DC801/BM-Badge/SD_Card/MAGE/docs_sources/docs/actions/LOOP_CAMERA_ALONG_GEOMETRY.md

# LOOP_CAMERA_ALONG_GEOMETRY

(might not work yet — instead, make a [null entity](../entity_types#null-entity) and lock the camera to it)

## Example JSON

```json
{
  "action": "LOOP_CAMERA_ALONG_GEOMETRY",
  "duration": 1000,
  "geometry": "vector object name"
}
```

## MGS Natlang

### Example

```mgs
script {
  loop camera along geometry "vector object name" over 1000ms;
}
```

### Dictionary entry

```
loop camera along geometry $geometry:string over $duration:duration (;)
```
