DC801/BM-Badge/SD_Card/MAGE/docs_sources/docs/actions/TELEPORT_CAMERA_TO_GEOMETRY.md

# TELEPORT_CAMERA_TO_GEOMETRY

Moves the camera to the first vertex of the specified [geometry object](../vector_objects).

## Example JSON

```json
{
  "action": "TELEPORT_CAMERA_TO_GEOMETRY",
  "geometry": "vector object name"
}
```

## MGS Natlang

### Example

```mgs
script {
  teleport camera to geometry "vector object name";
}
```

### Dictionary entry

```
teleport camera to geometry $geometry:string (;)
```
