DC801/BM-Badge/SD_Card/MAGE/scenario_source_files/mgs/ch2/ch2-PLANNING.md

# Chapter 2 planning

## Docs todos

- [ ] Turns out what makes a tile rotate weird when turning NSEW is whether the tile (whether it's a "character entity" or not) has an animation on it; not whether the tile has a Class/Type field value or whether it's listed in entity_types

## Generic work needing done

- [x] Make `go s` for `go south` an engine default alias (ditto for `sw` = `southwest`)
- [~] Tone down the alias logging in debug mode!
- [ ] Make the menu mage more chiseled (like last ch)
- [ ] Decide what to do with the null entity `door`, and be consistent about it
- [ ] Rename scripts so they're consistent
	- e.g. `ch2-interact-asdfasdf` should all be `interact-ch2-asdfasdf` -- or vice versa (pick one!)
- [x] Move Tiled files to the folders they should actually be (some entity JSON files are in the maps folder, etc.)
	- [x] And update all file paths in files that link to them, please!
- [ ] Turn off serial control during cutscenes
	- [ ] Determine which
	- [ ] Determine whether this should include all conversations
- [ ] For "failed" multiple choice responses, make the chunk of the dialog that gets repeated more logical and consistent
- [x] Check that every entity has an on_look script
- [x] Investigate and fix color pallet issues between tilesets (specifically grass in the castle/town tilesets, and the artifact cubby and the wall)
- [ ] Make aliases, e.g.:
	- [ ] `n` for `go north` (?)
	- [x] `i` for `inventory`
	- [x] `x`, `examine`, `l` for `look` etc.
- [~] ~~Make fuse system more interesting~~
	- [~] ~~Work out ≈ Cartesian product / Punnet squares for each grouping of combined items~~
	- [~] ~~Write something funny for each failed combo~~
	- (Re: above -- it's MVP now, and no time to change it much now)
	- [x] You need to fuse in person, at (one of the) the solder station(s)?
- [x] Make Lambda less hand-holdy at the beginning
	- [x] Explain `help` and `man` (both to reach Lambda and `man _`) and nothing else!
	- [ ] Did we go too far?? Make him hold more hands?
- [x] Put the "password" letters in the floor
	- [x] Take out the "look up" stuff
	- [x] Letters should spell AUTHENTICATE when spacially placed along the rooms they were found
	- [ ] Make sure the hint/context is ironclad!
- [x] Pair down the number of free computers in the place — gotta justify the need to build a weird one from scratch
- [ ] Change each individual "hide" script to set the object's on_tick to the "yeet" script instead so that all properties (not manually chosen ones) can be blanked in a uniform way
- [ ] Math book on_lock got skipped in RTFM room?

```
-------------------------------
|  /----\      -      CASTLE  |
|  |....|     /.\        MAP  |
|  ------   /..A..\           |
|           ---+---           |
|            |...|   -------  |
|   -----    |.U.|   |.T|H.|  |
|  /..E..\   |...|   --+-+--  |
|  \...../   |...|    |.N.|   |
|   --+--    --+--------+--   |
|   |.T.|    |.I.+...C....|   |
|   --+--------+-----------   |
|   |...A....+.T.|            |
|   -----------+----          |
|          |...E...|          |
|          ----+----          |
-------------------------------
```

## Specific work needing done

- [x] Teleport the player loading from save into the correct spot (overworld -> castle room #1)

## Story themes

- Chapter 2: Connections
	- Connecting past to future: sending ideas into the future, building long term communities, remembering lessons learned in the past
	- Connecting rooms to each other: building larger projects with cooperation, building/fixing infrastructure
	- Connecting people: allowing people to hear each other, build relationships; humans as social animals; networking leads to finding mentors and opportunities
	- The cost of isolation vs the cost of exposing oneself to bad actors
	- Connecting hardware: hardware is made up of smaller pieces, and many fixes are only a matter of connecting something to something else
	- AT THE END: Lambda is reconnected
- Chapter 3: Knowledge
	- Benefits of education
	- Learning to navigate the gray area rather than take a black and white answer at face value
	- Learning about one's environment
	- Leaning toolsets, how to best use everyday tools
	- Secrets to protect the vulnerable vs secrets to manipulate the vulnerable
	- IDEA: character named Chicago that speaks with that font

## Serial dialogs styles

- Before printing a fresh message to the serial console, show the serial dialog "spacer" -- this is currently a line break, a bunch of hyphens, and another line break. This makes it obvious where a new serial message begins.
- Empty serial messages must contain a single space or they will be ignored.

### Character conversations

- Identify speakers with `<color>SPEAKERNAME:</>` before their actual dialog message.
	- For `<color>`, use the speaker's color symbol (see below)
- Separate multiple speakers with an empty line.
- Additional paragraphs spoken by the same speaker should be indented with `\t`.
- Put an empty line between the last paragraph of dialog and a user input prompt.

### `on_look` scripts

- `look` must tell you things you can't ascertain from an entity's pixel art, scripting behavior, or dialog.
- Pay special attention to describing senses other than sight -- like smells, sounds -- but also broader information like the emotional atmosphere of a room and how people are acting around each other

See below for color choices.

#### Rooms

```mgs
look-ch2-roomname {
	show serial dialog spacer;
	show serial dialog {
		"You looked around the <c>NAME OF ROOM</>."
		"\t(description goes here)"
		"\t(extra paragraphs should also be tabbed, but try to avoid a lot of short paragraphs)"
		" "
	}
}
```

The extra line break at the end is only needed for places, since the exit list will follow the room's `on_look` script.

#### Entities

```mgs
look-ch2-roomname {
	show serial dialog spacer;
	show serial dialog {
		"You looked at <m>%EntityName%</>."
		// "You looked at the <m>%EntityName%</>." // for objects
		"\t(description goes here)"
		"\t(extra paragraphs should also be tabbed, but try to avoid a lot of short paragraphs)"
	}
}
```

Note the relative entity name for the label (i.e. wrapped in `%`s).

### Ansi Colors

- We can't know whether the user has a dark theme or a light theme, nor can we guarantee that all colors will be equally visible in their particular theme. Therefore, when needing arbitrary colors, prioritize them in this order:
	- Cyan/magenta (best)
	- Green/red
	- Blue/yellow (avoid)
	- Black/white (strong avoid)
- Do not use colors alone to convey information; if color coding something, also use other cues (capitalization, offsetting a word with with punctuation, etc.)
- Avoid using green/red as a point of contrast.
- Avoid using background colors or the "dim" style, since these are not as widely supported.
- Color symbols in ch2:
	- Magenta:
		- The village elders (the color of their robes)
		- Lambda
		- Any other person, really
	- Red:
		- The Big Bad
		- Anything unambiguously evil
	- Cyan:
		- The player (the color of mage's robe)
		- Inline serial commands (these should also be all caps)
		- Any calls to action for the player, akin to the above
		- The castle rooms (ch2 dungeon) (?)
			- Only the warp names are colored?
- In the web serial console, a styled section of text loses its styles after a newline character. As a workaround, reapply the style at the beginning of the first word that lost its styles.
- Currently, in the web build, the bell character is printed! (Like, as a boxy character, inline with other text.) Keep that in mind...
