DC801/BM-Badge/SD_Card/MAGE/editor/dependencies/tree-sitter-magegamescript/comparisons/mgs/ch2/ch2-map-PLANNING.md

# USB dungeon serial "map" (ideas)

```
Nethack-like
-------------------------------
|  /----\      -      CASTLE  |
|  |....|     /.\        MAP  |
|  ------   /.....\           |
|           -------           |
|            |...|   -------  |
|   -----    |...|   |.....|  |
|  /.....\   |...|   -------  |
|  \...../   |...|    |...|   |
|   -----    -------------|   |
|   |...|    |...|........|   |
|   -----------------------   |
|   |........|...|            |
|   |---------------          |
|          |...@...|          |
|          ---------          |
-------------------------------

 /----\      -
 | 99 |     / \
 ------   / 14  \
          -------  -------
  -----    |   |   |33|34|
 /     \   |13 |   -------
 \ 23  /   |   |    |32 |
  -----    --------------
  |22 |    |12 |    31  |
  |----------------------
  |   21   |11 |
  |---------------
         |   1   |
         ---------
```

## ROOMS

The room name (re: warping or other serial labelling) is what is contained within backtics.

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

### Entrance

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

### Admin Branch

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

### Industrial Area

21. `Workshop`
    - [~] Cutscene: Enter the room for the first time
    - [x] Inventory item: abacus (CPU part 2)
    - [x] Entity: Goose (with ribbon)
        - [ ] Should be involved with one of the puzzle items
    - [x] Entity: Jean-Paul - human-sized cockatiel; buds with Frankie
    - [x] Entity: Frankie - androgynous, Homestar Runner shirt-wearing tinkerer; buds with Jean-Paul
    - [x] SET: work room for fixing and making hardware (both old timey castle type hardware _and_ computer type hardware); disheveled, but not hopelessly so (everything is sort of in the right place, it's just all out at the moment)
22. `Server room`
    - [ ] Cutscene: Enter the room for the first time
    - [x] Inventory item: powersupply
    - [x] Entity: Scuzzy - generic conversation about the similarities between rooms in a building and components inside a computer
    - [x] Entity: C.K. Watt - gives you the power supply because it's extra
    - [x] SET: More cleanroom looking than the workshop
        - [x] Racks of machines
        - [x] Some computer buildery stuff (more computer, less electronics?)
23. `Power plant`
    - [x] Cutscene: Enter the room for the first time (not necessary)
    - [x] Inventory item: heatsink
    - [x] Entity: Tracy - generic engineer
    - [x] Entity: Rocco - to trade you the heat sink for a can of Cactus Cooler
    - [x] Entity: Helvetica - succubus, but you wouldn't know it from how she was acting; consummate professional engineer
    - [x] SET: Aiming for geothermal; whatever would sell that re: appearance

### Food

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

### The End

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

### Town

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

## ZONES

```
 0-------------------------------
 1|  /----\      -      CASTLE  |    99        14
 2|  |.@?.|     /.\        MAP  |    99        14
 3|  ------   /..@?.\           |    99        14
 4|           -------           |          13  14
 5|            |...|   -------  |          13              33  34
 6|   -----    |.@.|   |?@|@?|  |      23  13              33  34
 7|  /..@..\   |.?.|   -------  |      23  13          32  33  34
 8|  \..?../   |...|    |.@.|   |      23  13          32
 9|   -----    --------------   |  22  23  13  12  31  32
10|   |.@?|    |.@?|...@.?..|   |  22          12  31
11|   -----------------------   |  22  21  11  12  31
12|   |...@.?..|.@?|            |      21  11
13|   ----------------          |      21  11
14|          |...@...|          |          1
15|          ---------          |
16-------------------------------

with doors as pluses:
 0-------------------------------
 1|  /----\      -      CASTLE  |    99        14
 2|  |.@?.|     /.\        MAP  |    99        14
 3|  ------   /..@?.\           |    99        14
 4|           ---+---           |          13  14
 5|            |...|   -------  |          13              33  34
 6|   -----    |.@.|   |?@|@?|  |      23  13              33  34
 7|  /..@..\   |.?.|   --+-+--  |      23  13          32  33  34
 8|  \..?../   |...|    |.@.|   |      23  13          32
 9|   --+--    --+--------+--   |  22  23  13  12  31  32
10|   |.@?|    |.@?+...@.?..|   |  22          12  31
11|   --+--------+-----------   |  22  21  11  12  31
12|   |...@.?..+.@?|            |      21  11
13|   -----------+----          |      21  11
14|          |...@...|          |          1
15|          ----+----          |
16-------------------------------
```

## STORY PROGRESSION

(Only numbered items count as story flags)

Choose which "round" with the `ch2_storyflag_round` variable. Checkboxes refer to script scaffolding (the exact convos may be still unwritten); see `ch2-PLANNING.md` for the sprites checklist.

In debug mode, you can use the command `storyflag` to set this arbitrarily for testing purposes.

### Plot

Plot points implemented:

- INTRO (`ch2_storyflag_round` = 0)

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

- FIRST ROUND: normal (`ch2_storyflag_round` = 1)

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

- SECOND ROUND: abstract (`ch2_storyflag_round` = 2)

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

- THIRD ROUND: desperate (`ch2_storyflag_round` = 3)

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

- FINAL ROUND: software (`ch2_storyflag_round` = 4)

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

- AFTERWARD (`ch2_storyflag_round` = 5)
    - [x] Post-credits sequence: Alfonso mentions one of the Big Bad's powers that most people don't know about
    - [~] Go about the overworld now

### Village elder locations

ALL DONE!

- INTRO (`ch2_storyflag_round` = 0)
    - [x] All outside castle entrance
    - [x] All encouraging you
- FIRST ROUND: normal (`ch2_storyflag_round` = 1)
    - [x] Alfonso: in the library, getting distracted by random books on accident
    - [x] Jackob: in the library, in a staring contest with the goose
    - [x] Bert: in the inner sanctum, looking for the book they lost
    - Bert visits you
- SECOND ROUND: abstract (`ch2_storyflag_round` = 2)
    - [x] Alfonso: talking to Verthandi
    - [x] Jackob: in the bakery, shopping for fresh bread
- THIRD ROUND: desperate (`ch2_storyflag_round` = 3)
    - [x] Jackob in inner sanctum, worried about the time you are taking
    - [x] Alfonso in inner sanctum, worried about Bert
- FINAL ROUND: software (`ch2_storyflag_round` = 4)
    - [x] Jackob/Alfonso waiting outside
    - [x] Jackob/Alfonso urging you to finish
- AFTERWARD (`ch2_storyflag_round` = 5)
    - [x] In the main square
    - [x] Mention how you can have a break now
        - [x] If you haven't beaten part 1, Jackob invites you to do so now

### Villager dialog

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

- INTRO (`ch2_storyflag_round` = 0)
    - [ ] Villagers direct you to western dungeon (castle)
- FIRST ROUND: normal (`ch2_storyflag_round` <= 2)
    - [ ] Villagers ask how things are going
- THIRD ROUND: desperate (`ch2_storyflag_round` <= 4)
    - [ ] Player asks villages about Bert; they haven't seen him
- AFTERWARD (`ch2_storyflag_round` <= 5)
    - [ ] Speculate on next location: software!

Use this template:

```
if (variable ch2_storyflag_round is 0) {
	show dialog {
	// hint at western dungeon
	}
} else if (variable ch2_storyflag_round is <= 2) {
	show dialog {
	// asks how things are going
	}
} else if (variable ch2_storyflag_round is <= 4) {
	show dialog {
	// player asks after Bert; entity hasn't seen him
	}
} else {
	show dialog {
	// congratulate player for winning; speculate on next dungeon
	}
}
```

Villagers:

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

Entities not being used right now: (maybe use them?)

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

### Lambda conversations

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

### Scripts needed for story items

ALL DONE! (Probably)

For each item: (Copy existing pattern wherever these are found)

1. Put entity on a map (`ENTITY`) and set `on_interact` = `ch2_touch_ITEM`
2. In file `ch2/ch2-admin.mgs`:
    1. Script `command_inventory` — Add serial dialog `\tITEM` display check (using flag `ch2_carrying_ITEM`)
    2. Script `ch2_count_flags` — Add tally logic check (using flag `ch2-installed-ITEM`)
    3. Script `interact_ch2_mainframe` — Add installation dialog (using flags `ch2_installed_ITEM` and `ch2_carrying_ITEM`)
3. In script file for the map room:
    1. Room's `on_load` — Add entity hide behavior (using flags `ch2_installed_ITEM` and `ch2_carrying_ITEM`)
    2. Make script `ch2_hide_ITEM`
        - `teleport entity ENTITY to geometry hiding-spot`
        - `set entity ENTITY name to " "`
    3. Make script `ch2_touch_ITEM`
        - (Copy existing pattern)
    4. Make script `ch2_install_ITEM`
        - `set flag ch2_carrying_ITEM to false`
        - `set flag ch2_installed_ITEM to true`
    5. Make script `look-ITEM`
4. In file `ch2/ch2-serial-toot.mgs`
    1. Make serial dialog `ch2_describe_ITEM`
    2. Add a new substep to script `ch2_toot_step_5X`
5. In file `commands/command-parts.mgs`
    1. Make script `ch2_describe_ITEM`: `show serial dialog ch2_describe_ITEM`
    2. Make script `command_parts_ITEM` (copy an existing)
    3. Add to `command-parts` (using flag `ch2_installed_ITEM` and `ch2_carrying_ITEM`)
    4. Add to script `command_parts_q` (if multiple words, add a no-spaces option, too)

Other notes:

- `ch2_hide_X` concerns moving the entity itself around the physical game map; `ch2_pickup_X` and `ch2_install_X` concern setting flags to make the item appear on the ASCII serial map, serial inventory list, etc.

## Puzzles to implement

(Also see the brainstorming far below)

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

Other things:

- [ ] Regular full computer desktop: (Atari ST? System 6?)

### Lost woods

Room count: 12 rooms (not counting 99)

```
#####   #####          ===>     ##### U #####          ===>     #$##?   ?####
#####   #####          ===>     #####   #####          ===>     ?##$#   ###$#
#####   #####          ===>     #####   #####          ===>     #$###   #$###
      @                ===>     L     @     R          ===>           @
#####   #####          ===>     #####   #####          ===>     ##$##   ?##$#
#####   #####          ===>     #####   #####          ===>     #$###   #$#?#
#####   #####          ===>     ##### D #####          ===>     ###?#   ##$##

#$##?   ?####
?##$#   ###$#
#$###   #$###
      @
##$##   ?##$#
#$###   #$#?#
###?#   ##$##

#####   #####           #####   #####           #############           #####   #####
#####   #####           #####   #####           #############           #####   #####
#####   #####           #####   #####           #############           #####   #####
      @ #####           ##### @                       @                       @
#####   #####           #####   #####           #####   #####           #############
#####   #####           #####   #####           #####   #####           #############
#####   #####           #####   #####           #####   #####           #############

#############           #####   #####           #####   #####           #############           #####   #####           #############
#############           #####   #####           #####   #####           #############           #####   #####           #############
#############           #####   #####           #####   #####           #############           #####   #####           #############
      @ #####                 @ #####           ##### @                 ##### @                 ##### @ #####                 @
#####   #####           #############           #############           #####   #####           #####   #####           #############
#####   #####           #############           #############           #####   #####           #####   #####           #############
#####   #####           #############           #############           #####   #####           #####   #####           #############
```

## Puzzle Mechanics

### Serial terminal: things we can do

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

### Serial terminal: things we can't do

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

#### Goals / issues

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

## Educational Angles (Brainstorming again)

BRAINSTORMING: In terms of the player accidentally learning something about CS:

### What we use terminals for IRL

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

### Installing Linux

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

### Things unique to the badge itself

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

## Other stuff

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
