DC801/BM-Badge/Hardware/ART/2020/images/ART-2020-quarter.png

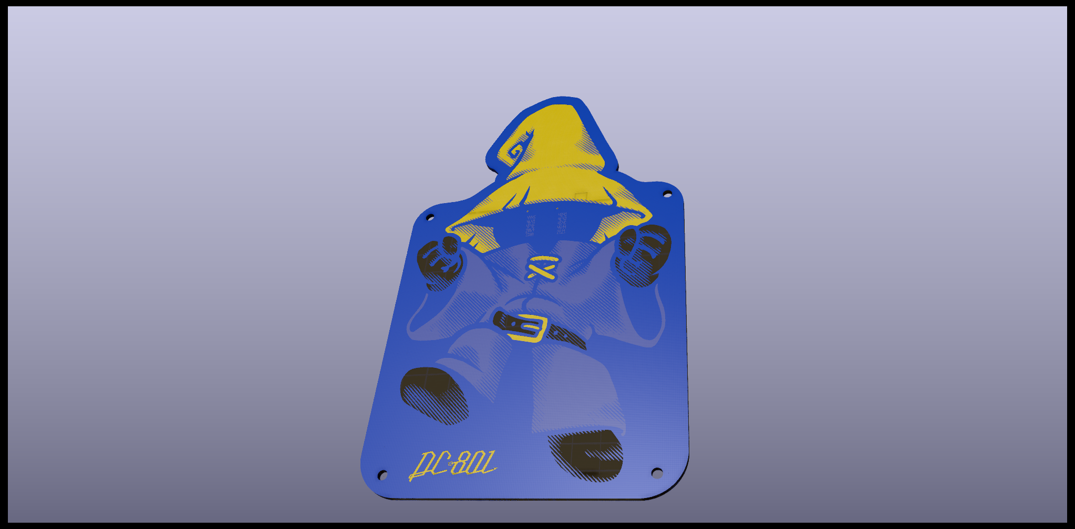
Hardware/ART/2020/images/ART-2020-quarter.png
