DC801/BM-Badge/Hardware/ART/2020/images/ART_Copper.png

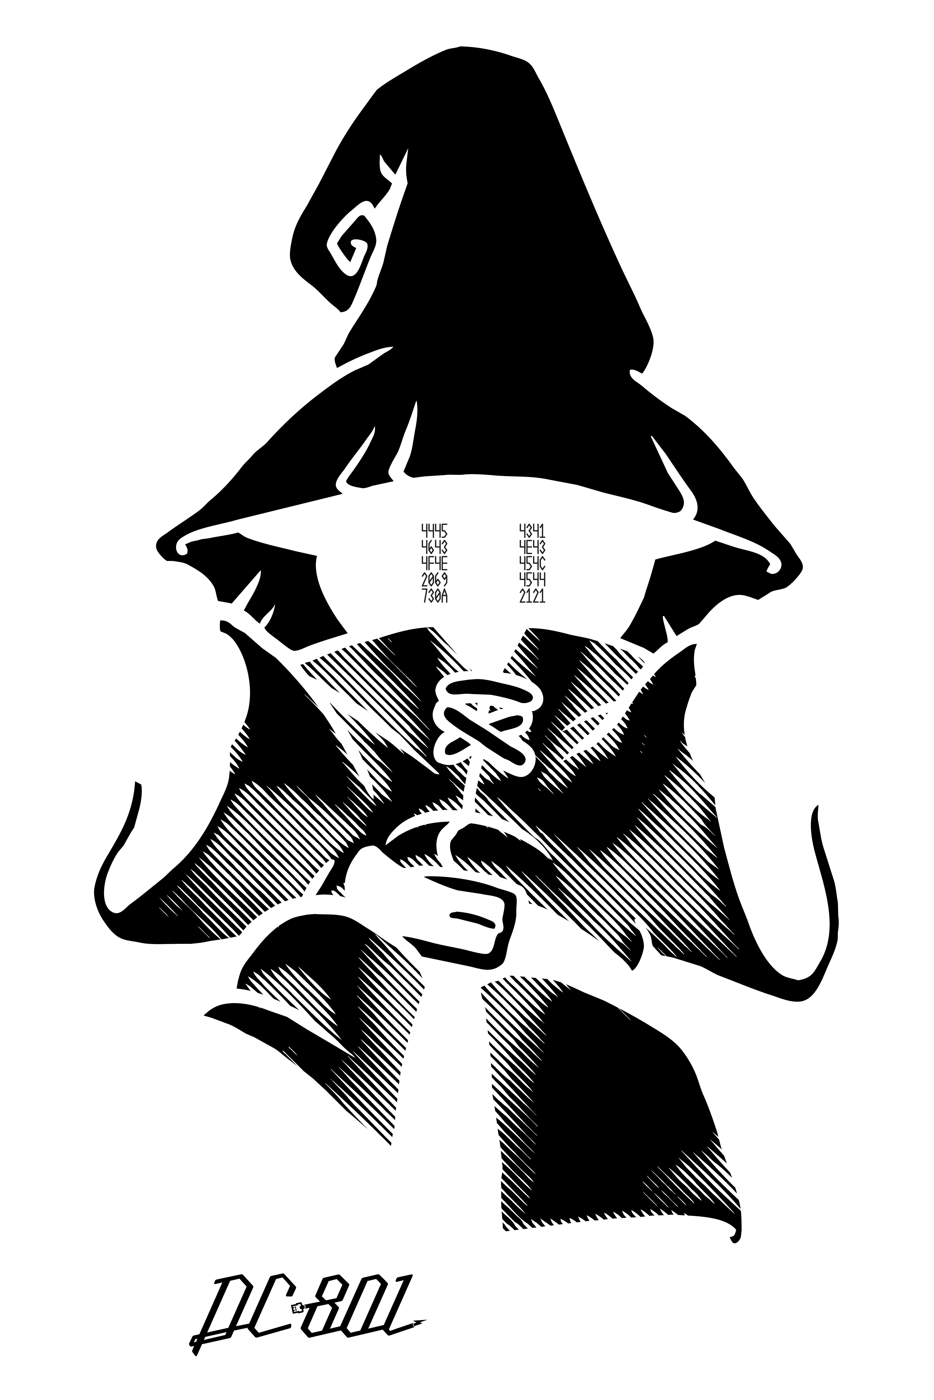
Hardware/ART/2020/images/ART_Copper.png
