DC801/BM-Badge/Hardware/ART/2020/images/ART_Outline.png

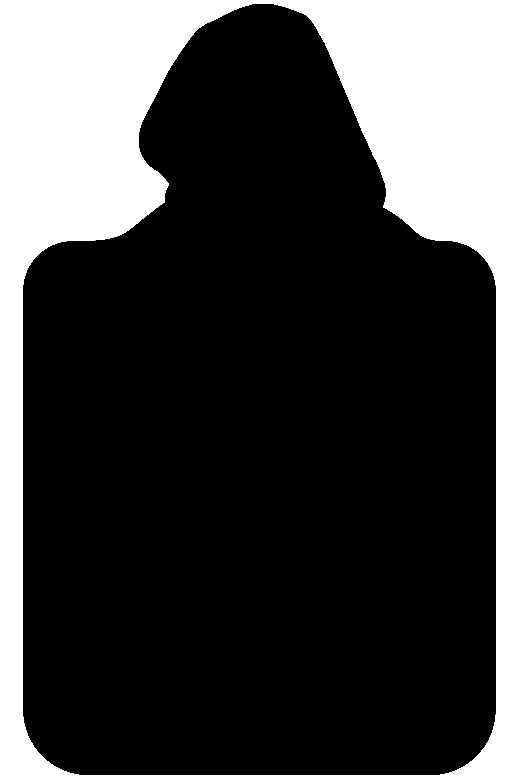
Hardware/ART/2020/images/ART_Outline.png
