DC801/BM-Badge/Hardware/ART/2020/images/ART_Preview.png

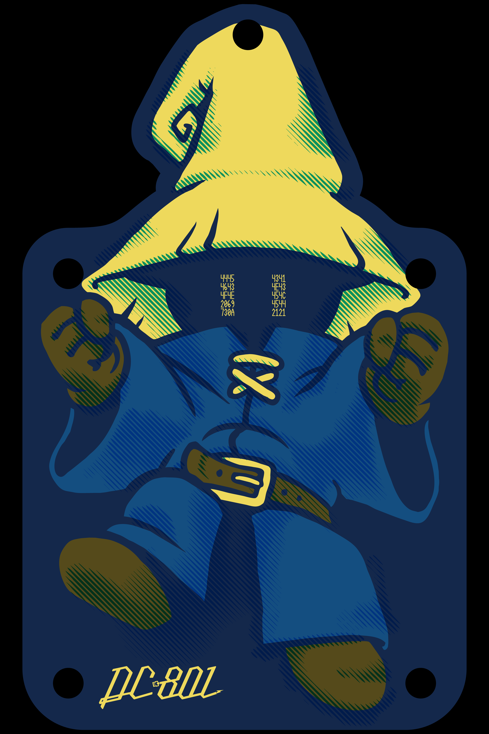
Hardware/ART/2020/images/ART_Preview.png
