DC801/BM-Badge/Hardware/BackBoard Pogo Jig/images/FrontSilk.png

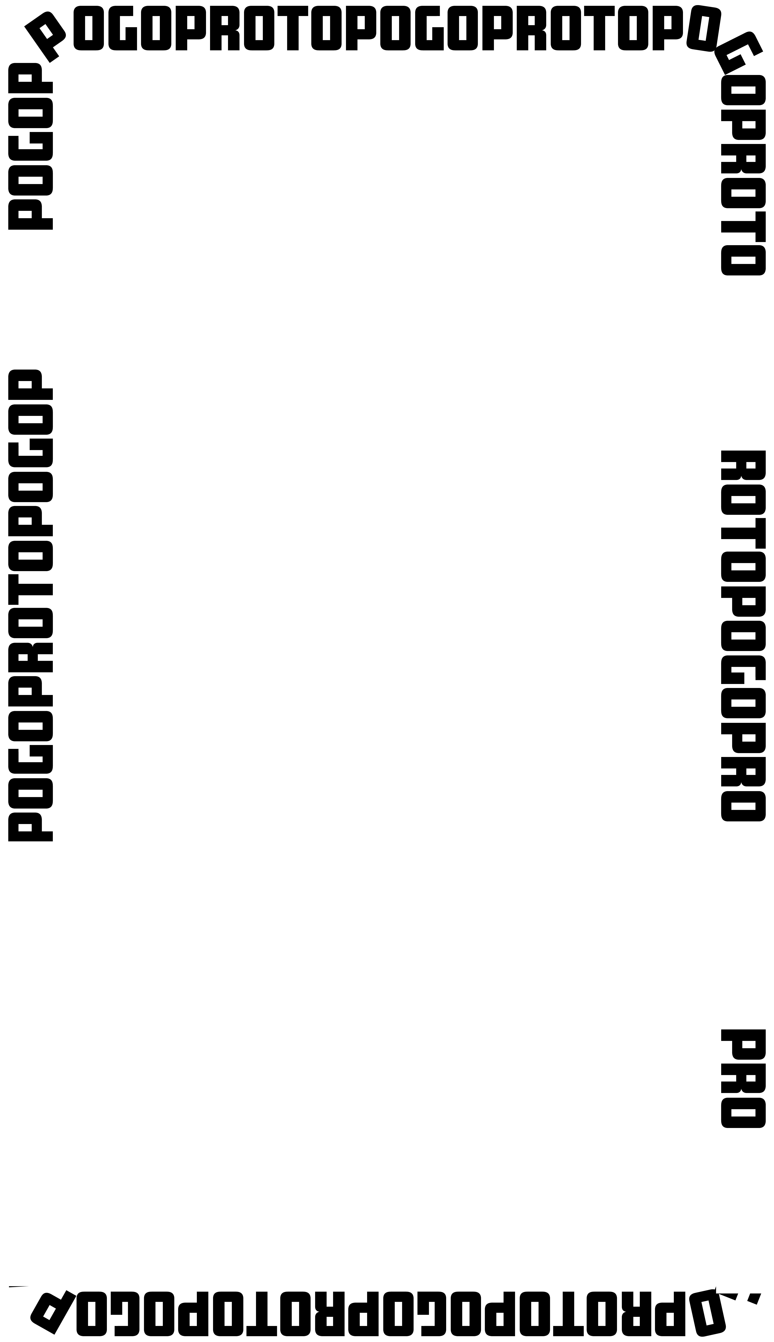
Hardware/BackBoard Pogo Jig/images/FrontSilk.png
