DC801/BM-Badge/Hardware/BackBoard Pogo Jig/images/purplewizard-pogo-back.png

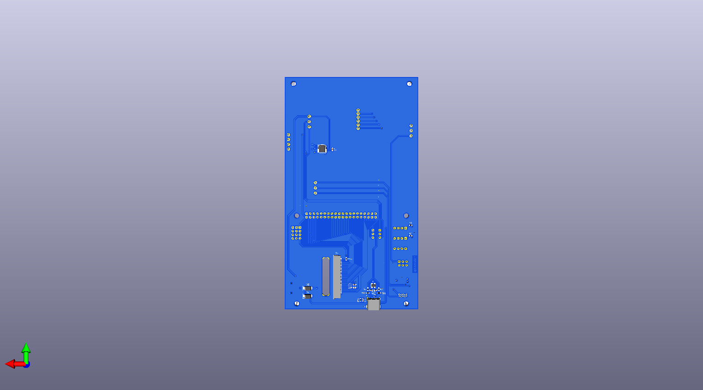
Hardware/BackBoard Pogo Jig/images/purplewizard-pogo-back.png
