DC801/BM-Badge/Hardware/BackBoard/images/back-board_Copper.png

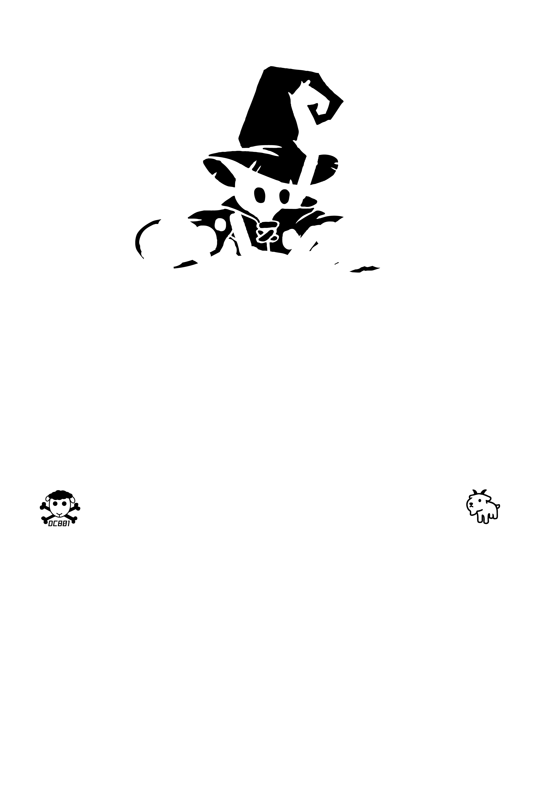
Hardware/BackBoard/images/back-board_Copper.png
