DC801/BM-Badge/Hardware/BackBoard/images/back-board_Silkscreen.png

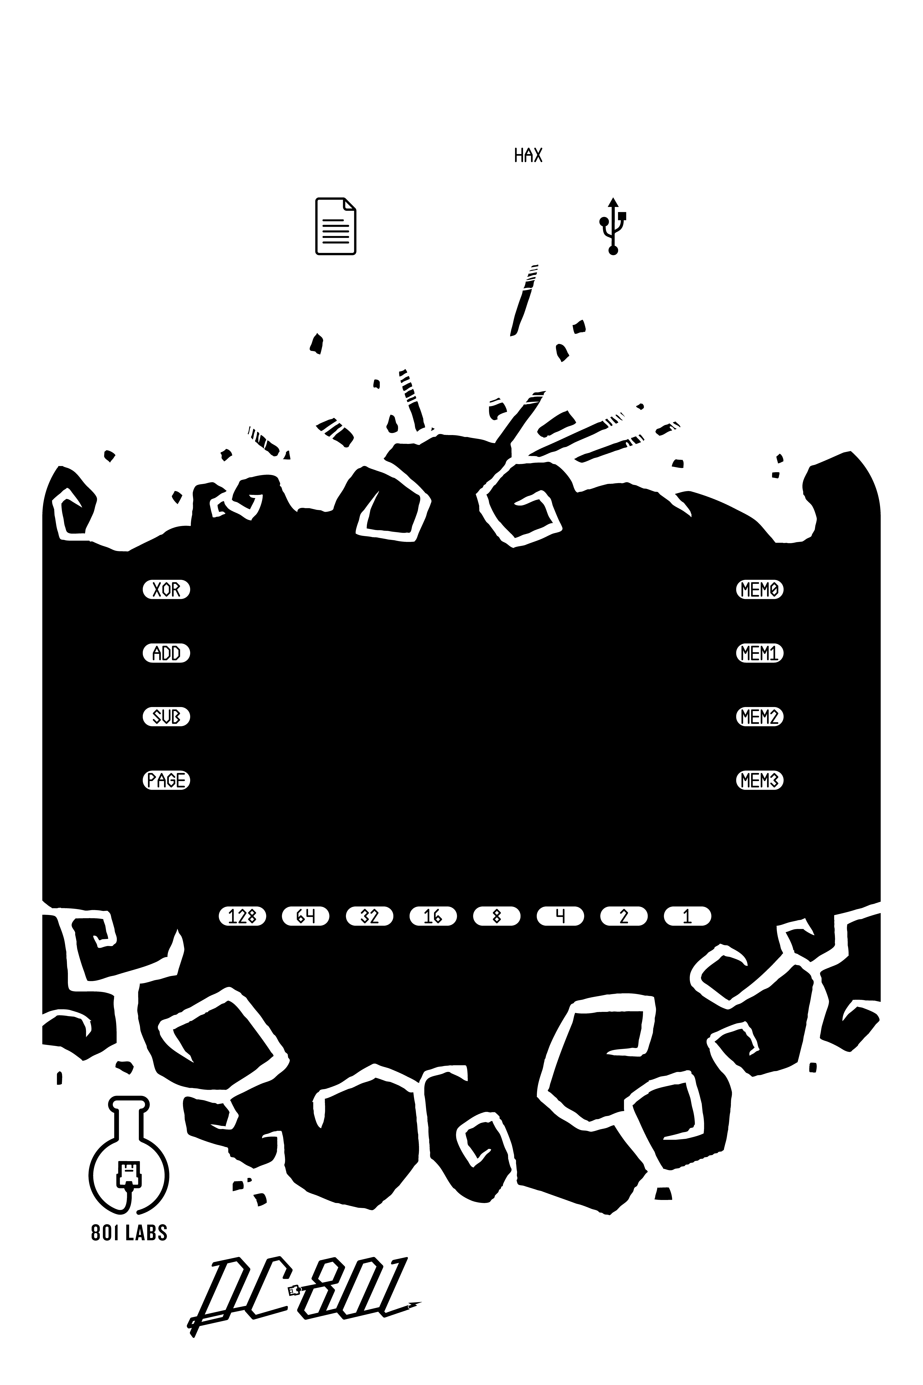
Hardware/BackBoard/images/back-board_Silkscreen.png
