DC801/BM-Badge/Hardware/BackBoard/images/purplewizard-backboard-back.png

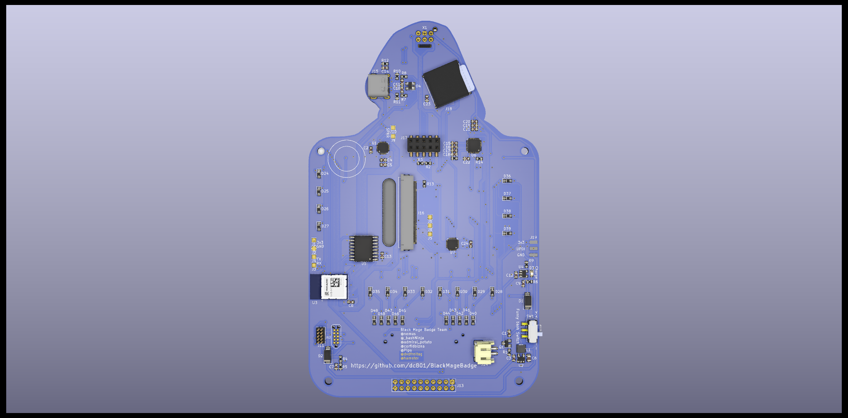
Hardware/BackBoard/images/purplewizard-backboard-back.png
