DC801/BM-Badge/Hardware/BackBoard/images/purplewizard-backboard-front-quarter.png

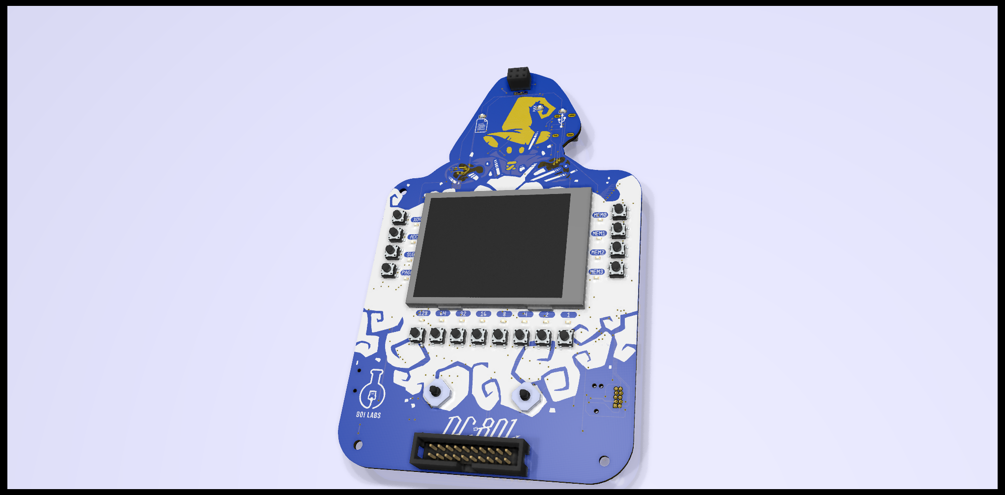
Hardware/BackBoard/images/purplewizard-backboard-front-quarter.png
