DC801/BM-Badge/Hardware/BackBoard/outputs/Panel-1.0/purplewizard_Combined_Bottom.png

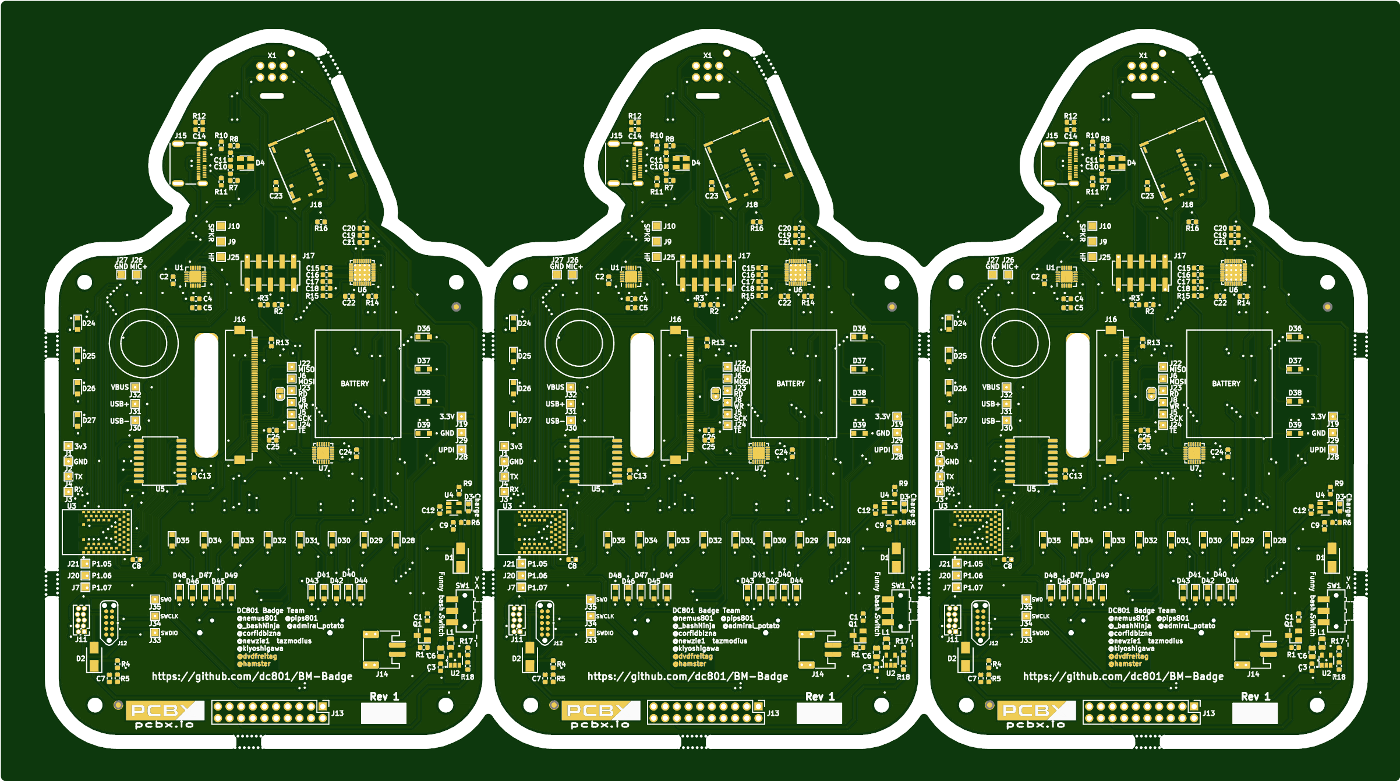
Hardware/BackBoard/outputs/Panel-1.0/purplewizard_Combined_Bottom.png
