DC801/BM-Badge/SD_Card/MAGE/desktop_assets/window_frame.png

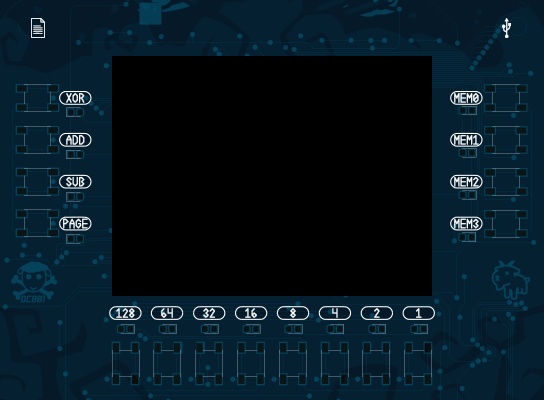
SD_Card/MAGE/desktop_assets/window_frame.png
