DC801/BM-Badge/SD_Card/MAGE/docs_sources/docs/media/main-menu.gif

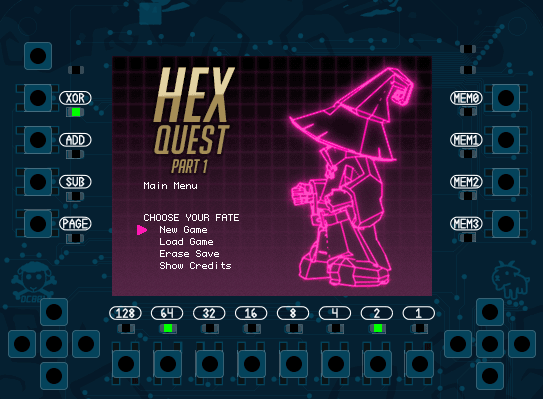
SD_Card/MAGE/docs_sources/docs/media/main-menu.gif
