DC801/BM-Badge/SD_Card/MAGE/editor/dependencies/MageDance.gif

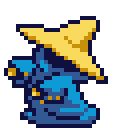
SD_Card/MAGE/editor/dependencies/MageDance.gif
