DC801/BM-Badge/SD_Card/MAGE/scenario_source_files/entities/entity-beetle.png

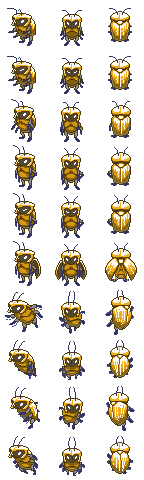
SD_Card/MAGE/scenario_source_files/entities/entity-beetle.png
