DC801/BM-Badge/SD_Card/MAGE/scenario_source_files/entities/entity-codec-portrait.png

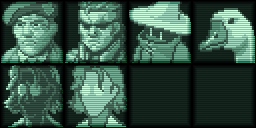
SD_Card/MAGE/scenario_source_files/entities/entity-codec-portrait.png
