DC801/BM-Badge/SD_Card/MAGE/scenario_source_files/entities/entity-eye_faerie.png

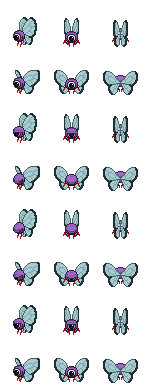
SD_Card/MAGE/scenario_source_files/entities/entity-eye_faerie.png
