DC801/BM-Badge/SD_Card/MAGE/scenario_source_files/entities/entity-golem.png

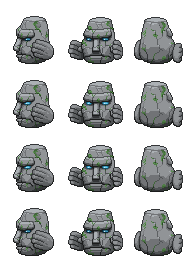
SD_Card/MAGE/scenario_source_files/entities/entity-golem.png
