DC801/BM-Badge/SD_Card/MAGE/scenario_source_files/entities/entity-marathon-bob.png

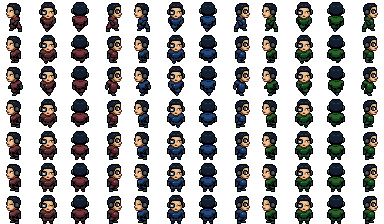
SD_Card/MAGE/scenario_source_files/entities/entity-marathon-bob.png
