DC801/BM-Badge/SD_Card/MAGE/scenario_source_files/entities/portraits-nonhuman.png

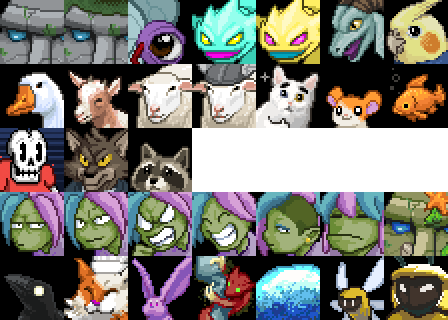
SD_Card/MAGE/scenario_source_files/entities/portraits-nonhuman.png
