DC801/BM-Badge/SD_Card/MAGE/scenario_source_files/entities/portraits-people.png

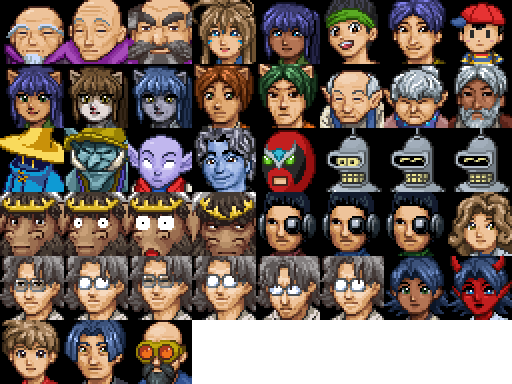
SD_Card/MAGE/scenario_source_files/entities/portraits-people.png
