DC801/BM-Badge/SD_Card/MAGE/scenario_source_files/tilesets/tileset-ch2-menu-background.gif

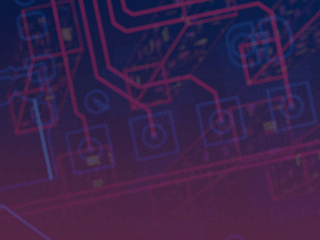
SD_Card/MAGE/scenario_source_files/tilesets/tileset-ch2-menu-background.gif
