DC801/BM-Badge/SD_Card/MAGE/scenario_source_files/tilesets/tileset-ch2-menu-dc801_bling.gif

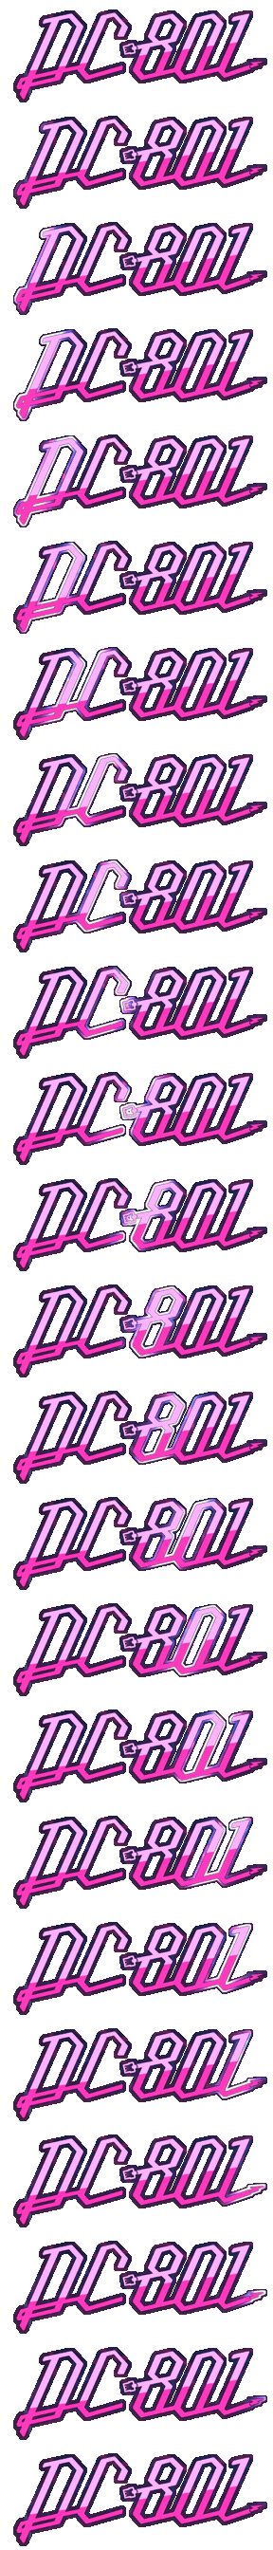
SD_Card/MAGE/scenario_source_files/tilesets/tileset-ch2-menu-dc801_bling.gif
