DC801/BM-Badge/SD_Card/MAGE/scenario_source_files/tilesets/tileset-colllision_64x64.png

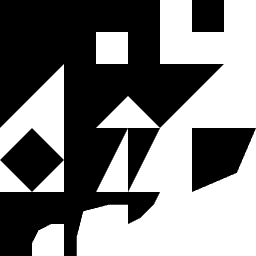
SD_Card/MAGE/scenario_source_files/tilesets/tileset-colllision_64x64.png
