DC801/BM-Badge/SD_Card/MAGE/scenario_source_files/tilesets/tileset-greenhouse.png

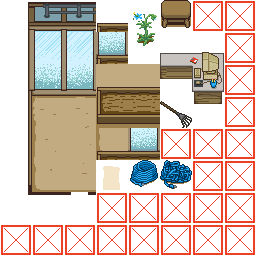
SD_Card/MAGE/scenario_source_files/tilesets/tileset-greenhouse.png
