DC801/BM-Badge/SD_Card/MAGE/scenario_source_files/tilesets/tileset-main_menu-animation.png

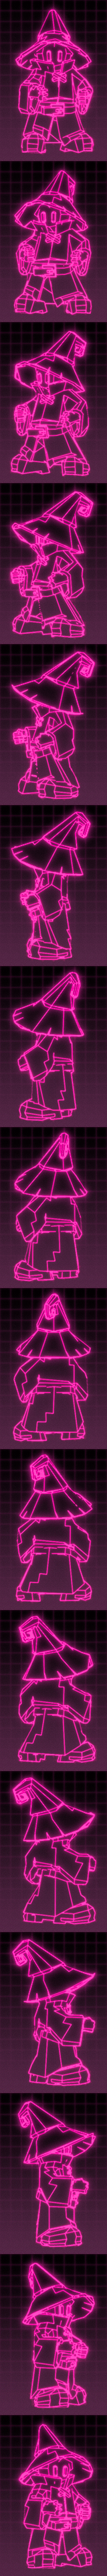
SD_Card/MAGE/scenario_source_files/tilesets/tileset-main_menu-animation.png
