DC801/BM-Badge/SD_Card/MAGE/scenario_source_files/tilesets/tileset-monstrosity.png

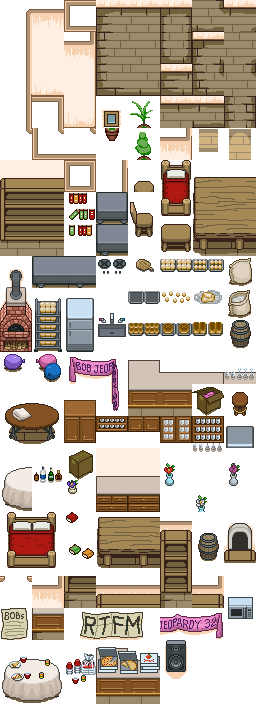
SD_Card/MAGE/scenario_source_files/tilesets/tileset-monstrosity.png
