DC801/BM-Badge/SD_Card/MAGE/scenario_source_files/tilesets/tileset-qr.png

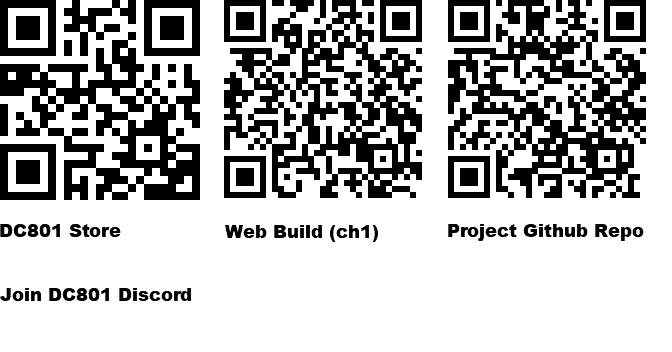
SD_Card/MAGE/scenario_source_files/tilesets/tileset-qr.png
