DC801/BM-Badge/SD_Card/MAGE/scenario_source_files/tilesets/tileset-ring_zero.gif

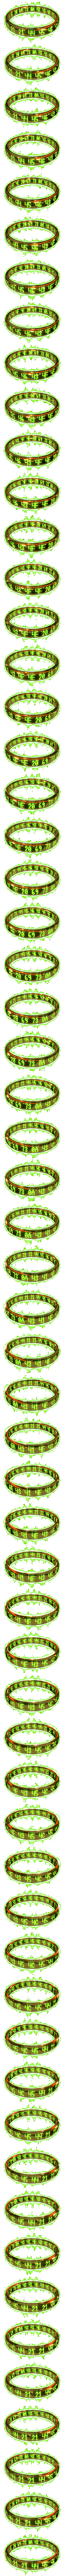
SD_Card/MAGE/scenario_source_files/tilesets/tileset-ring_zero.gif
