DC801/BM-Badge/SD_Card/MAGE/scenario_source_files/tilesets/tileset-secretroom.png

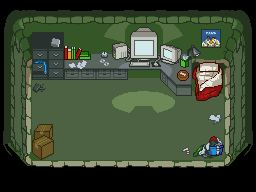
SD_Card/MAGE/scenario_source_files/tilesets/tileset-secretroom.png
