DC801/BM-Badge/SD_Card/MAGE/scenario_source_files/tilesets/tileset_interior.png

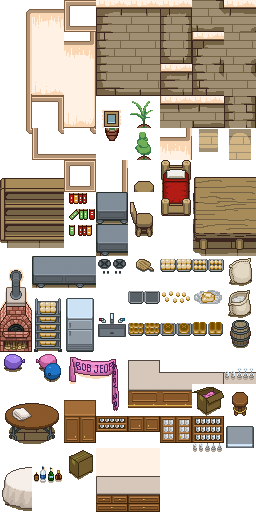
SD_Card/MAGE/scenario_source_files/tilesets/tileset_interior.png
