DC801/BM-Badge/Hardware/ART/2020/images/ART_Soldermask.png

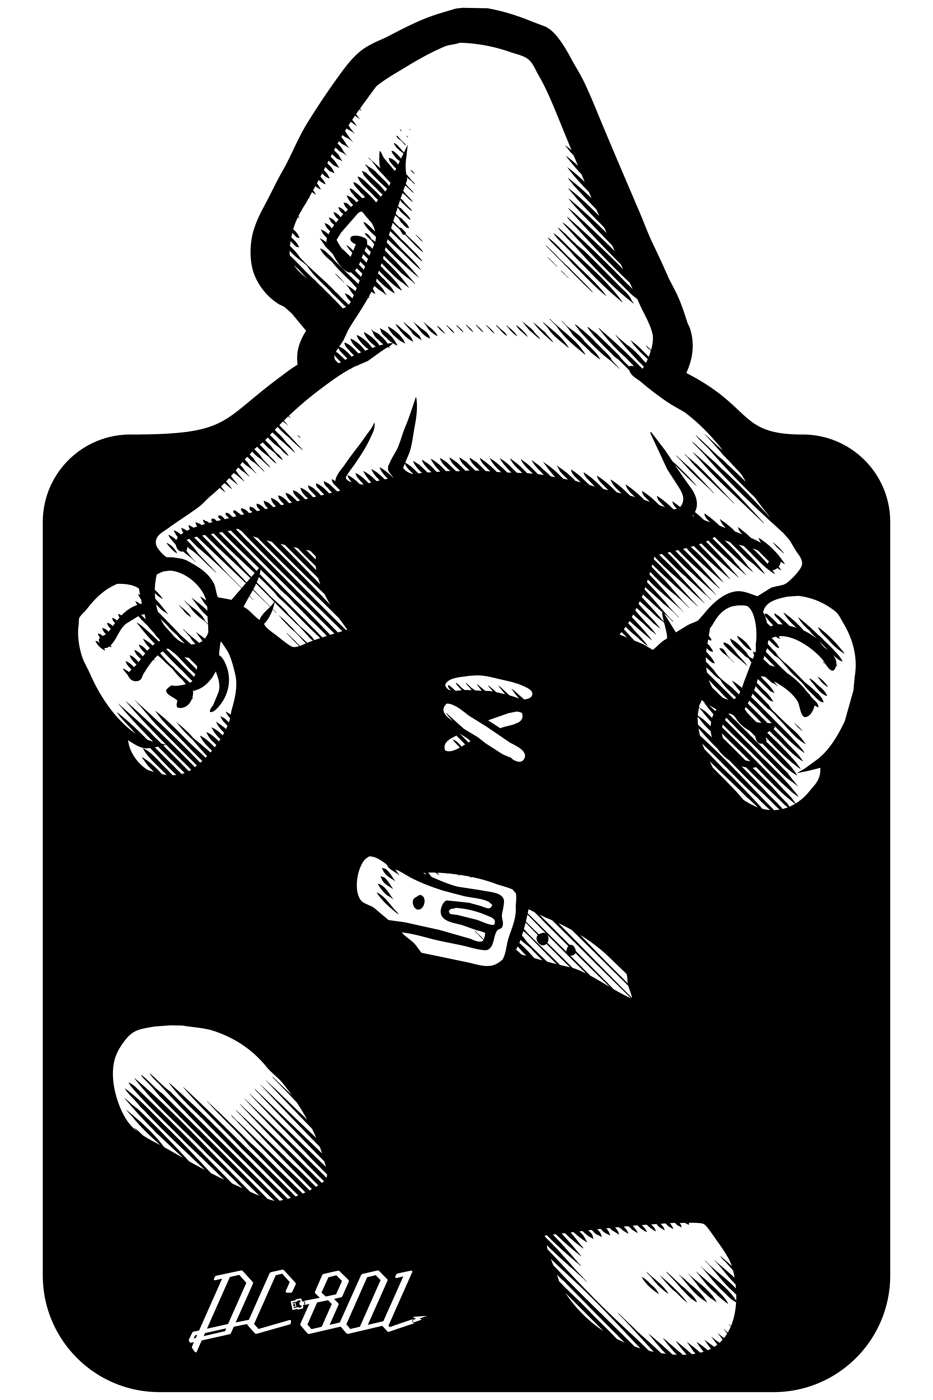
Hardware/ART/2020/images/ART_Soldermask.png
