DC801/BM-Badge/Hardware/BackBoard/images/back-board_Soldermask.png

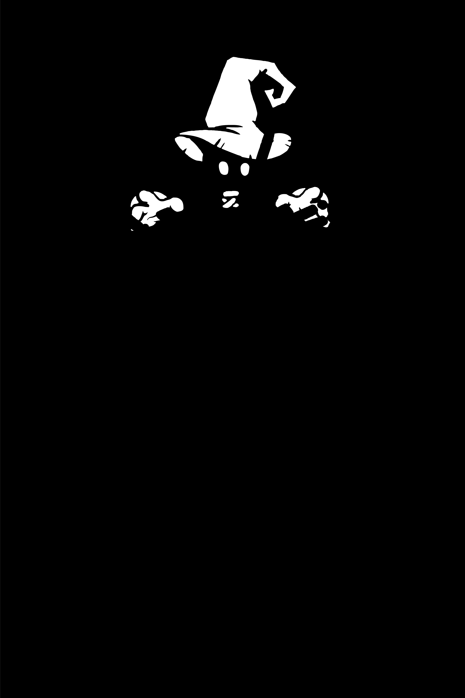
Hardware/BackBoard/images/back-board_Soldermask.png
