DC801/BM-Badge/Hardware/SAOs/2022 MiniMage/images/SAO-2022_spells_1_Back Solder Mask.png

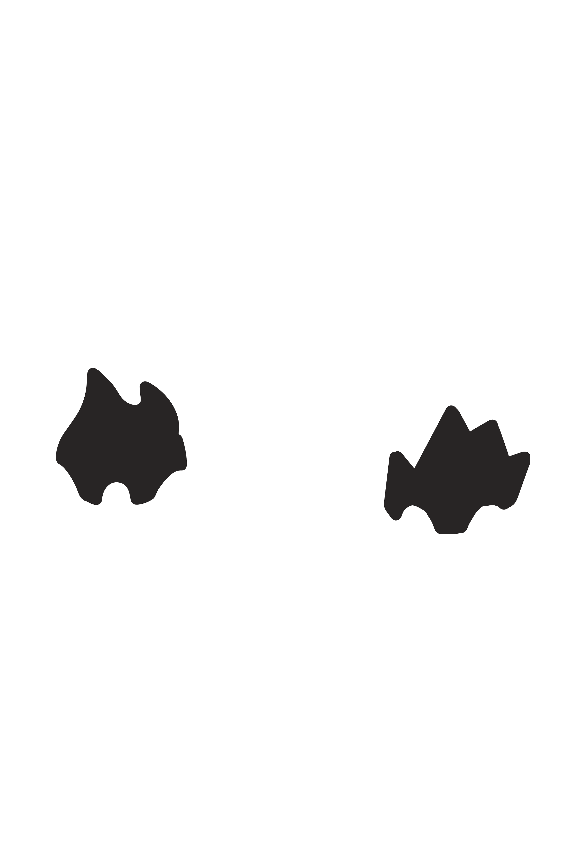
Hardware/SAOs/2022 MiniMage/images/SAO-2022_spells_1_Back Solder Mask.png
