DC801/BM-Badge/SD_Card/MAGE/scenario_source_files/tilesets/tileset-numbered_testing.png

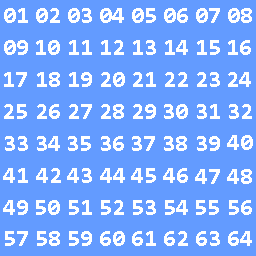
SD_Card/MAGE/scenario_source_files/tilesets/tileset-numbered_testing.png
