DC801/BM-Badge/Hardware/ART/2020/output/purplewizard-ART-B_CrtYd.pdf

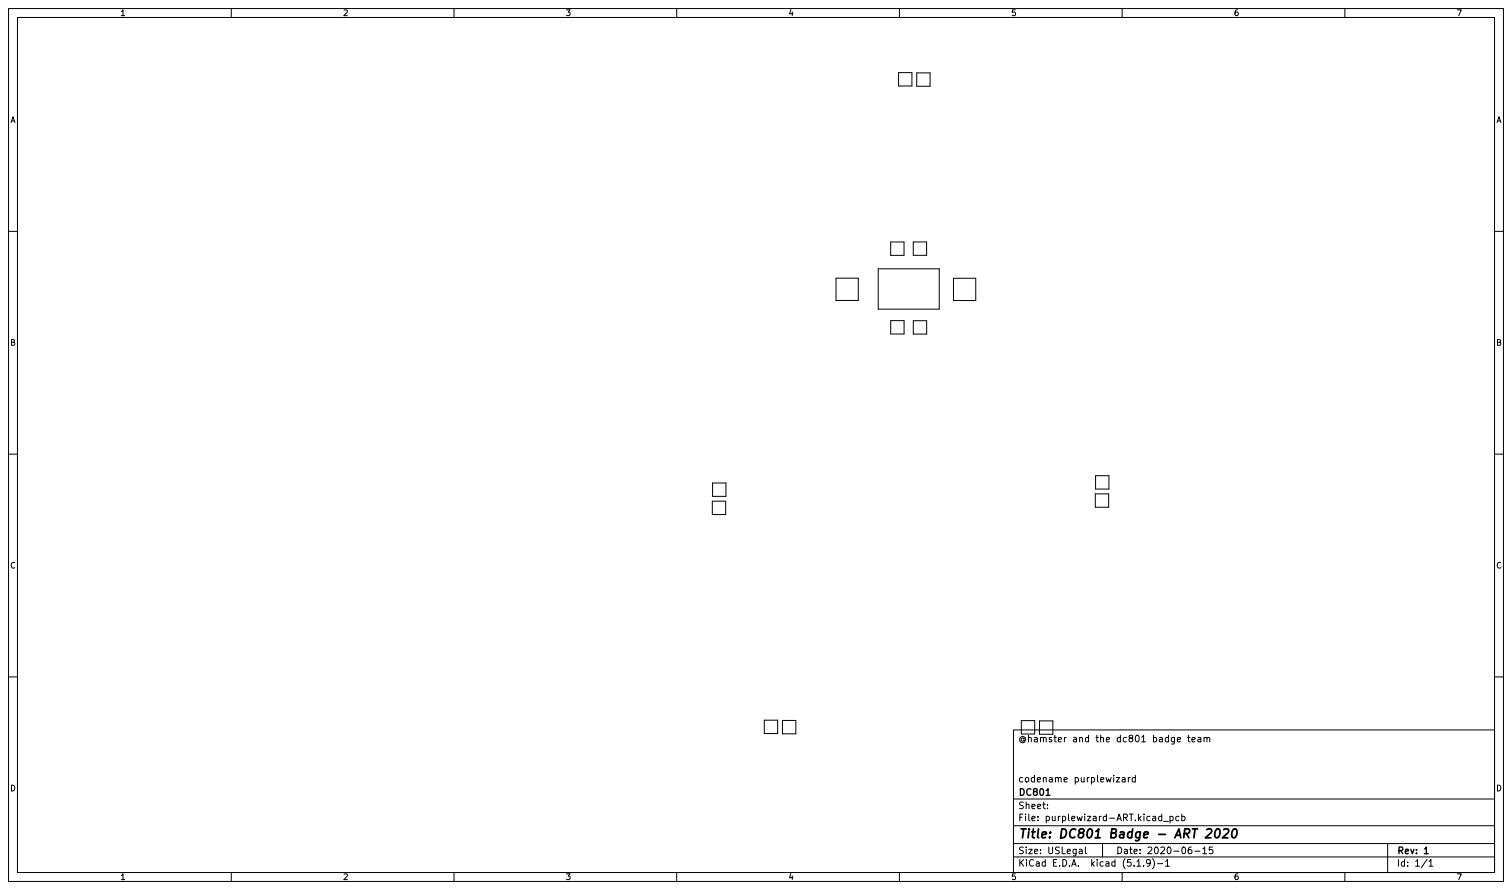
[picture p103: page 1]

@hamster and the dc801 badge team

codename purplewizard
D Date: 2020-06-15 KiCad E.D.A. kicad (5.1.9)-1
File: purplewizard-ART.kicad_pcb Sheet: DC801

Id: 1/1 Title: DC801 Badge - ART 2020
