DC801/BM-Badge/Hardware/ART/2020/output/purplewizard-ART-B_Fab.pdf

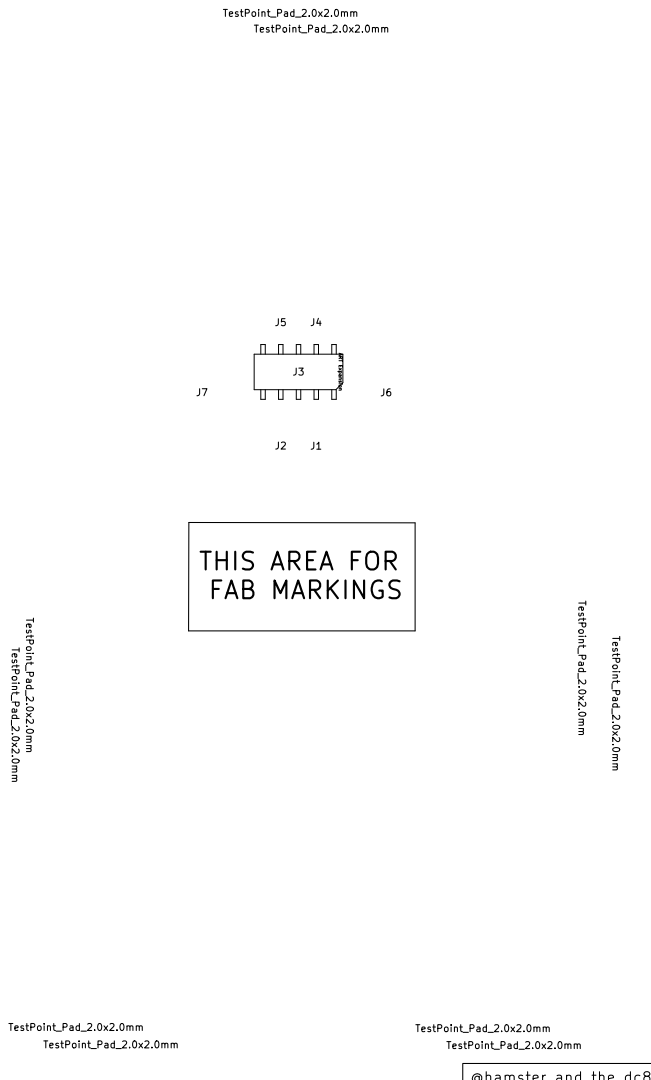
[picture p104: page 1]

codename purplewizard
File: purplewizard-ART.kicad_pcb Sheet: DC801

Id: 1/1 Title: DC801 Badge - ART 2020
