DC801/BM-Badge/Hardware/ART/2020/output/purplewizard-ART-B_SilkS.pdf

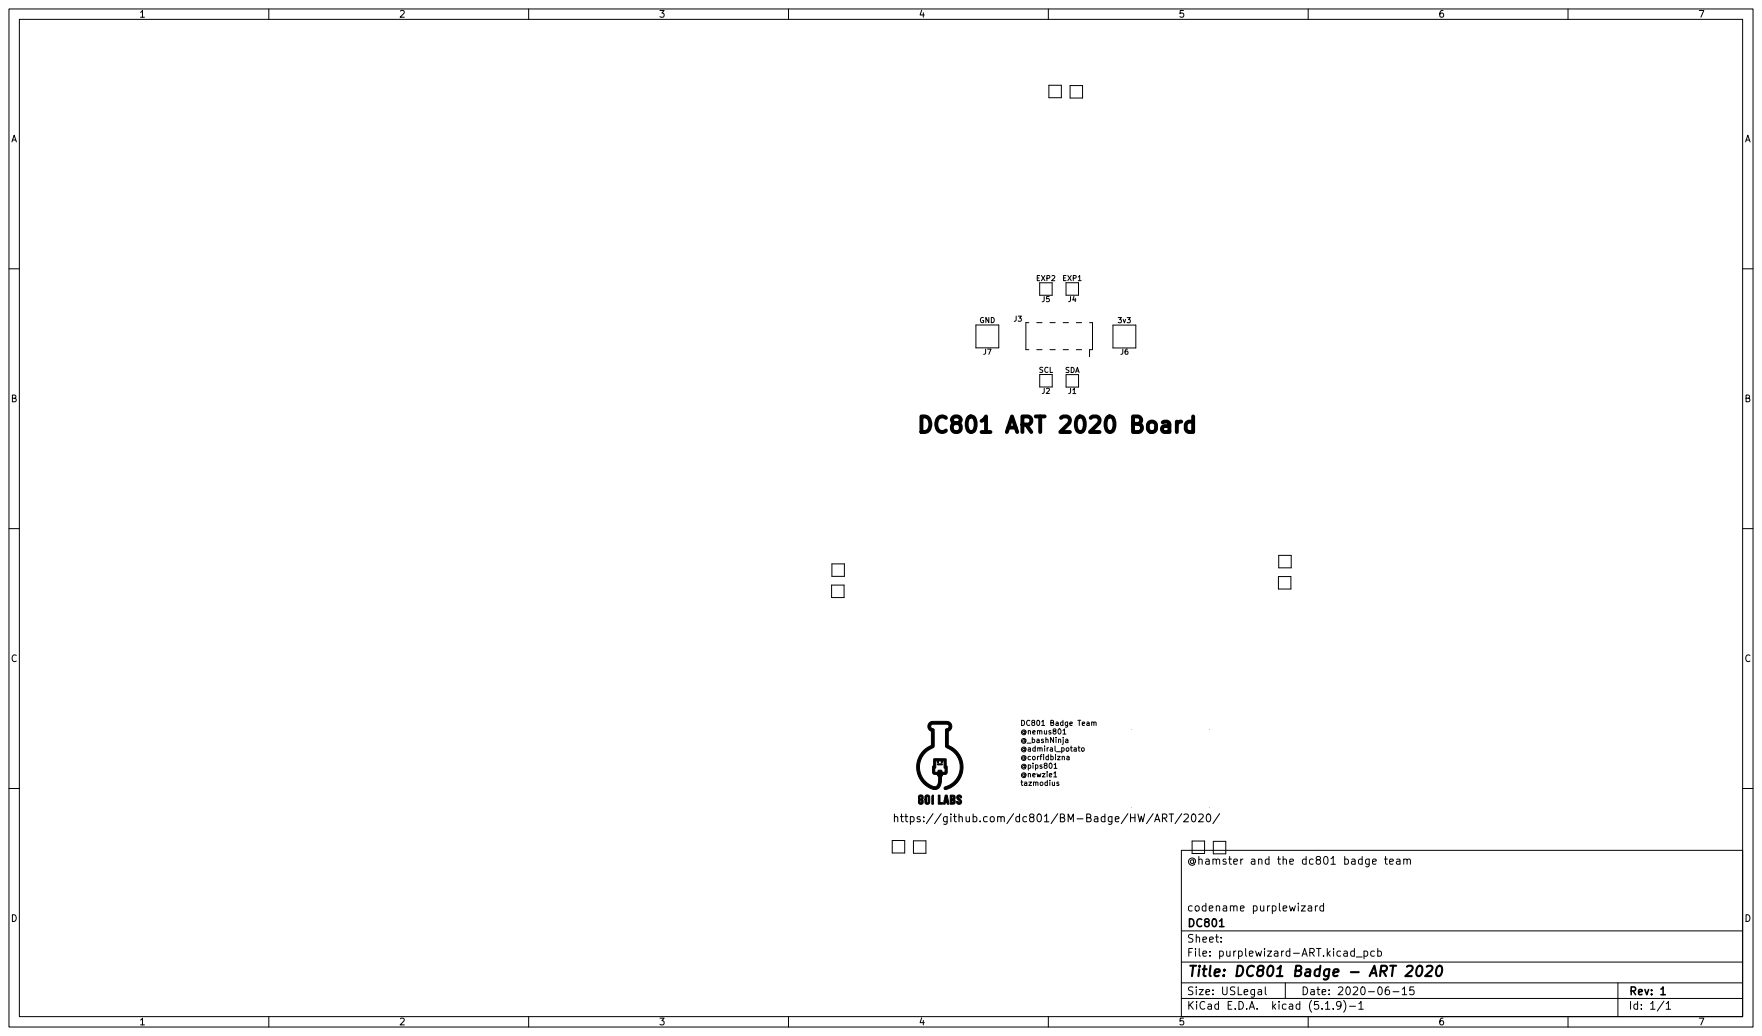
[picture p105: page 1]

https://github.com/dc801/BM-Badge/HW/ART/2020/ DC801 Badge Team @nemus801 @_bashNinja @admiral_potato @corfidbizna @pips801 @newzie1

@hamster and the dc801 badge team

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

Id: 1/1 Title: DC801 Badge - ART 2020
