DC801/BM-Badge/Hardware/BackBoard/outputs/Final-1.0/purplewizard-final-complete.pdf

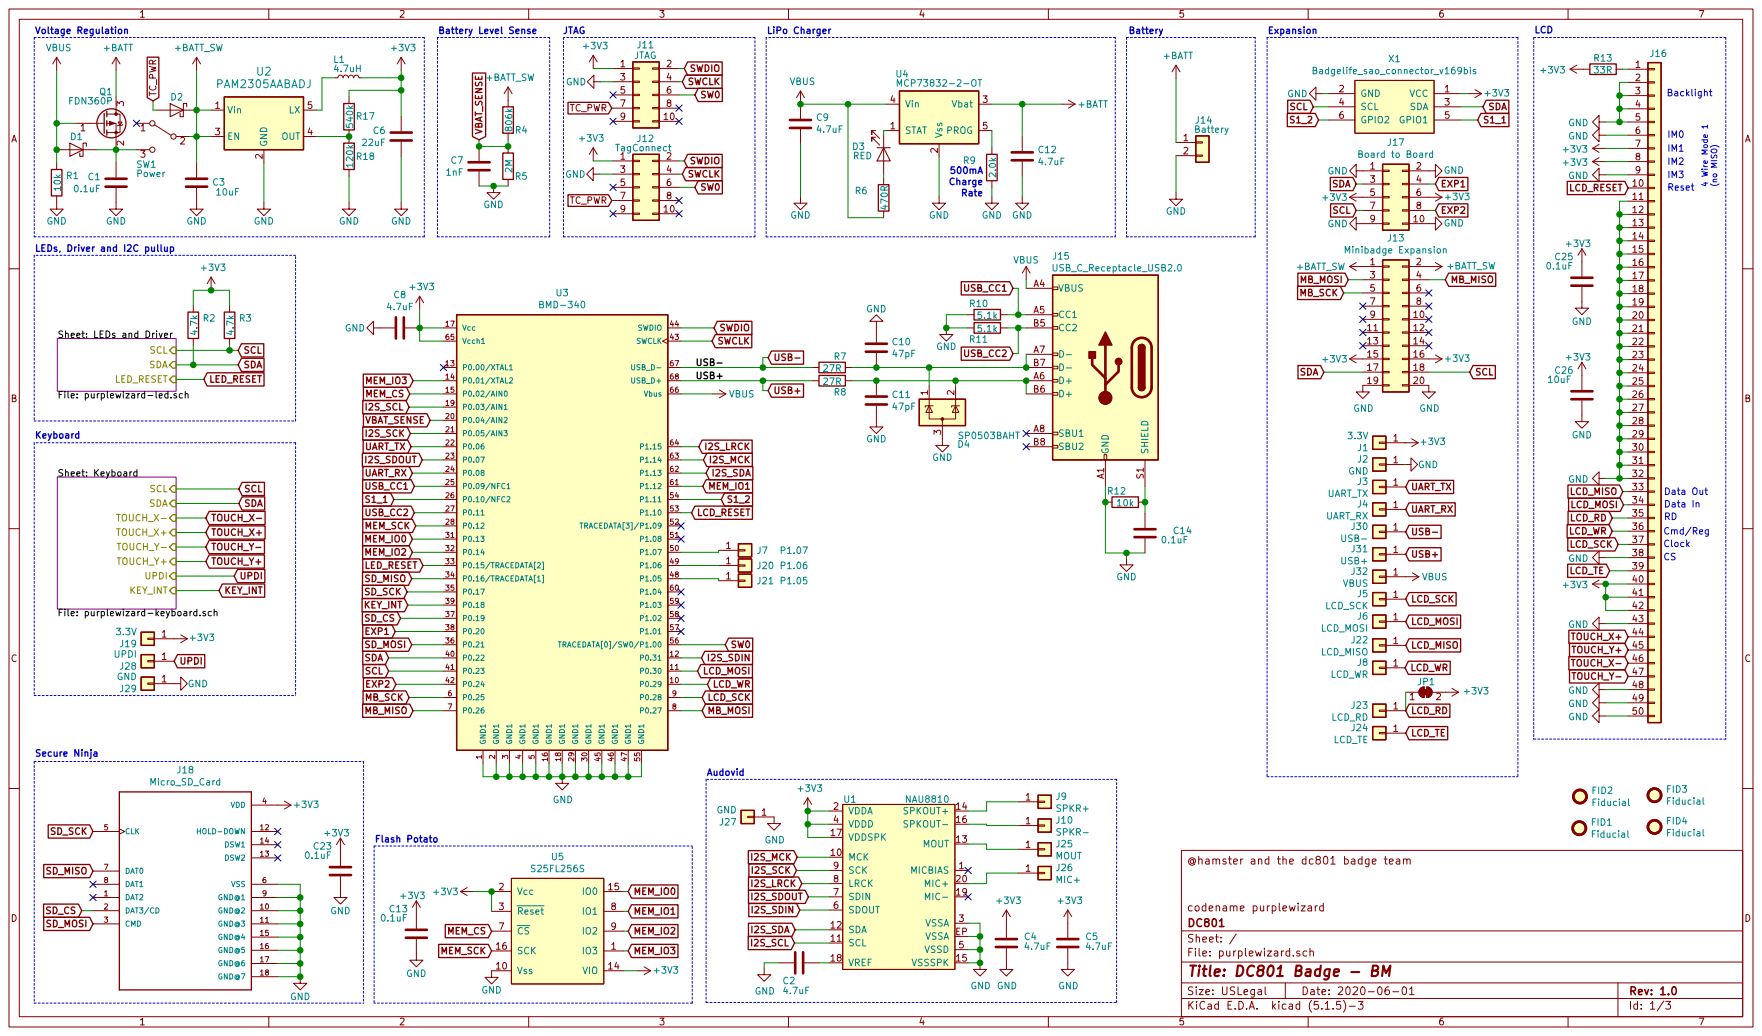
[picture p106: page 1]

2 3 Q1 FDN360P GND GND GND GND

IM3 LEDs, Driver and I2C pullup
SW0 EXP1 SD_MISO
SCL UPDI TOUCH_X- TOUCH_X+ TOUCH_Y- TOUCH_Y+ KEY_INT Sheet: LEDs and Driver File: purplewizard-led.sch SDA

5 P1.11 54 GND1 55 TRACEDATA[0]/SW0/P1.00 56 P1.14 63 P1.15 64 P0.28 9 P0.29 10 P0.30 11 P0.31 12 Vcc 17 P0.19 37 P0.20 38 P0.18 39 P0.22 40 P0.23 41 P0.24 42 SWCLK 43 P1.05 48 P1.06 49 P1.07 50 P1.08 51 TRACEDATA[3]/P1.09 52 P1.10 53 P1.01 57 P1.02 58 P1.03 59 P0.25 6 P1.04 60 P1.12 61 P1.13 62 Vcch1 65 Vbus 66 USB_D- 67 USB_D+ 68 P0.26 7 P0.27 8 U3 BMD-340
LED_RESET MEM_CS
I2S_SCL

File: purplewizard-keyboard.sch SDA

@hamster and the dc801 badge team

codename purplewizard
D Date: 2020-06-01 KiCad E.D.A. kicad (5.1.5)-3
File: purplewizard.sch Sheet: / DC801

Id: 1/3 Title: DC801 Badge - BM

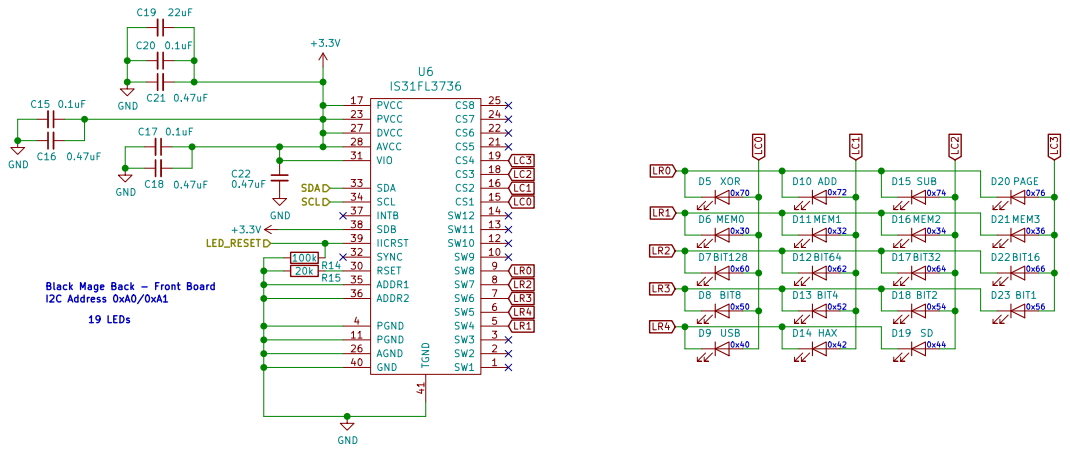
[picture p107: page 2]

0x36 Black Mage Back - Front Board

@hamster and the dc801 badge team

codename purplewizard
File: purplewizard-led.sch Sheet: /LEDs and Driver/ DC801

D Date: 2020-06-01 KiCad E.D.A. kicad (5.1.5)-3

Id: 2/3 Title: DC801 Badge - BM - Defcon CANCELED

Size: USLegal | Rev: 1.0

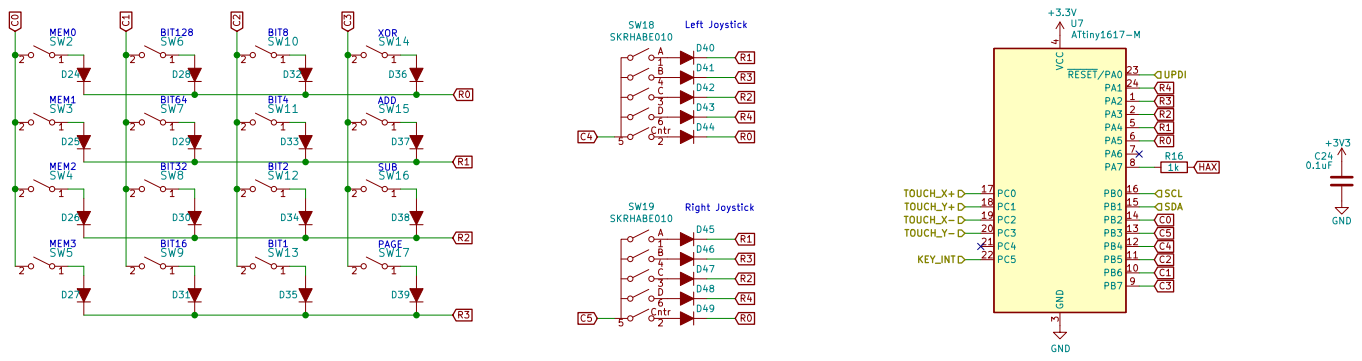
[picture p108: page 3]

@hamster and the dc801 badge team

D Date: 2020-06-01 KiCad E.D.A. kicad (5.1.5)-3

File: purplewizard-keyboard.sch
Id: 3/3 Title: DC801 Badge - BM - Defcon CANCELED

Size: USLegal | Rev: 1.0

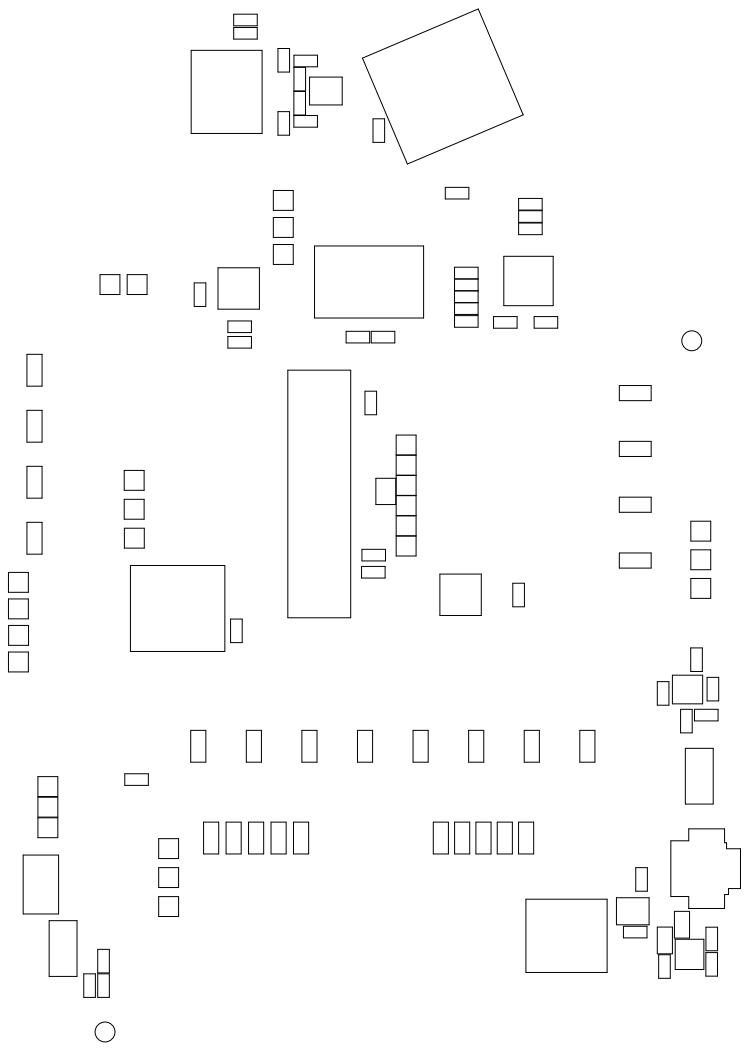
[picture p109: page 4]

@hamster and the dc801 badge team

Id: 1/1 Title: DC801 Badge - BM

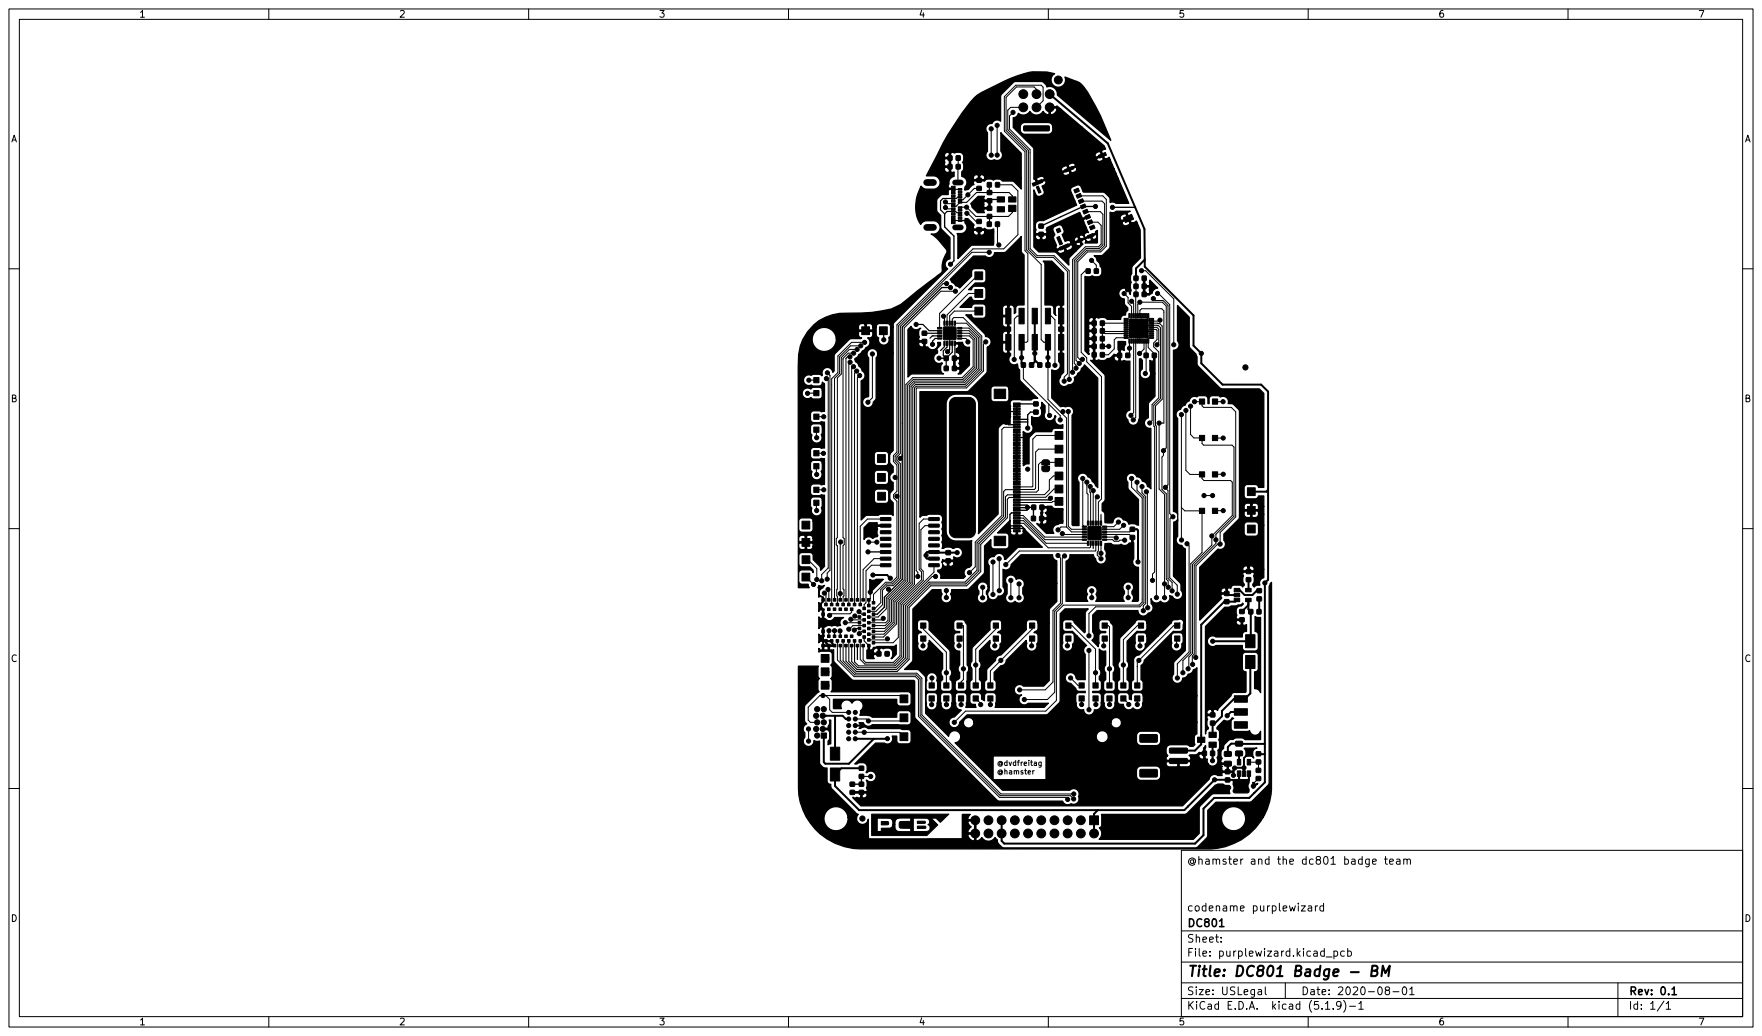
[picture p110: page 5]

@hamster and the dc801 badge team

Id: 1/1 Title: DC801 Badge - BM

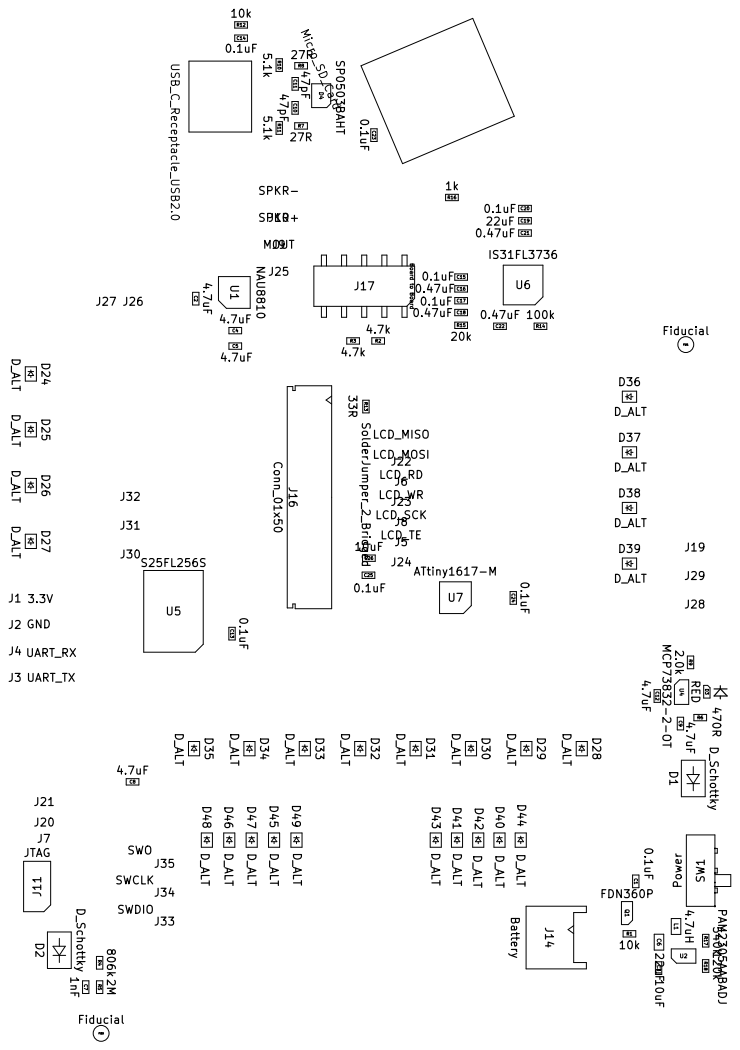
[picture p111: page 6]

@hamster and the dc801 badge team Micro_SD_Card

Id: 1/1 Title: DC801 Badge - BM

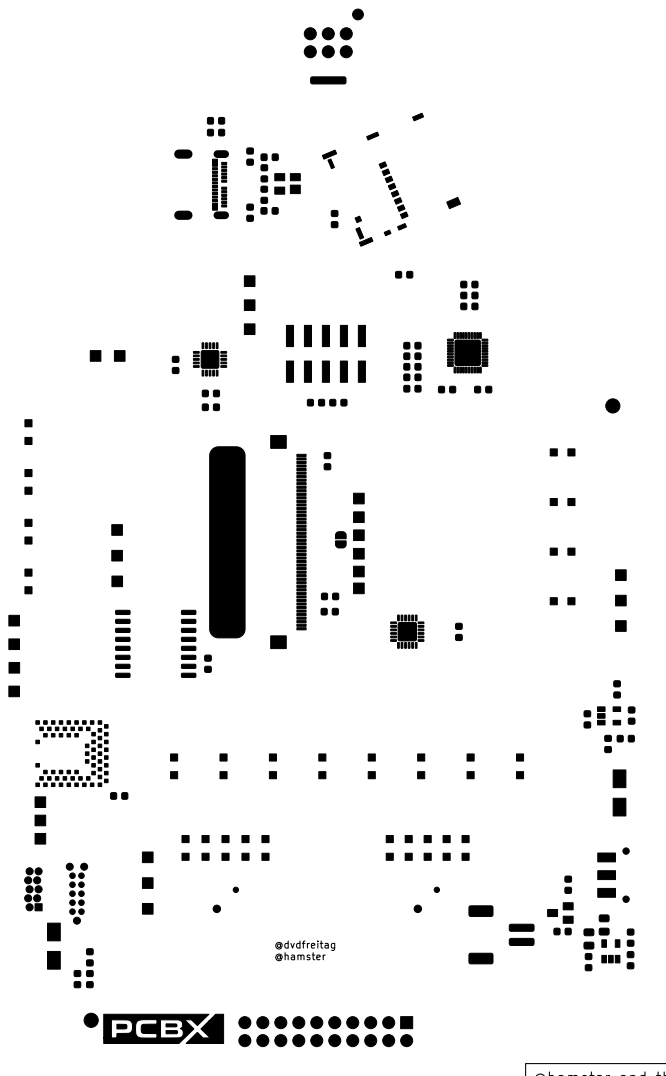
[picture p112: page 7]

@hamster and the dc801 badge team

Id: 1/1 Title: DC801 Badge - BM

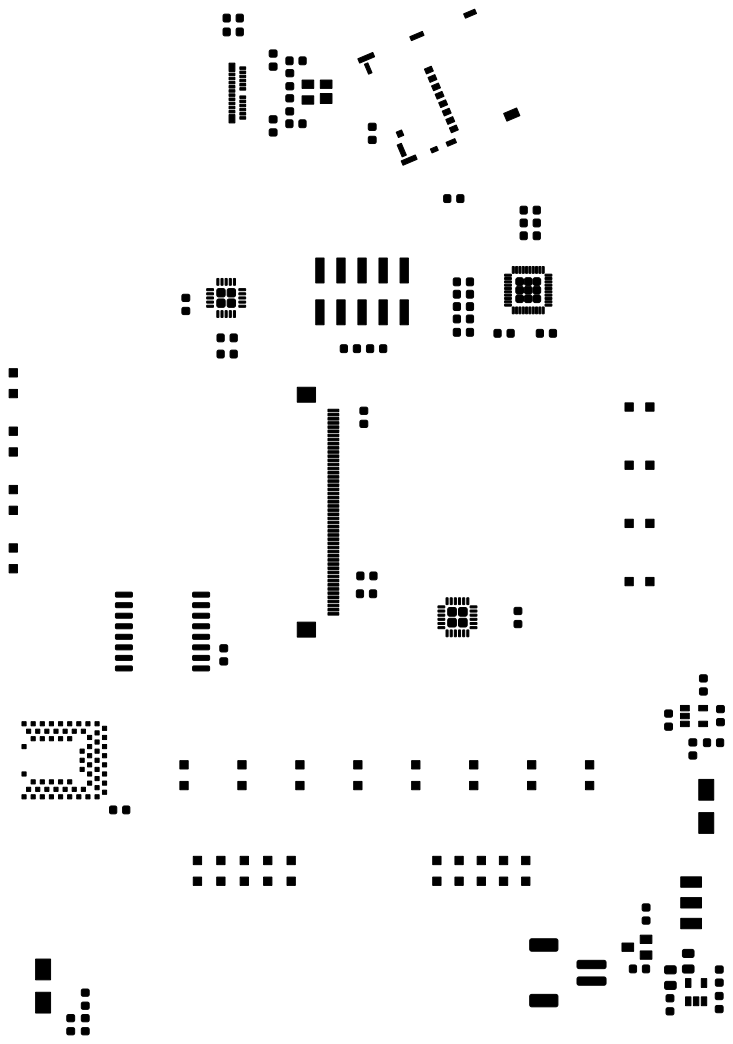
[picture p113: page 8]

@hamster and the dc801 badge team

Id: 1/1 Title: DC801 Badge - BM

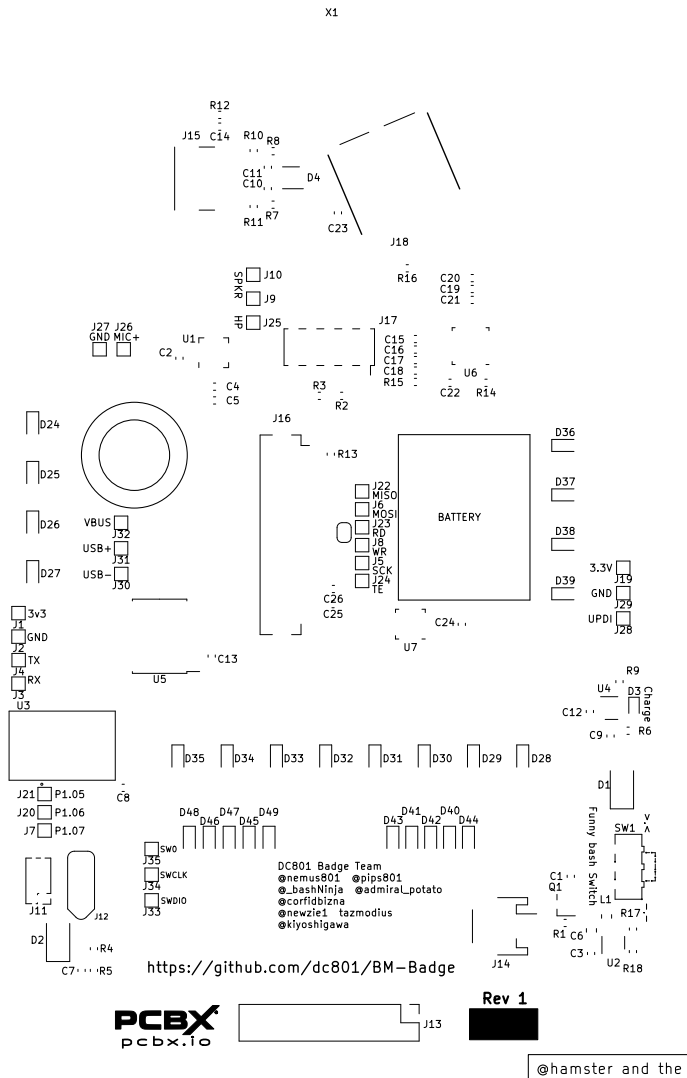
[picture p114: page 9]

@hamster and the dc801 badge team

Id: 1/1 Title: DC801 Badge - BM

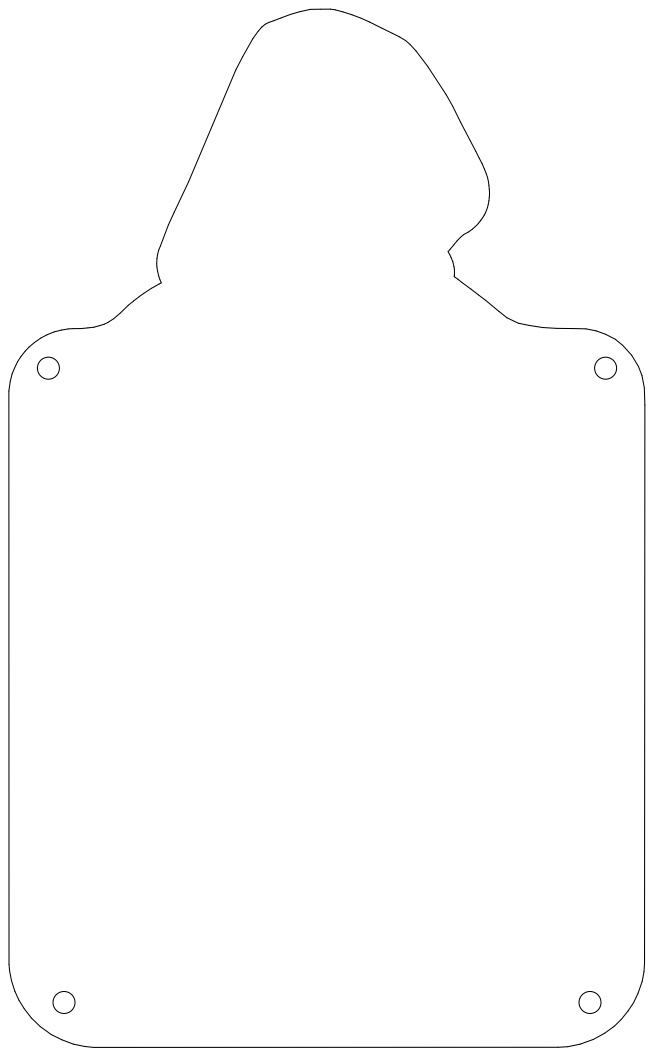
[picture p115: page 10]

@hamster and the dc801 badge team

Id: 1/1 Title: DC801 Badge - BM

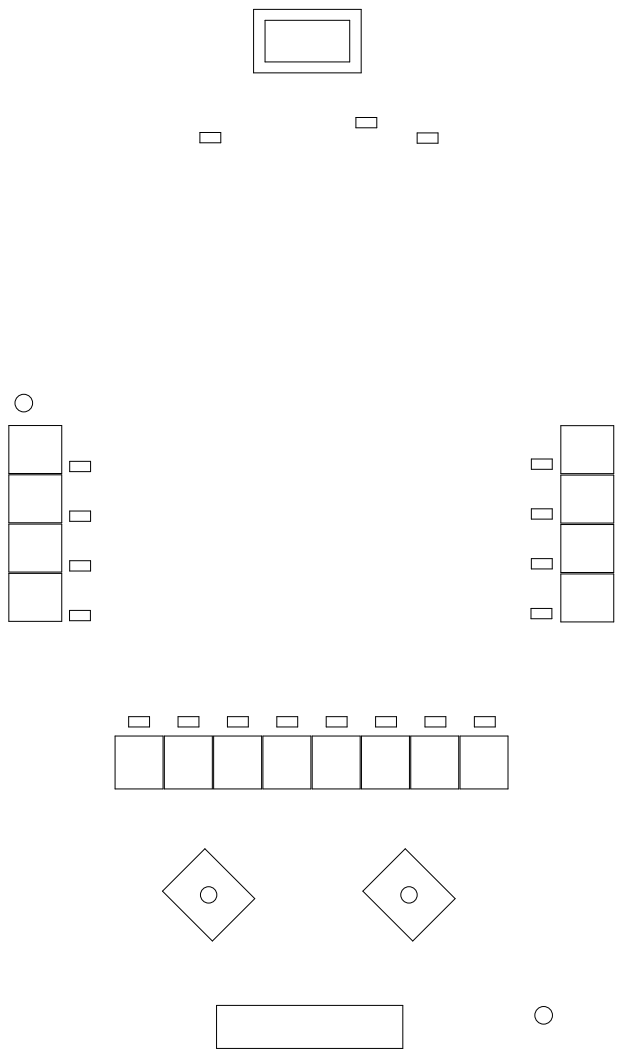
[picture p116: page 11]

@hamster and the dc801 badge team

Id: 1/1 Title: DC801 Badge - BM

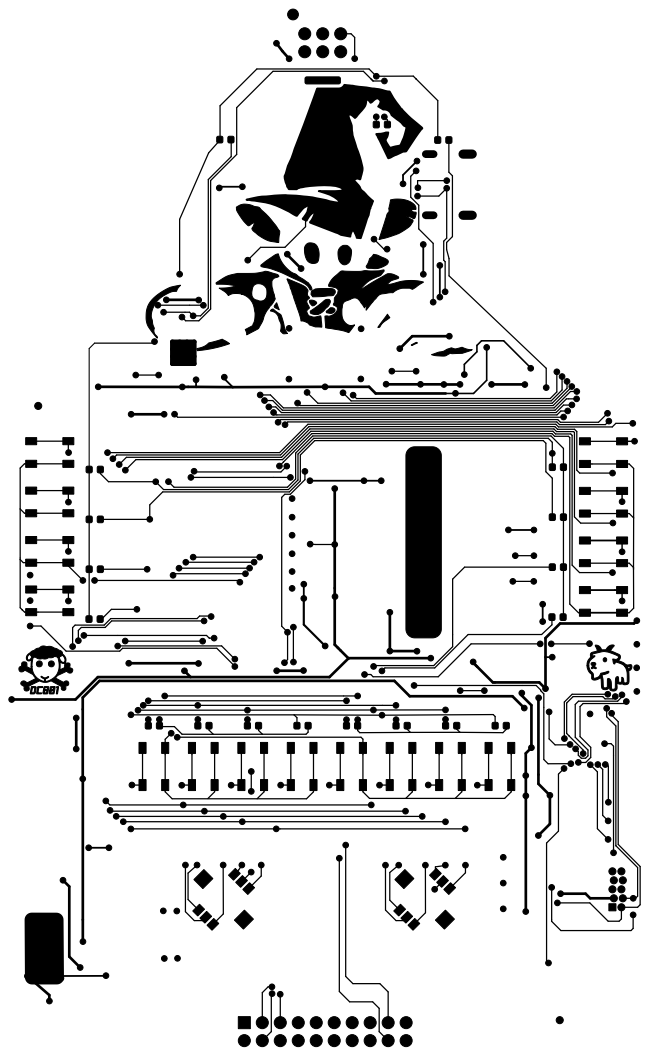
[picture p117: page 12]

@hamster and the dc801 badge team

Id: 1/1 Title: DC801 Badge - BM

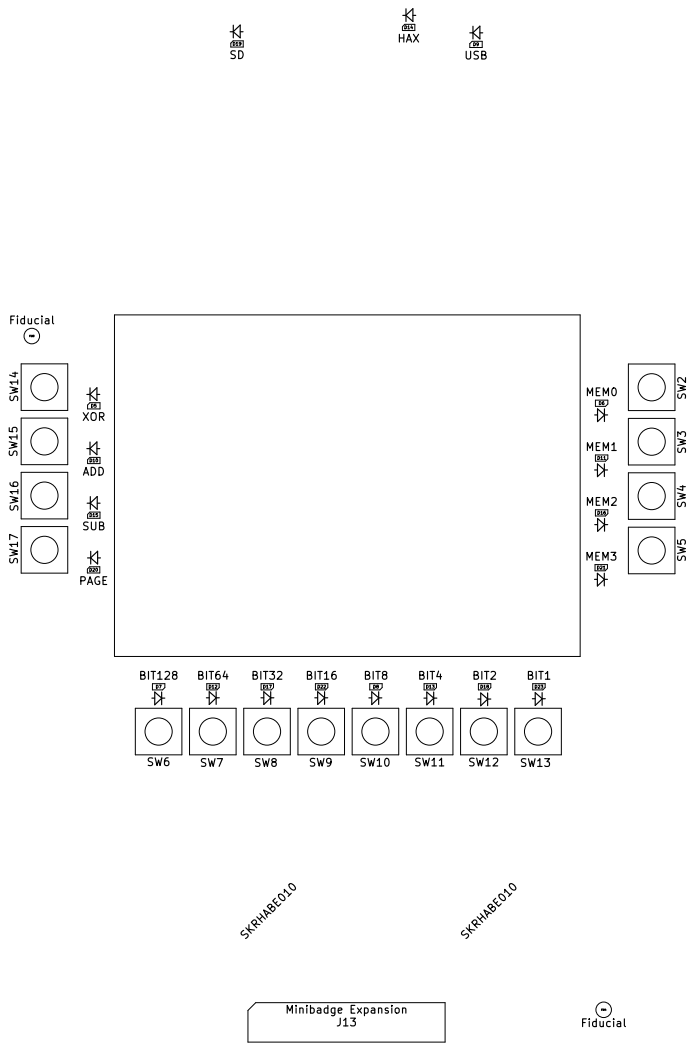
[picture p118: page 13]

@hamster and the dc801 badge team

Id: 1/1 Title: DC801 Badge - BM

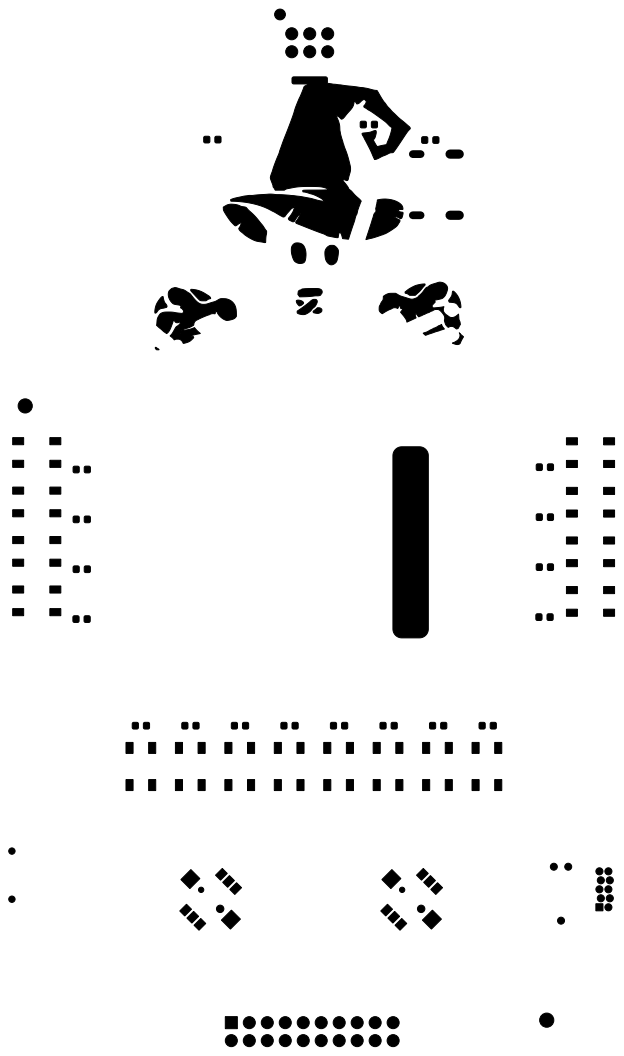
[picture p119: page 14]

@hamster and the dc801 badge team

Id: 1/1 Title: DC801 Badge - BM

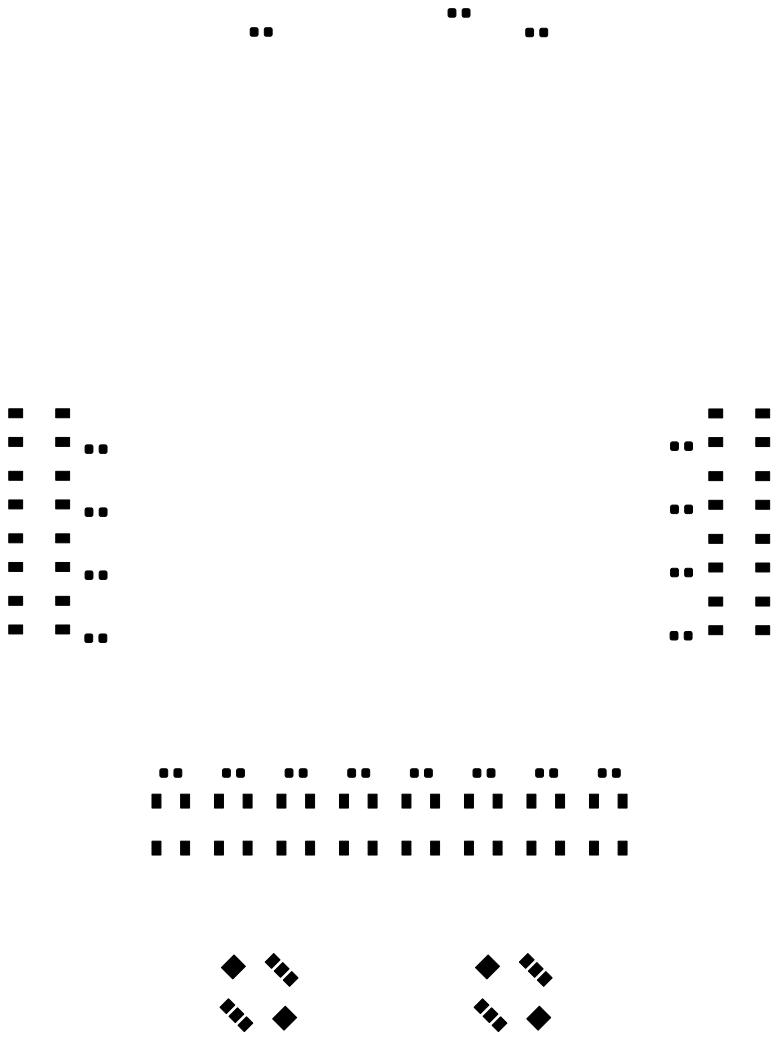
[picture p120: page 15]

@hamster and the dc801 badge team

Id: 1/1 Title: DC801 Badge - BM

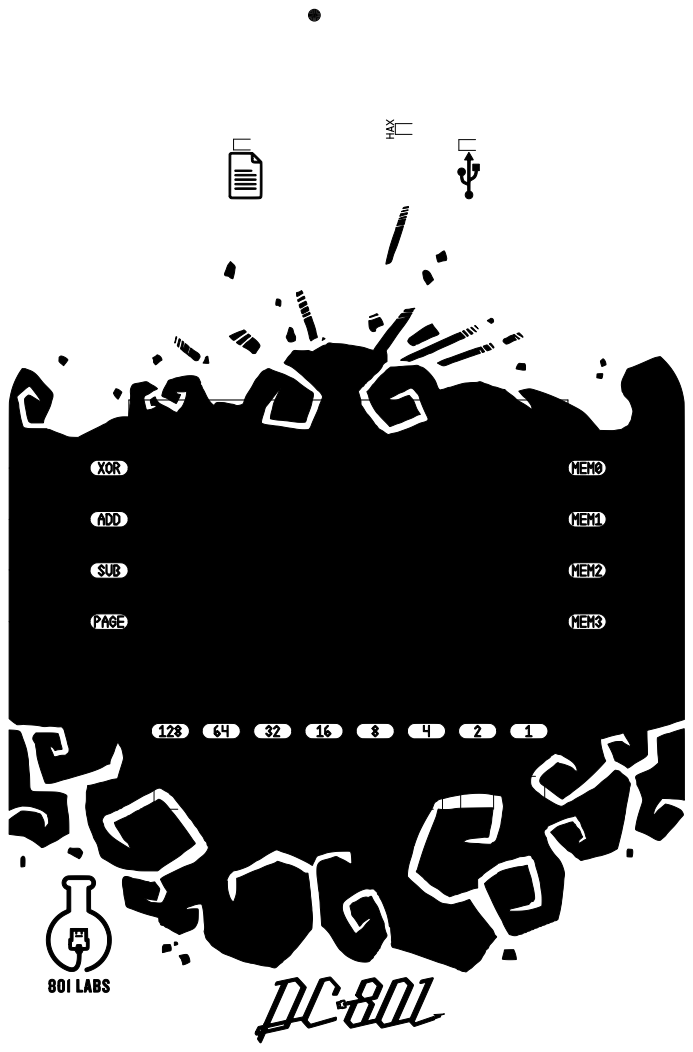
[picture p121: page 16]

@hamster and the dc801 badge team HAX

Id: 1/1 Title: DC801 Badge - BM

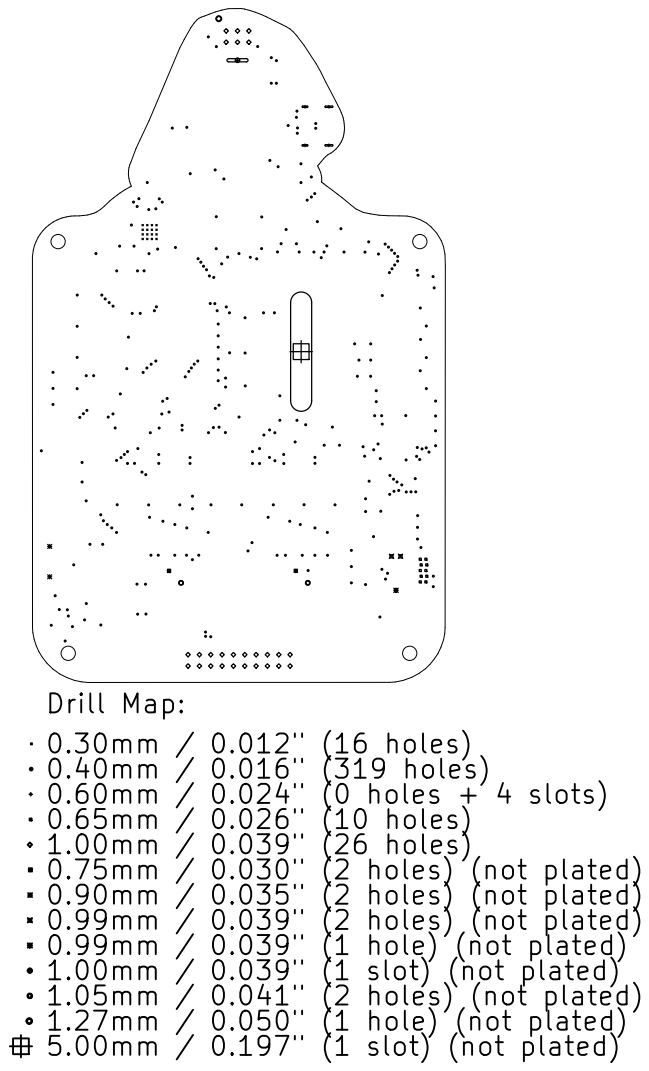
[picture p122: page 17]
