DC801/BM-Badge/Hardware/ART/2020/output/purplewizard-ART-2020-complete.pdf

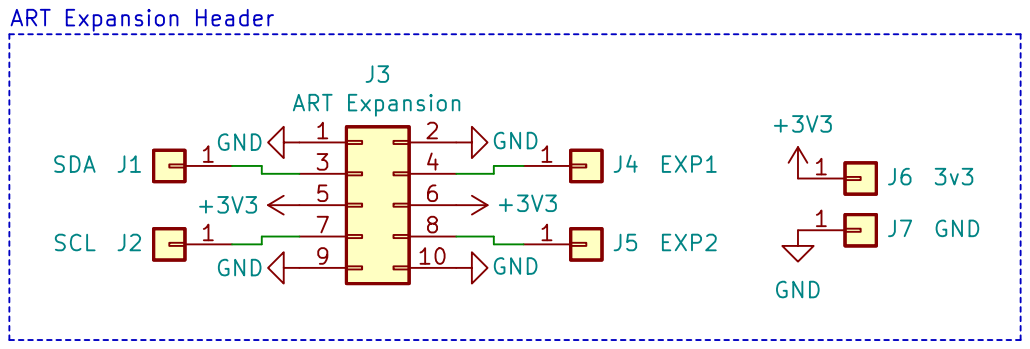
[picture p123: page 1]

@hamster and the dc801 badge team

codename purplewizard
File: purplewizard-ART.sch Sheet: / DC801

Id: 1/1 Title: DC801 Badge - ART 2020


@hamster and the dc801 badge team

codename purplewizard
D Date: 2020-06-15 KiCad E.D.A. kicad (5.1.9)-1
File: purplewizard-ART.kicad_pcb Sheet: DC801

Id: 1/1 Title: DC801 Badge - ART 2020

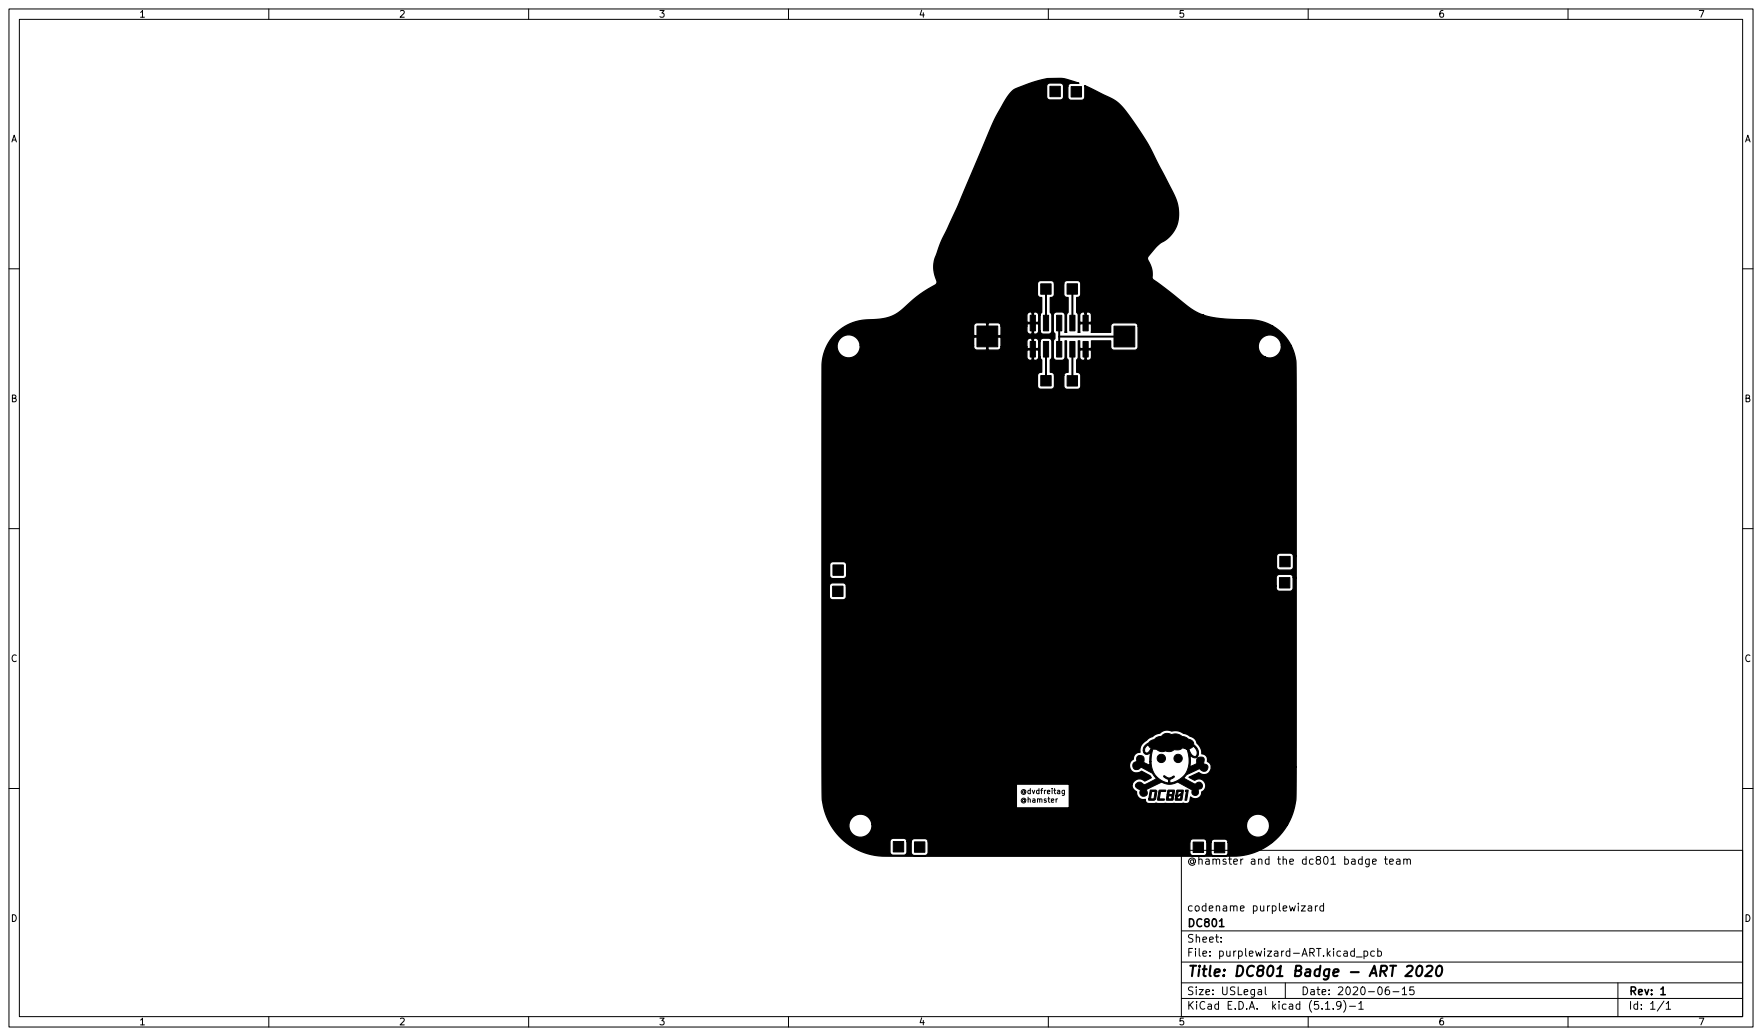
[picture p124: page 3]

@hamster and the dc801 badge team

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

Id: 1/1 Title: DC801 Badge - ART 2020


codename purplewizard
File: purplewizard-ART.kicad_pcb Sheet: DC801

Id: 1/1 Title: DC801 Badge - ART 2020

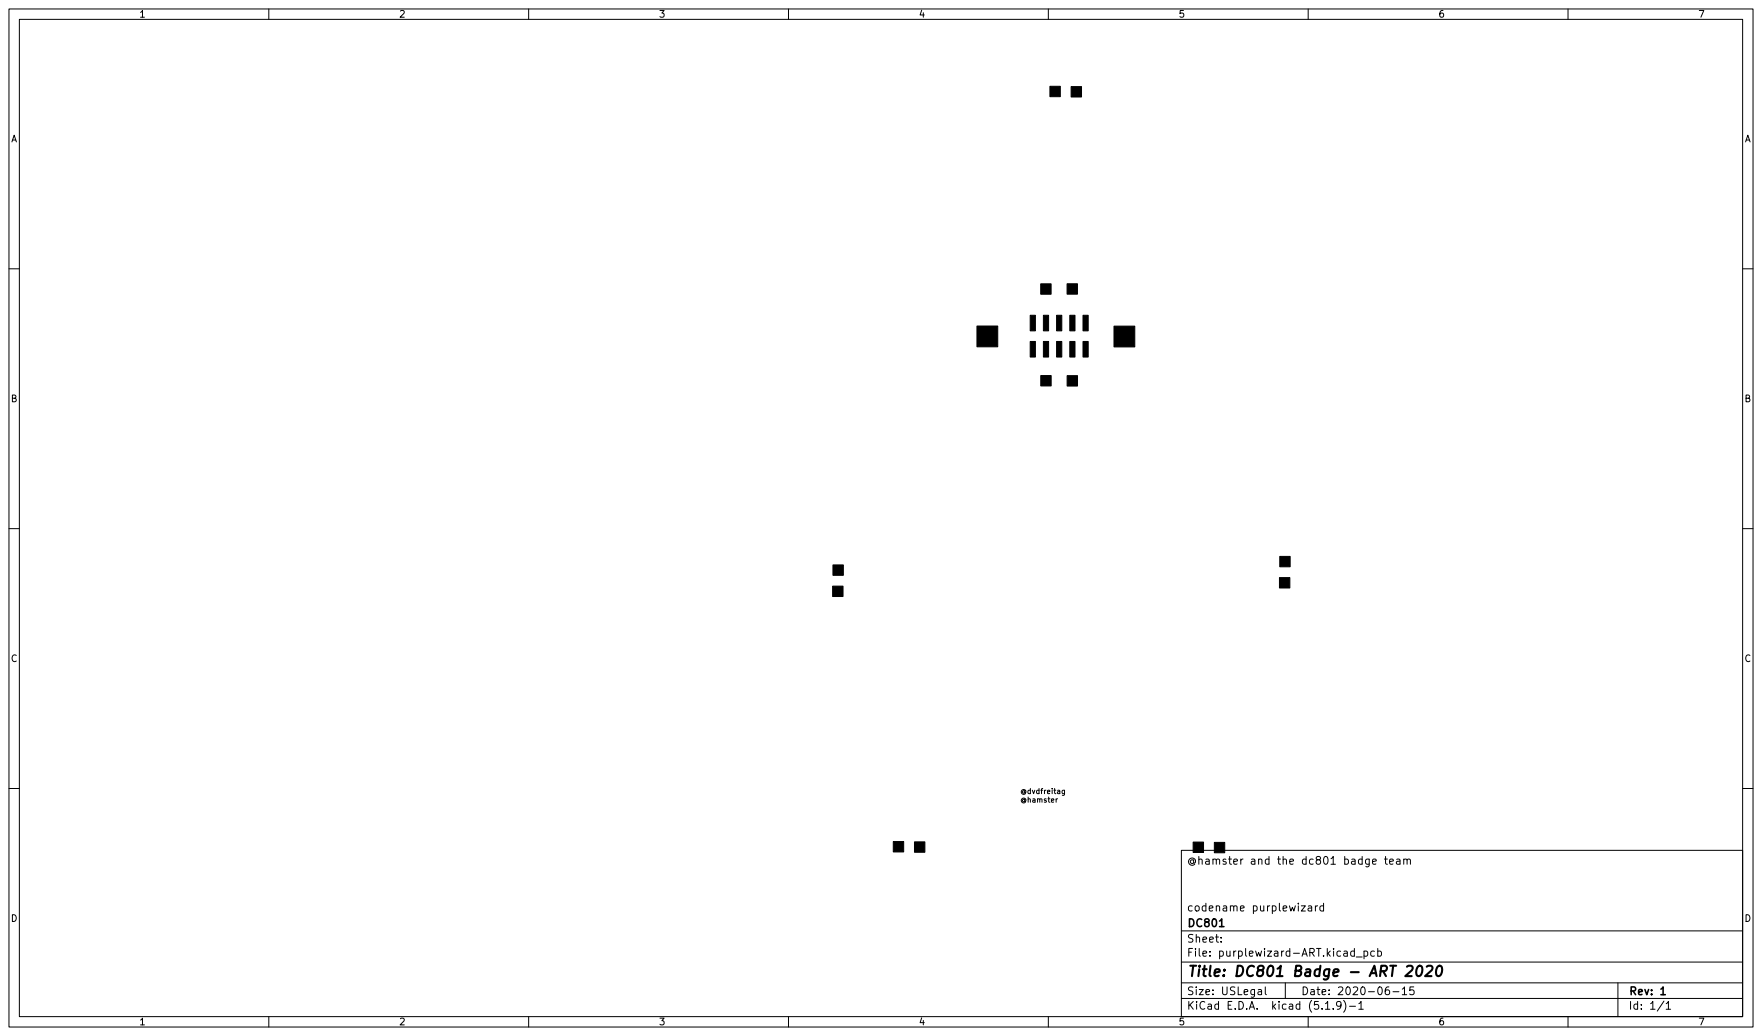
[picture p125: page 5]

@hamster and the dc801 badge team

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

Id: 1/1 Title: DC801 Badge - ART 2020

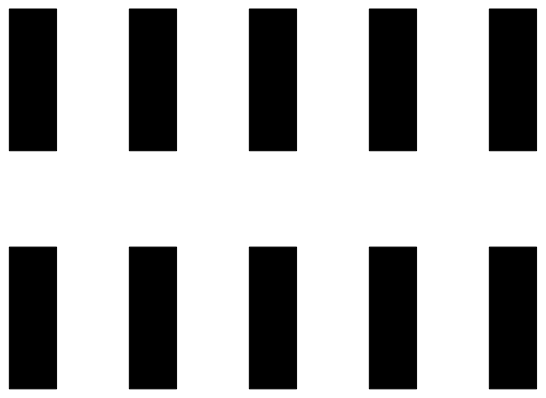
[picture p126: page 6]

@hamster and the dc801 badge team

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

Id: 1/1 Title: DC801 Badge - ART 2020


https://github.com/dc801/BM-Badge/HW/ART/2020/ DC801 Badge Team @nemus801 @_bashNinja @admiral_potato @corfidbizna @pips801 @newzie1

@hamster and the dc801 badge team

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

Id: 1/1 Title: DC801 Badge - ART 2020

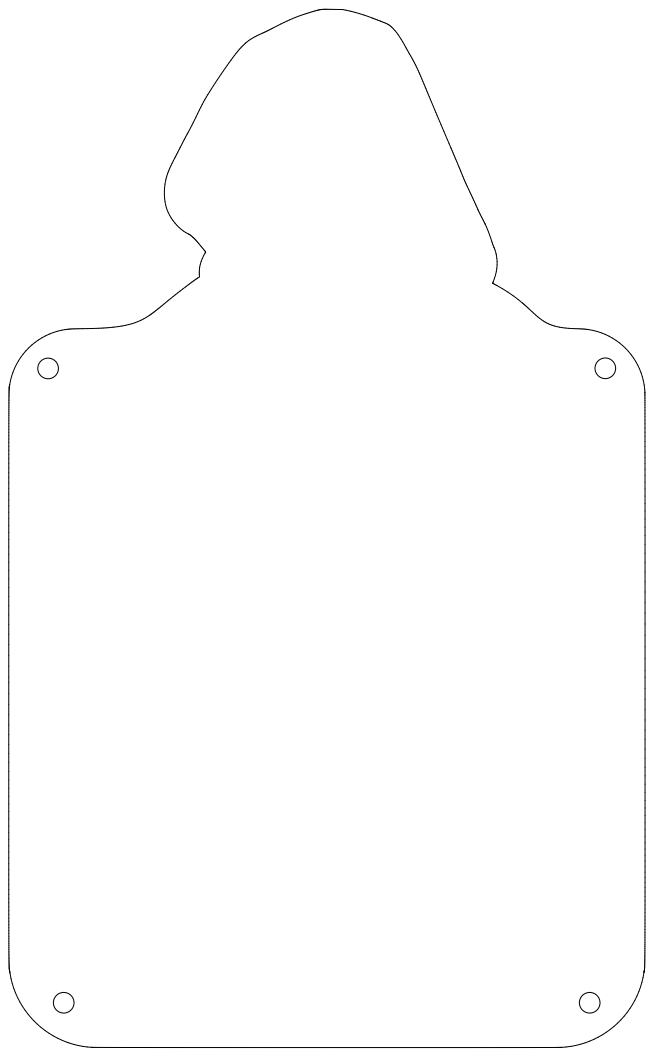
[picture p127: page 8]

@hamster and the dc801 badge team

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

Id: 1/1 Title: DC801 Badge - ART 2020

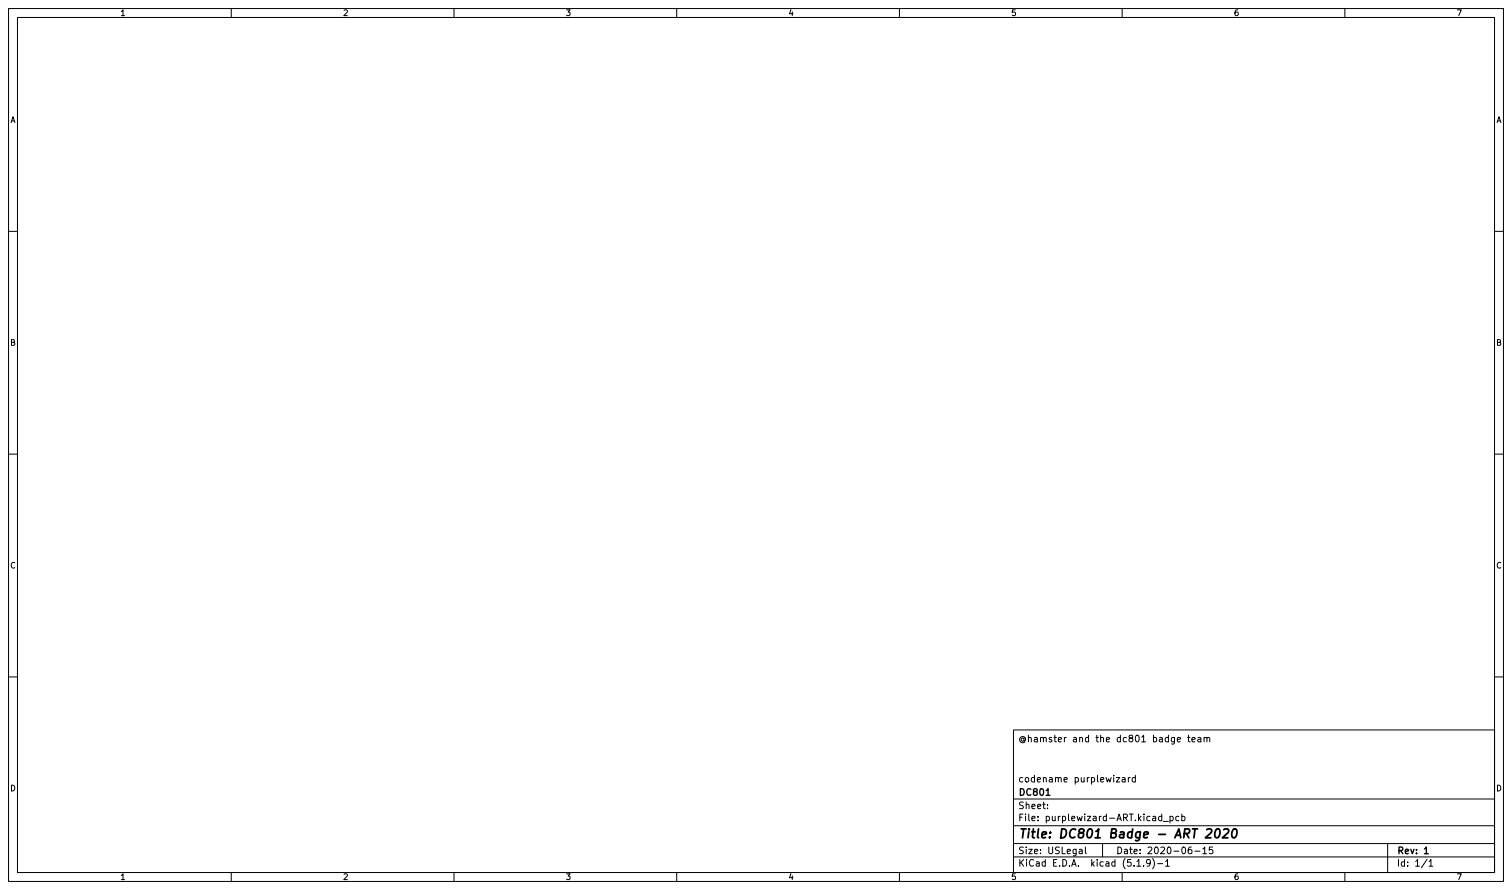
[picture p128: page 9]

@hamster and the dc801 badge team

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

Id: 1/1 Title: DC801 Badge - ART 2020

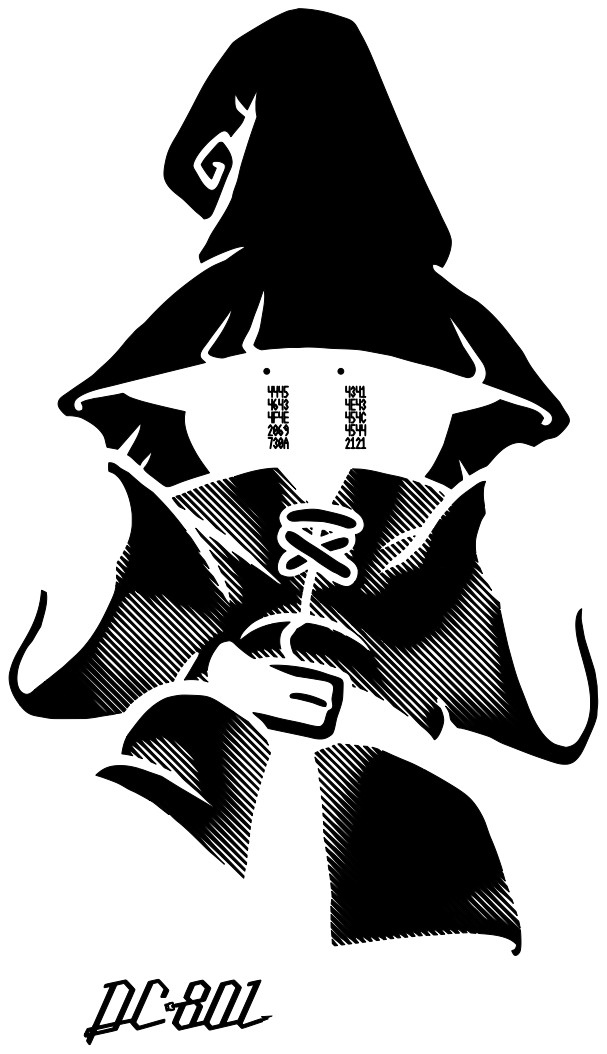
[picture p129: page 10]

@hamster and the dc801 badge team

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

Id: 1/1 Title: DC801 Badge - ART 2020

@hamster and the dc801 badge team

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

Id: 1/1 Title: DC801 Badge - ART 2020

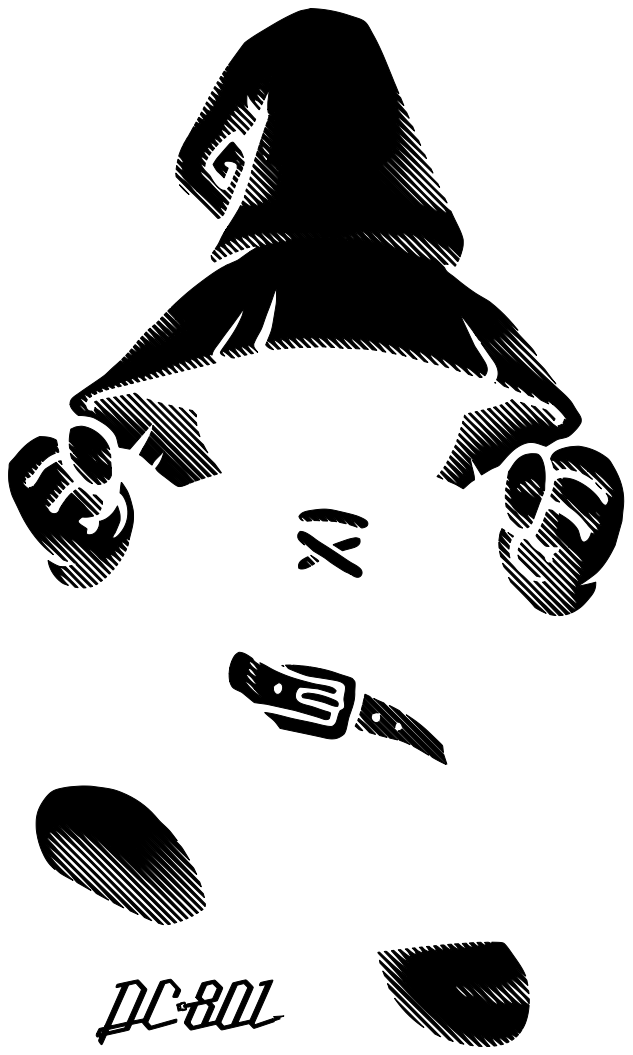
[picture p130: page 12]

@hamster and the dc801 badge team

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

Id: 1/1 Title: DC801 Badge - ART 2020

@hamster and the dc801 badge team

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

Id: 1/1 Title: DC801 Badge - ART 2020

@hamster and the dc801 badge team

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

Id: 1/1 Title: DC801 Badge - ART 2020

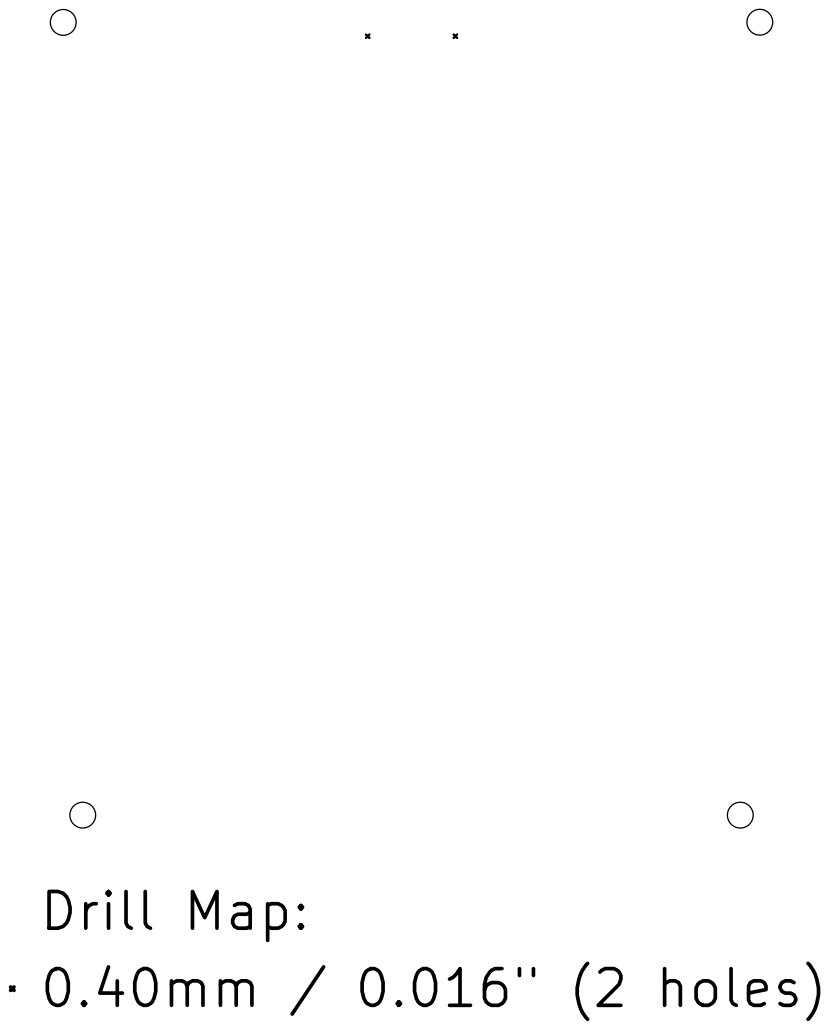
[picture p131: page 15]
