DC801/BM-Badge/Hardware/BackBoard/outputs/Proto1/purplewizard-proto-complete.pdf

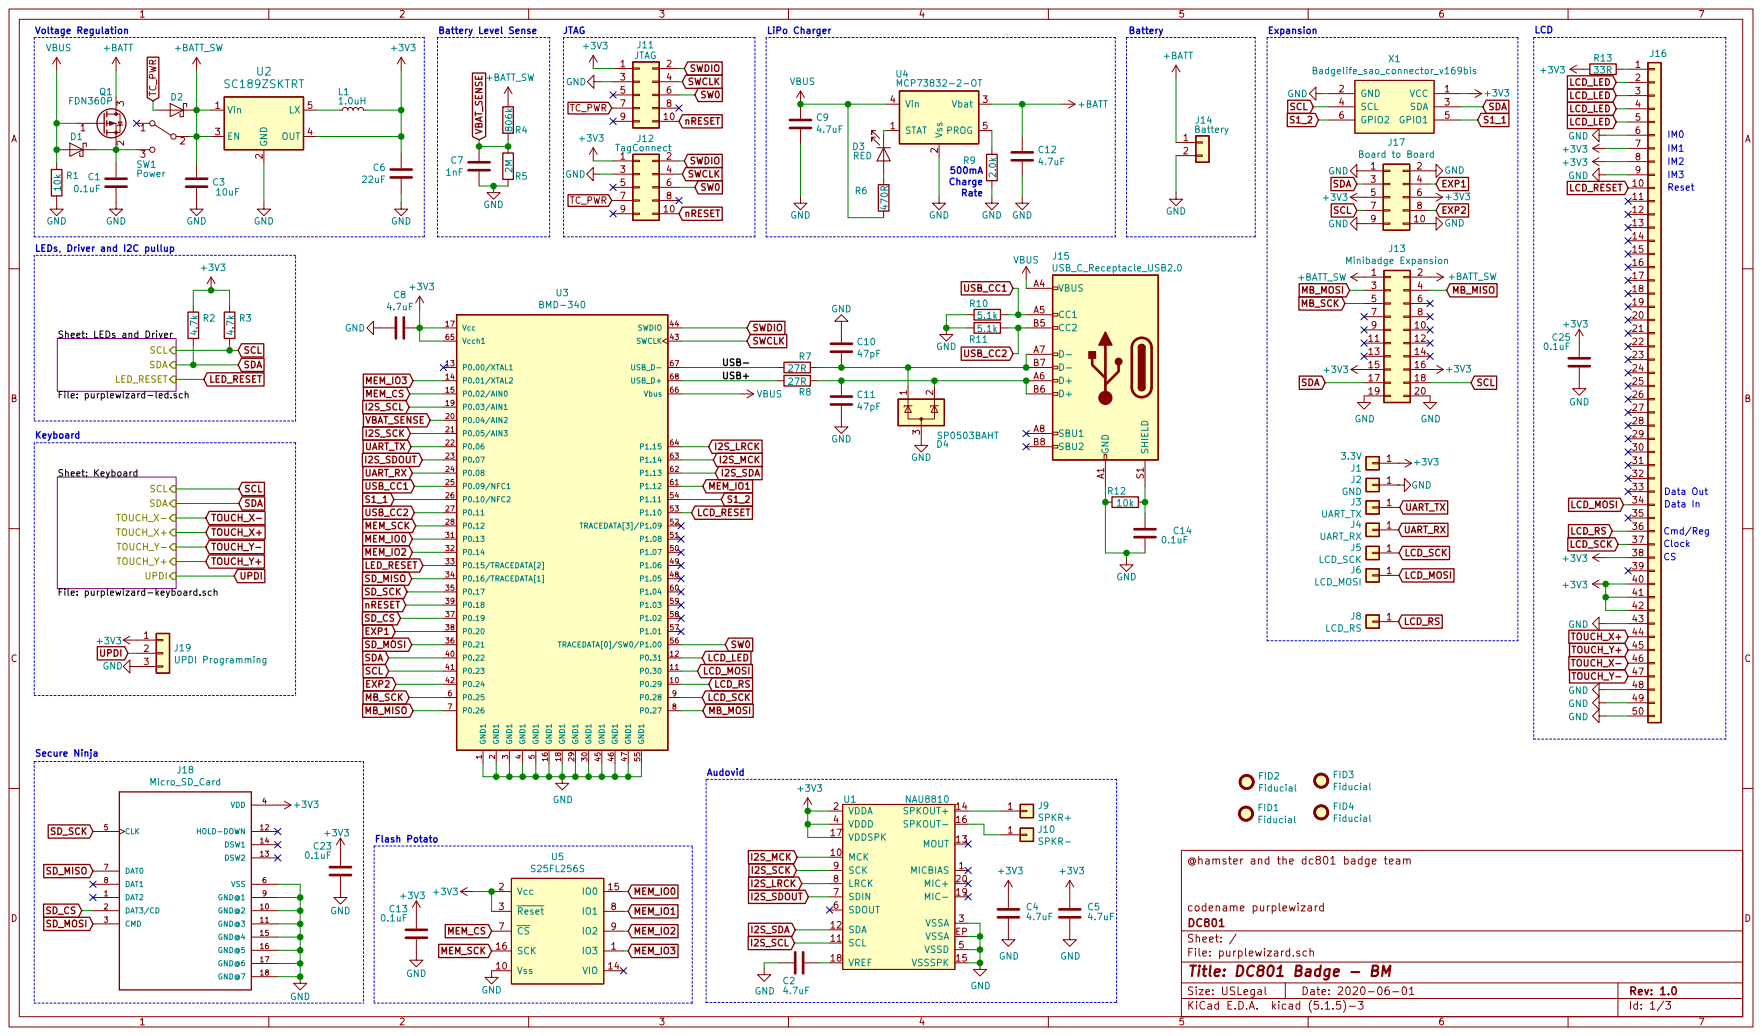
[picture p132: page 1]

SCL UPDI TOUCH_X- TOUCH_X+ TOUCH_Y- TOUCH_Y+ Sheet: LEDs and Driver File: purplewizard-led.sch SDA

LEDs, Driver and I2C pullup

5 P1.11 54 GND1 55 TRACEDATA[0]/SW0/P1.00 56 P1.14 63 P1.15 64 P0.28 9 P0.29 10 P0.30 11 P0.31 12 Vcc 17 P0.19 37 P0.20 38 P0.18 39 P0.22 40 P0.23 41 P0.24 42 SWCLK 43 P1.05 48 P1.06 49 P1.07 50 P1.08 51 TRACEDATA[3]/P1.09 52 P1.10 53 P1.01 57 P1.02 58 P1.03 59 P0.25 6 P1.04 60 P1.12 61 P1.13 62 Vcch1 65 Vbus 66 USB_D- 67 USB_D+ 68 P0.26 7 P0.27 8 U3 BMD-340
I2S_SCK

File: purplewizard-keyboard.sch SDA

FID4 Fiducial FID3 Fiducial FID1 Fiducial FID2 Fiducial

@hamster and the dc801 badge team

codename purplewizard
D Date: 2020-06-01 KiCad E.D.A. kicad (5.1.5)-3
File: purplewizard.sch Sheet: / DC801

Id: 1/3 Title: DC801 Badge - BM

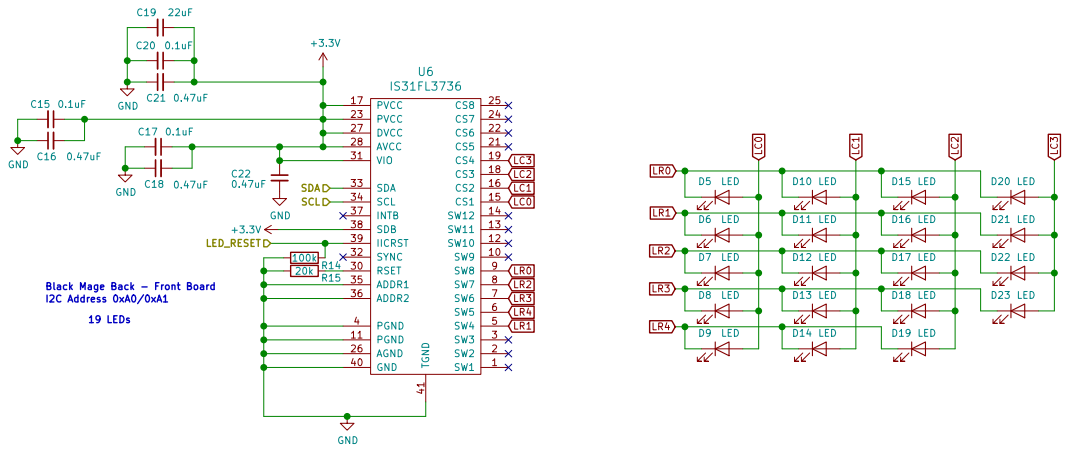
[picture p133: page 2]

19 LEDs Black Mage Back - Front Board
I2C Address 0xA0/0xA1

@hamster and the dc801 badge team

codename purplewizard
File: purplewizard-led.sch Sheet: /LEDs and Driver/ DC801

D Date: 2020-06-01 KiCad E.D.A. kicad (5.1.5)-3

Id: 2/3 Title: DC801 Badge - BM - Defcon CANCELED

Size: USLegal | Rev: 1.0

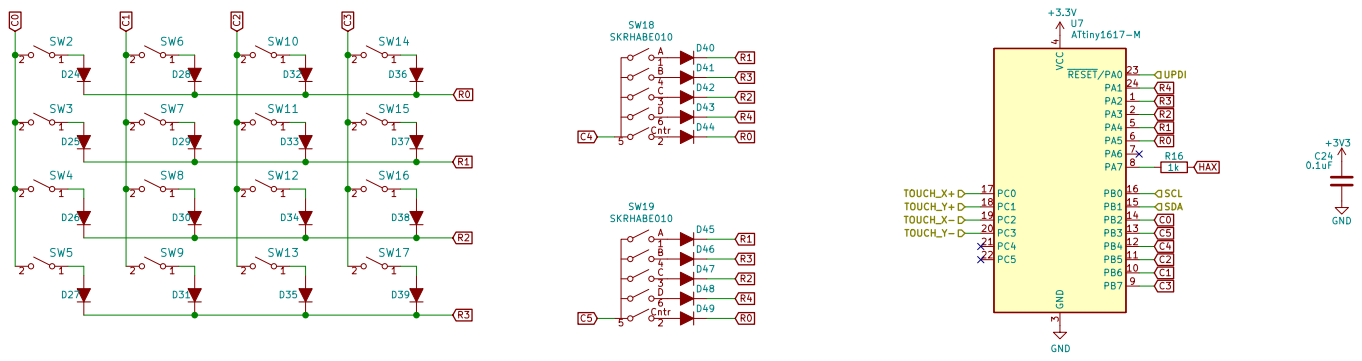
[picture p134: page 3]

@hamster and the dc801 badge team

D Date: 2020-06-01 KiCad E.D.A. kicad (5.1.5)-3

File: purplewizard-keyboard.sch
Id: 3/3 Title: DC801 Badge - BM - Defcon CANCELED

Size: USLegal | Rev: 1.0

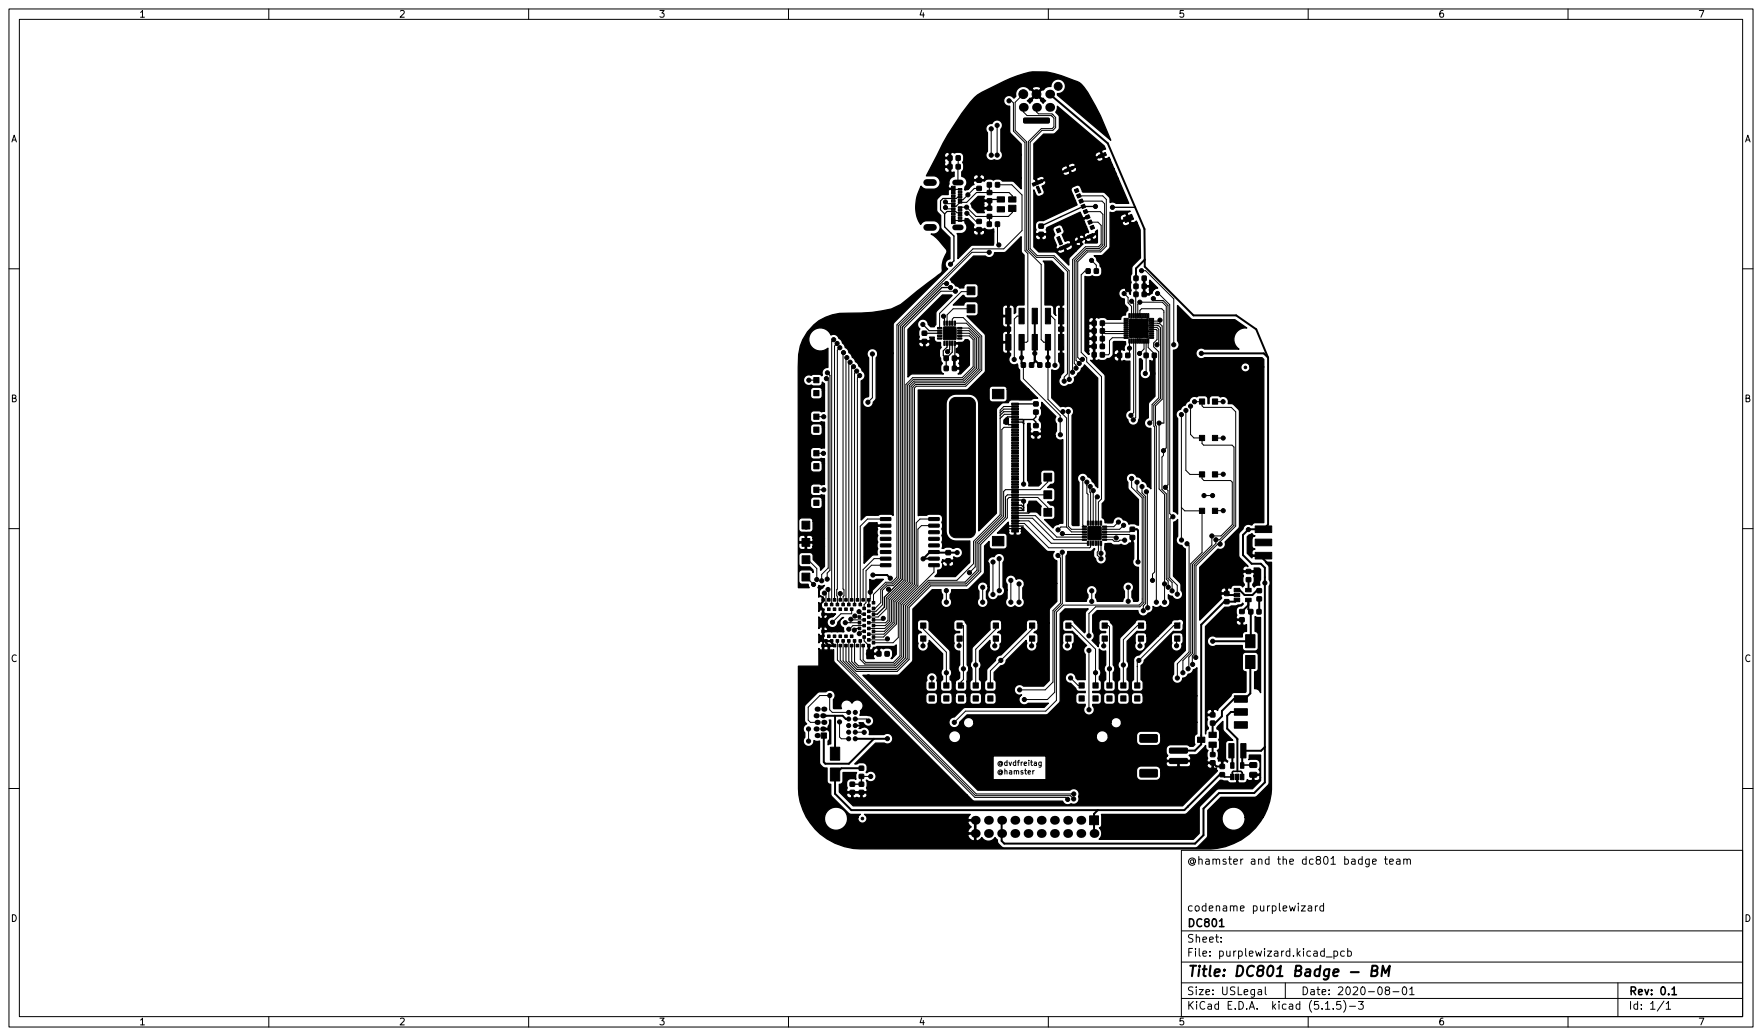
[picture p135: page 4]

@hamster and the dc801 badge team

Id: 1/1 Title: DC801 Badge - BM

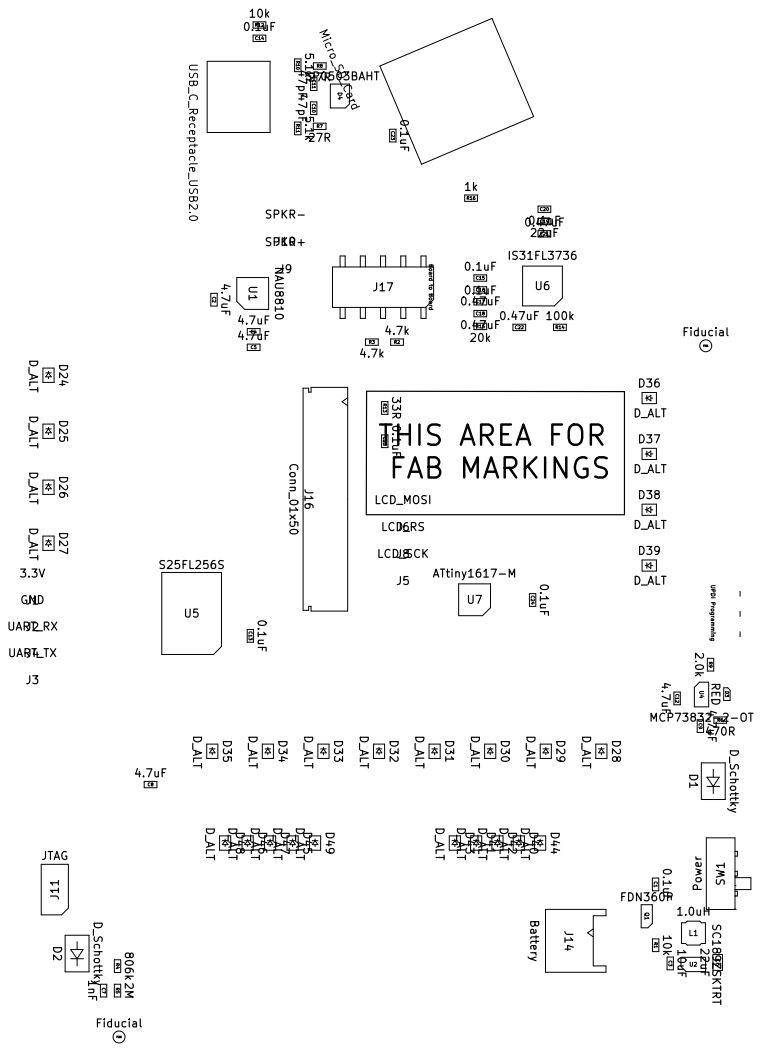
[picture p136: page 5]

@hamster and the dc801 badge team

Id: 1/1 Title: DC801 Badge - BM

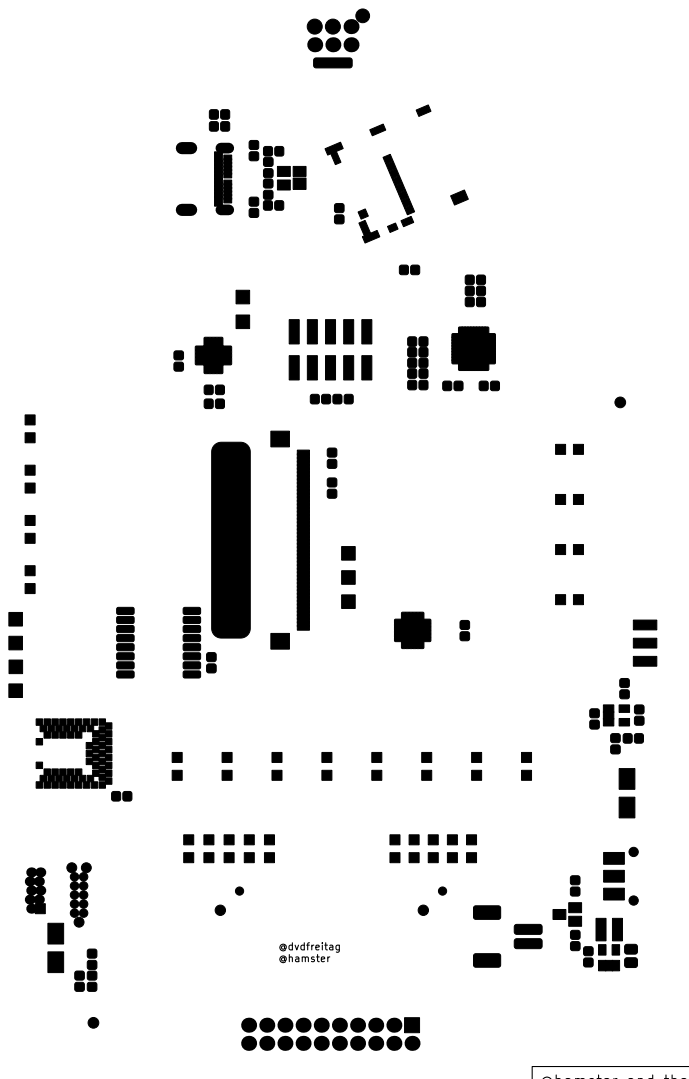
[picture p137: page 6]

@hamster and the dc801 badge team

Id: 1/1 Title: DC801 Badge - BM

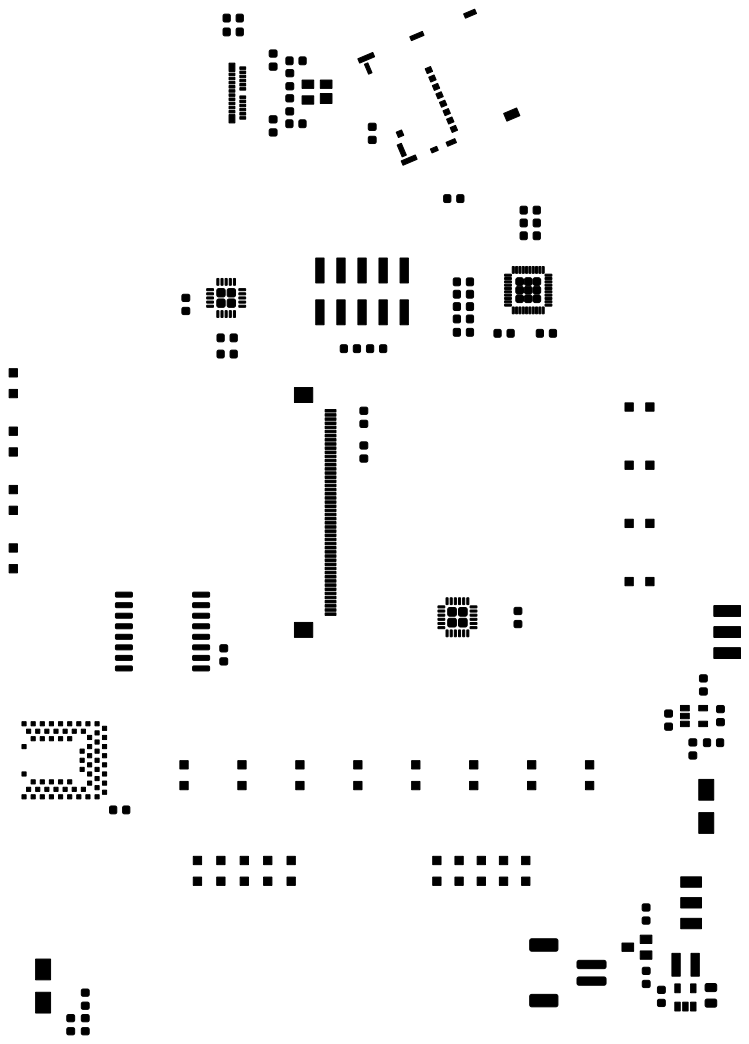
[picture p138: page 7]

@hamster and the dc801 badge team

Id: 1/1 Title: DC801 Badge - BM

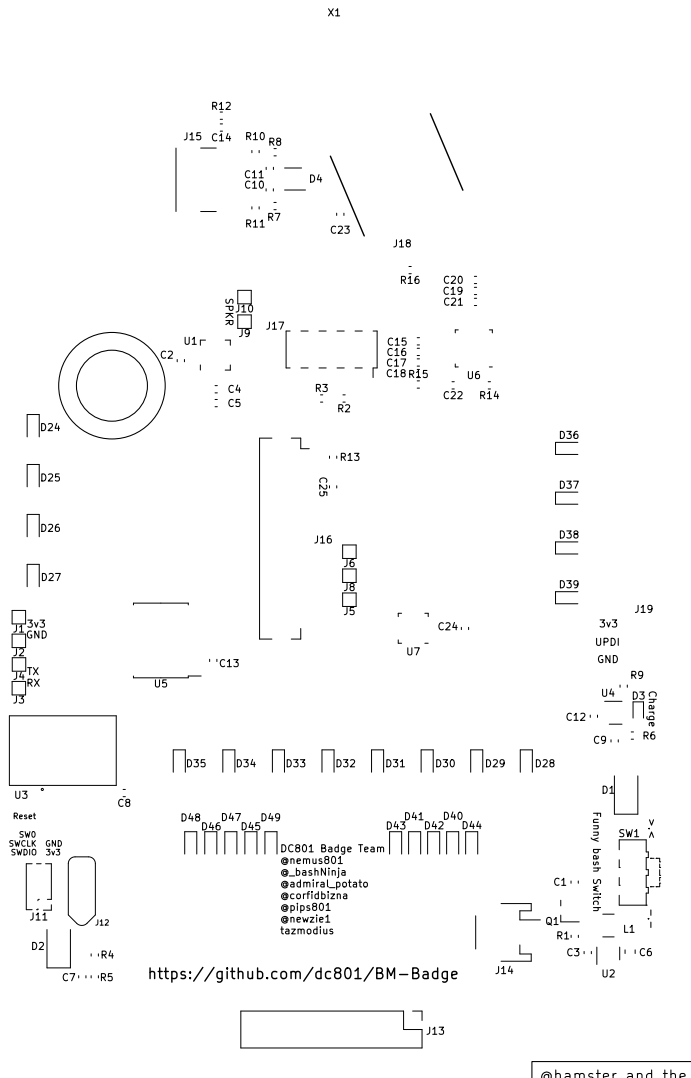
[picture p139: page 8]

UPDI https://github.com/dc801/BM-Badge

@hamster and the dc801 badge team

Id: 1/1 Title: DC801 Badge - BM

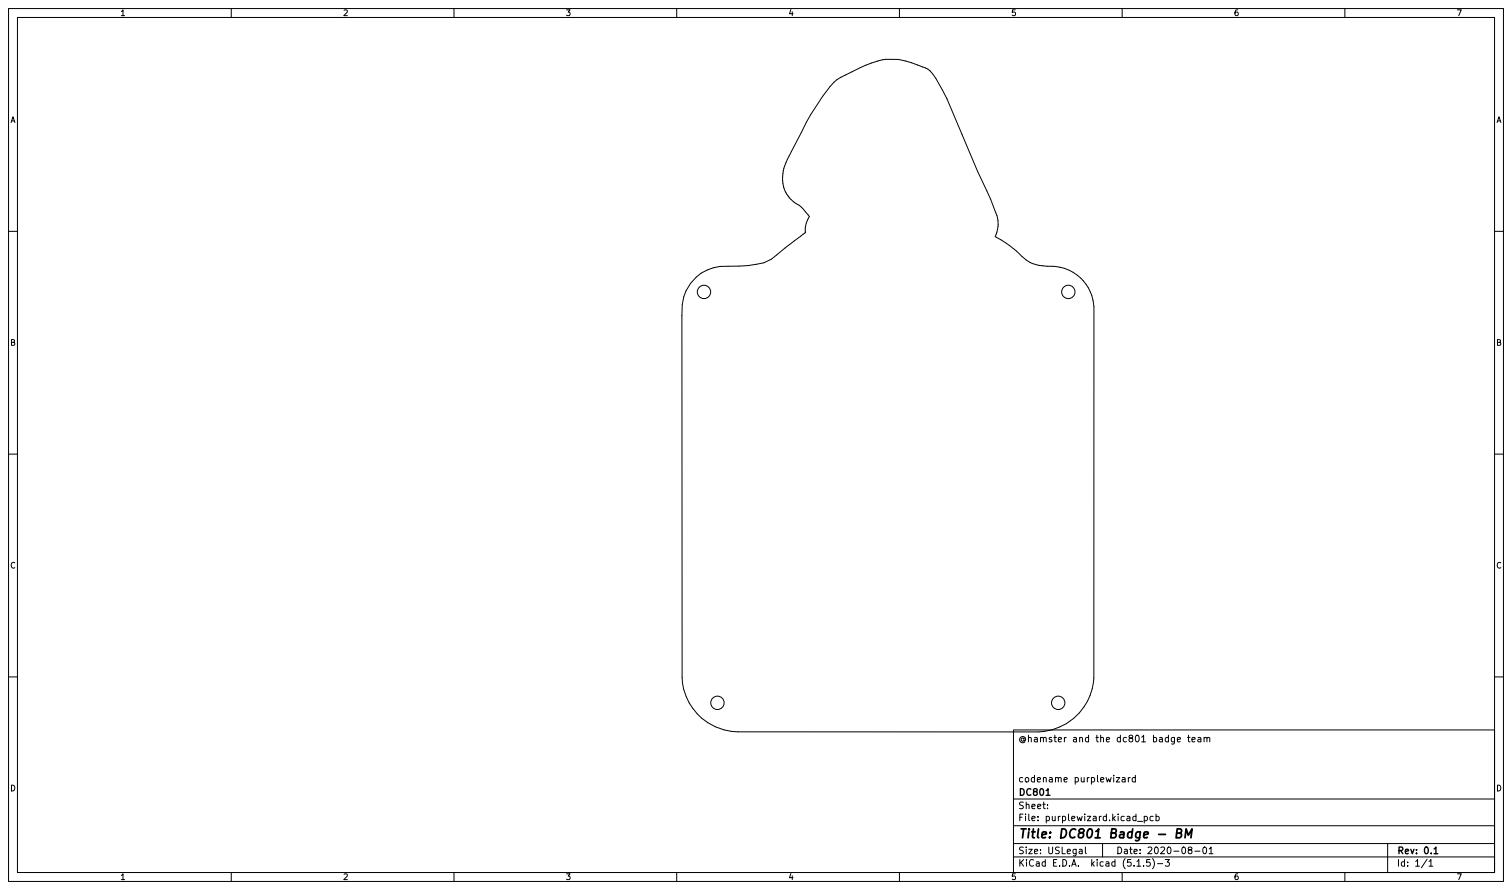
[picture p140: page 9]

@hamster and the dc801 badge team

Id: 1/1 Title: DC801 Badge - BM

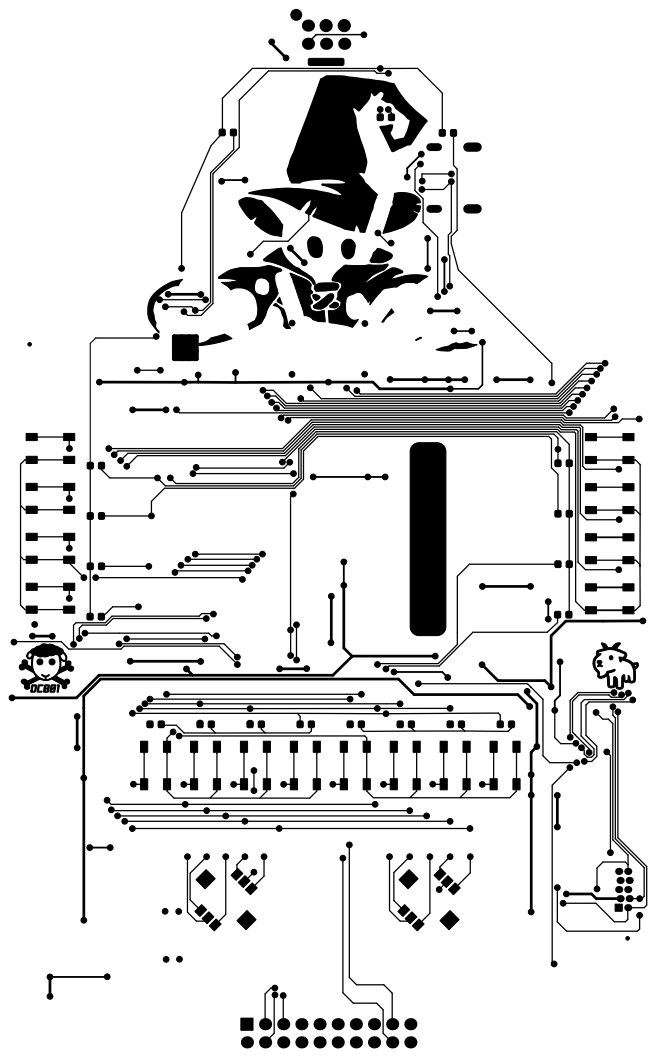
[picture p141: page 10]

@hamster and the dc801 badge team

Id: 1/1 Title: DC801 Badge - BM

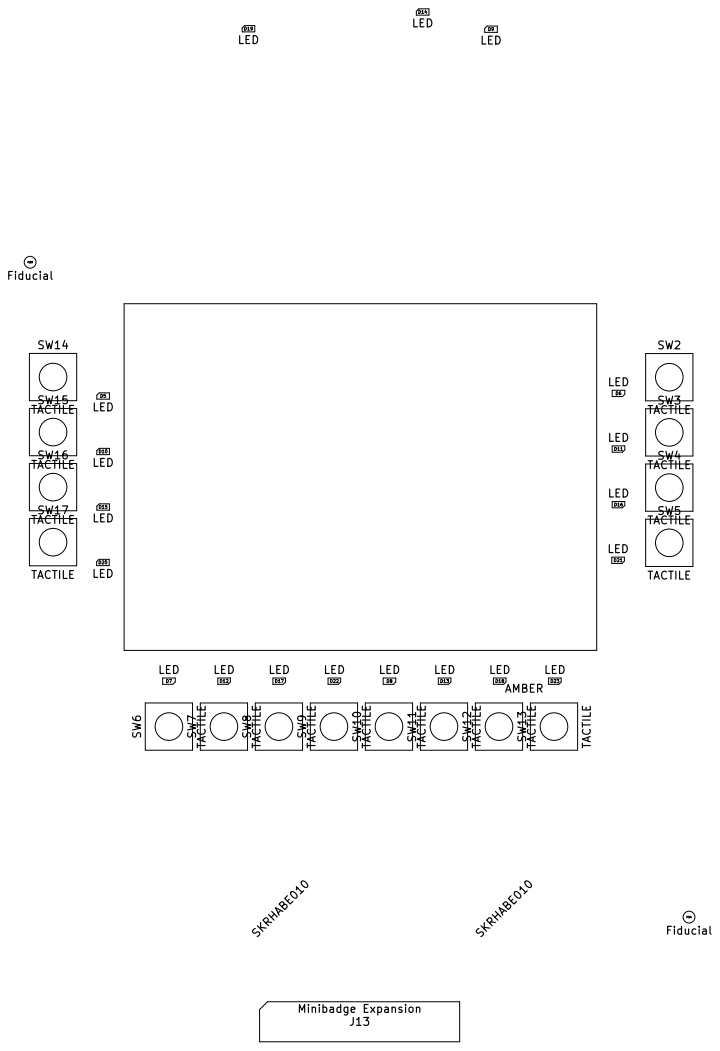
[picture p142: page 11]

@hamster and the dc801 badge team

Id: 1/1 Title: DC801 Badge - BM

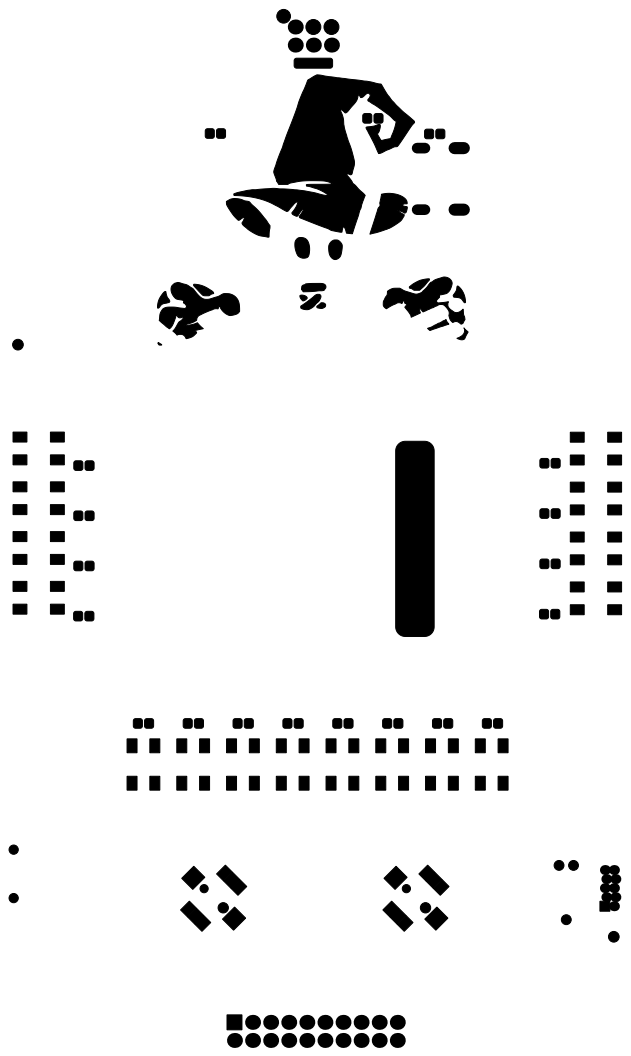
[picture p143: page 12]

@hamster and the dc801 badge team

Id: 1/1 Title: DC801 Badge - BM


@hamster and the dc801 badge team

Id: 1/1 Title: DC801 Badge - BM

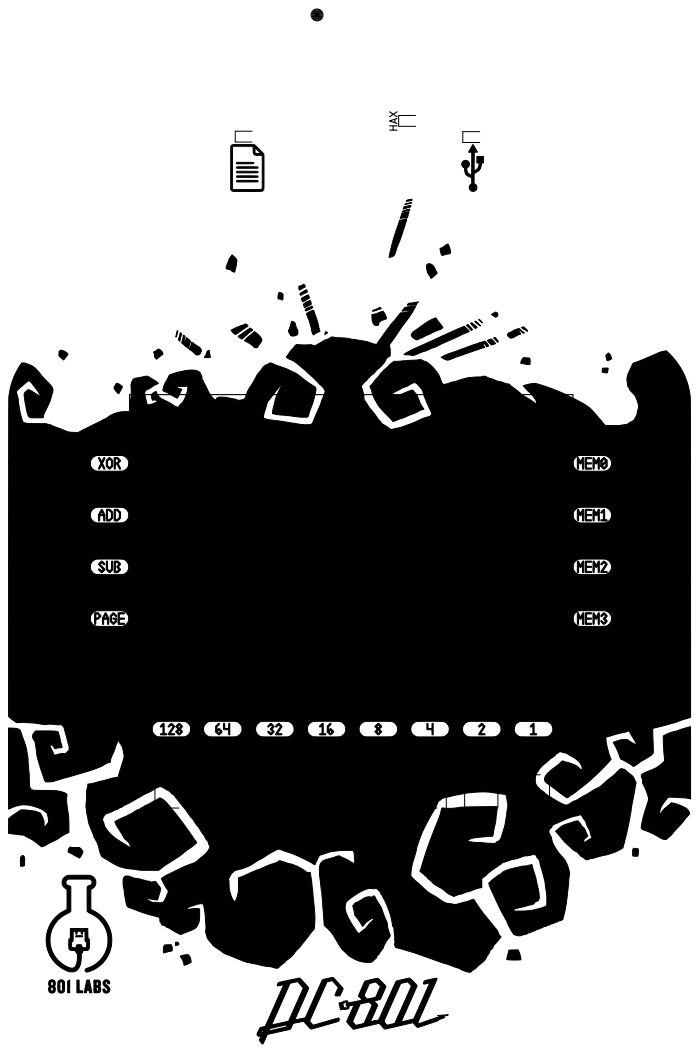
[picture p144: page 14]

@hamster and the dc801 badge team HAX

Id: 1/1 Title: DC801 Badge - BM

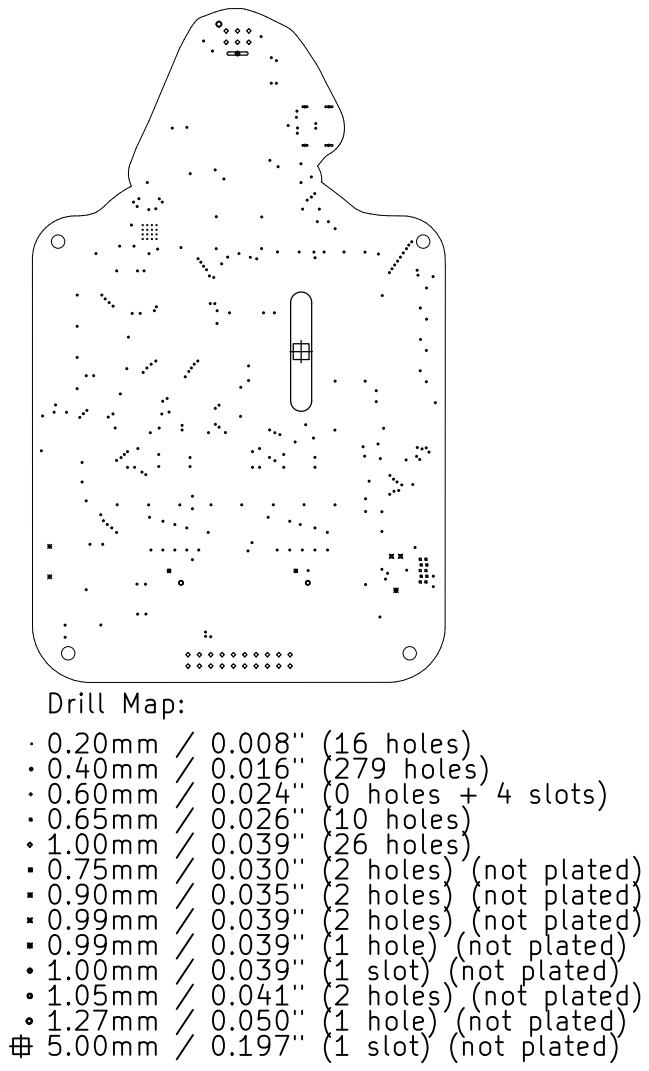
[picture p145: page 15]
