DC801/BM-Badge/Hardware/SAOs/2022 MiniMage/output/Mage-1.1/MiniMageSpells-1.1.pdf

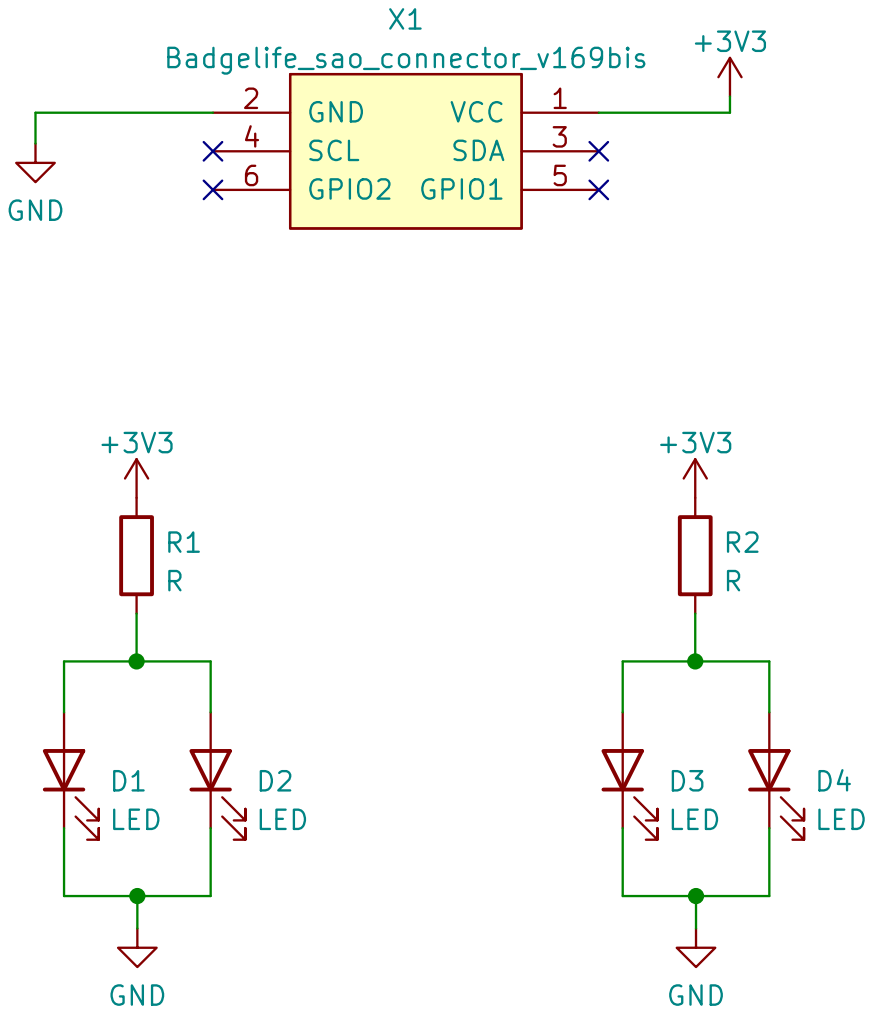
[picture p146: page 1]

R1 R GND
File: MiniMageSpells.kicad_sch Sheet: / DC801 @hamster D4
LED

Id: 1/1 Title: Mini Madge 2022 SAO

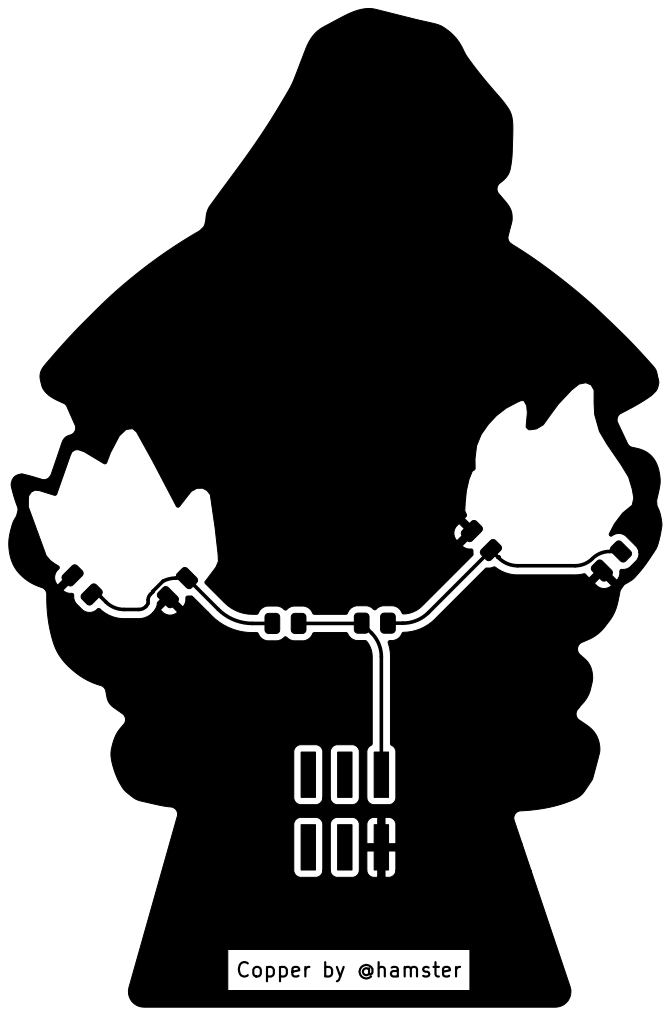
[picture p147: page 2]

File: MiniMageSpells.kicad_pcb Sheet: DC801 @hamster Copper by @hamster

Id: 1/1 Title: Mini Mage 2022 SAO

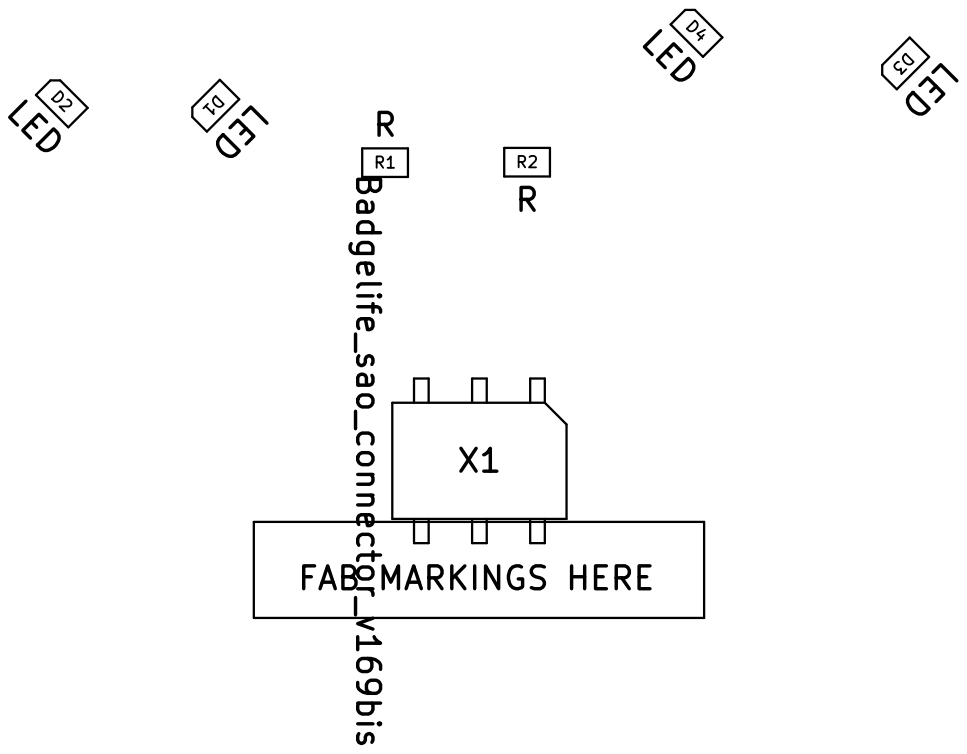
[picture p148: page 3]

File: MiniMageSpells.kicad_pcb Sheet: DC801 @hamster

Id: 1/1 Title: Mini Mage 2022 SAO

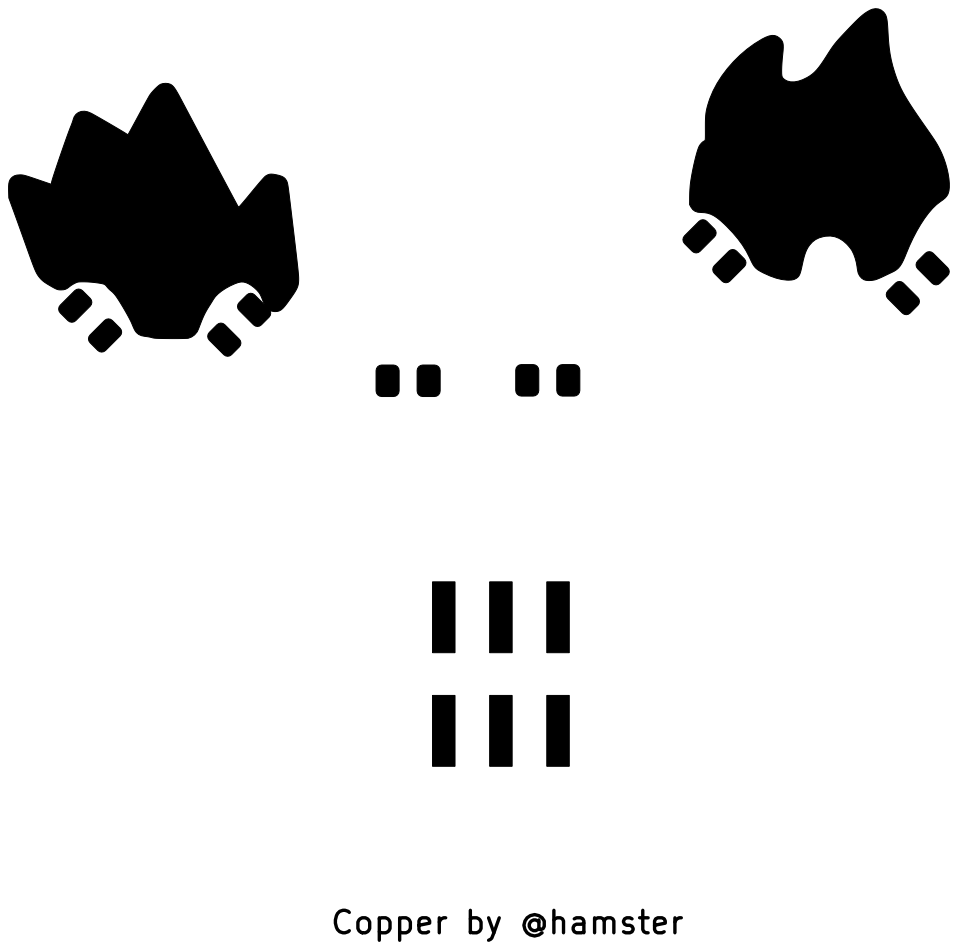
[picture p149: page 4]

File: MiniMageSpells.kicad_pcb Sheet: DC801 @hamster Copper by @hamster

Id: 1/1 Title: Mini Mage 2022 SAO

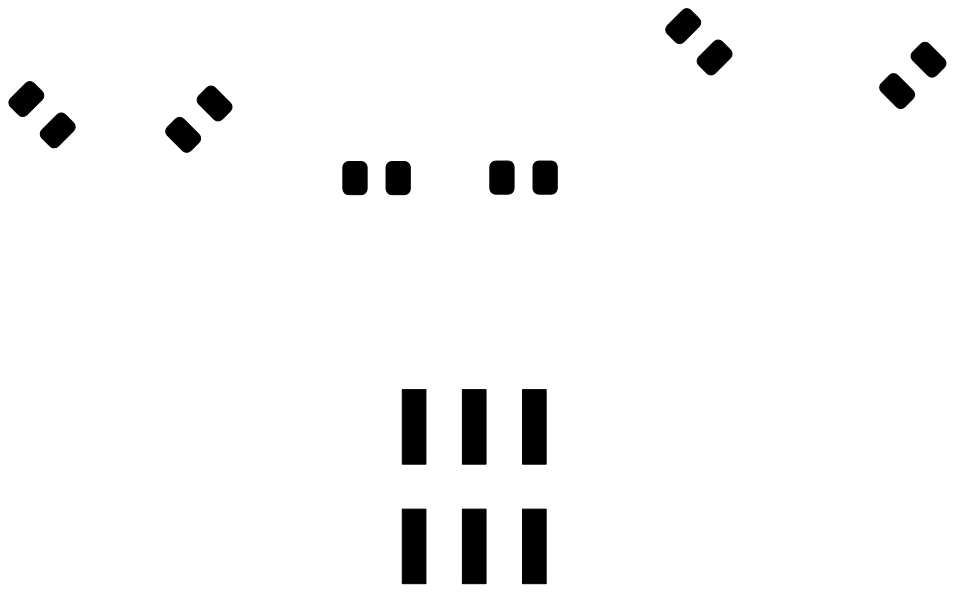
[picture p150: page 5]

File: MiniMageSpells.kicad_pcb Sheet: DC801 @hamster

Id: 1/1 Title: Mini Mage 2022 SAO

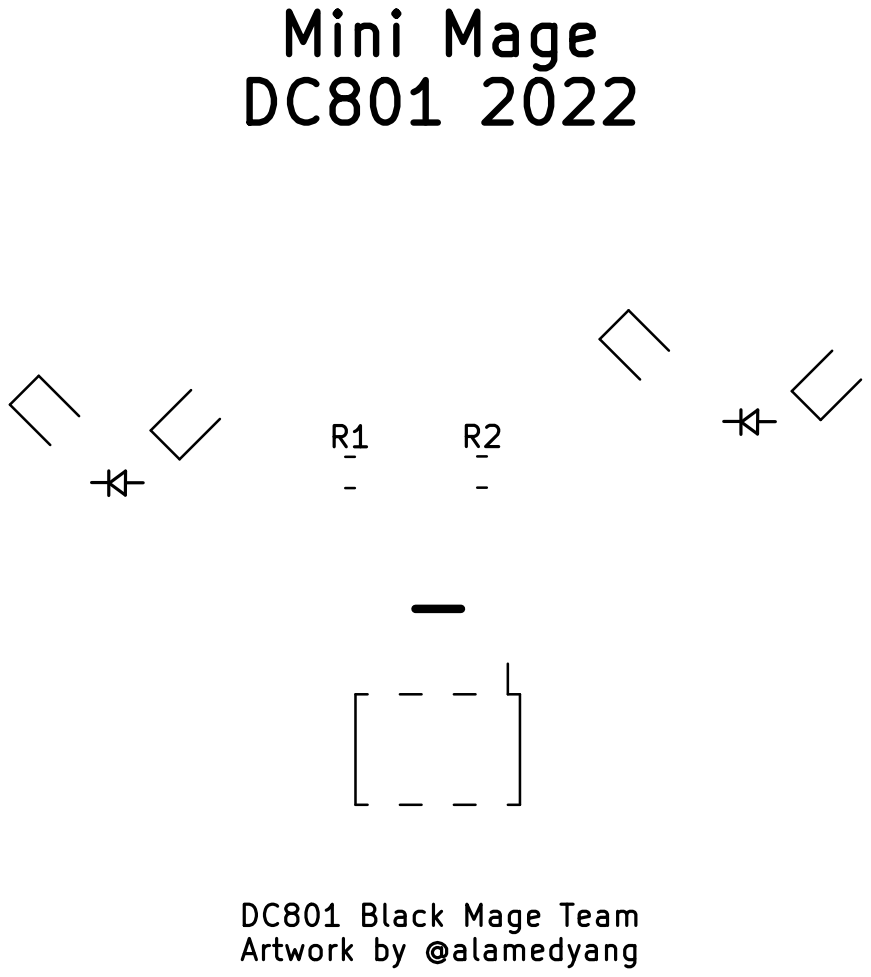
[picture p151: page 6]

Artwork by @alamedyang Mini Mage

File: MiniMageSpells.kicad_pcb Sheet: DC801 @hamster DC801 Black Mage Team

Id: 1/1 Title: Mini Mage 2022 SAO

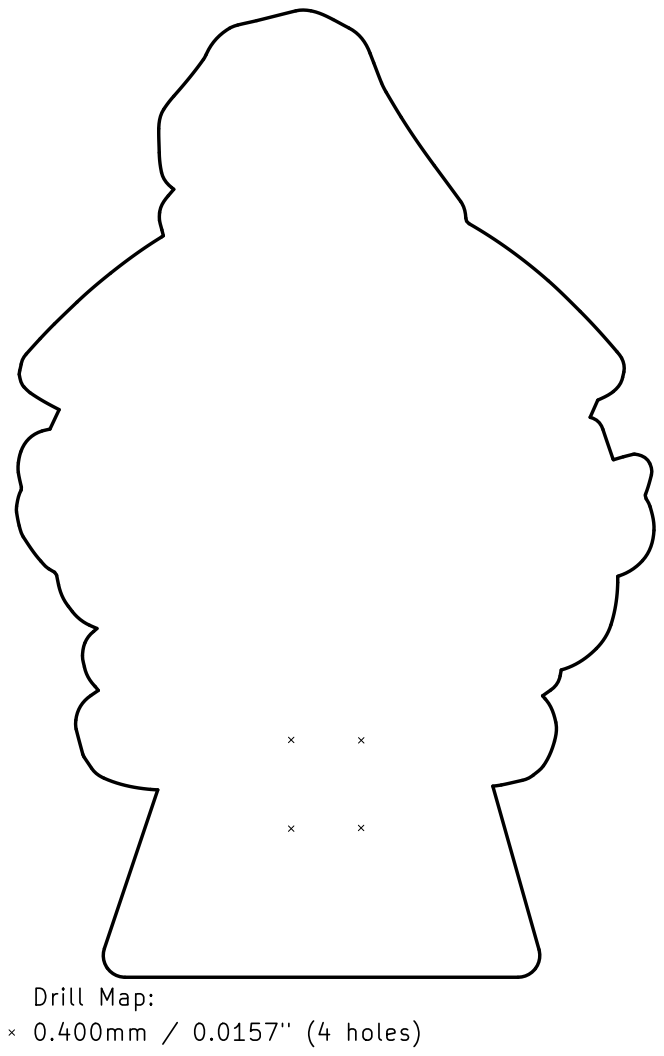
[picture p152: page 7]

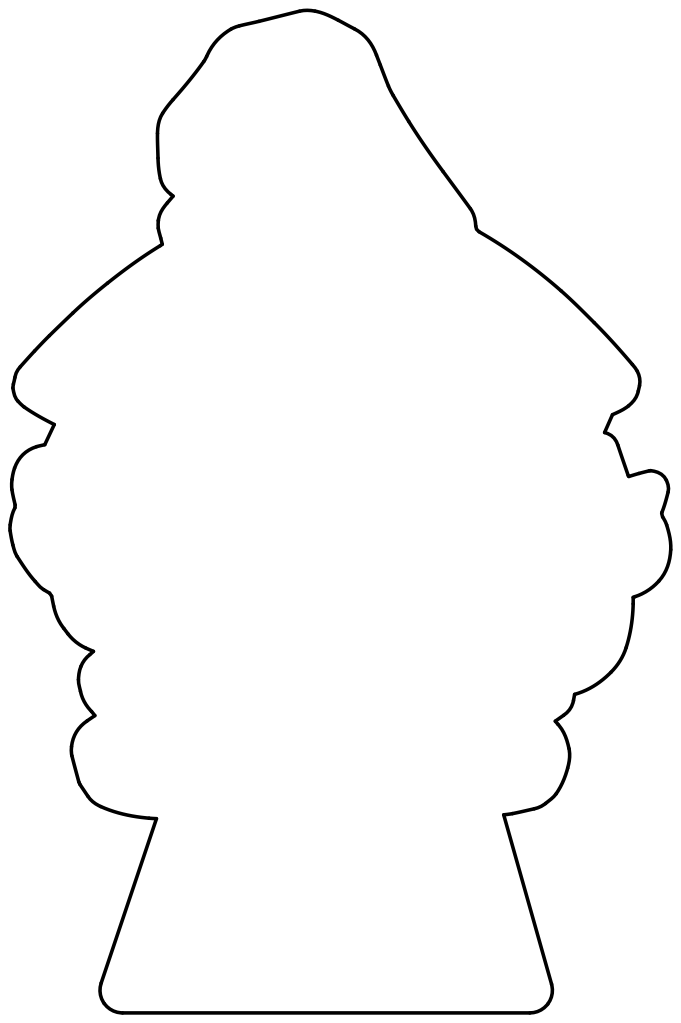
[picture p153: page 8]

File: MiniMageSpells.kicad_pcb Sheet: DC801 @hamster

Id: 1/1 Title: Mini Mage 2022 SAO

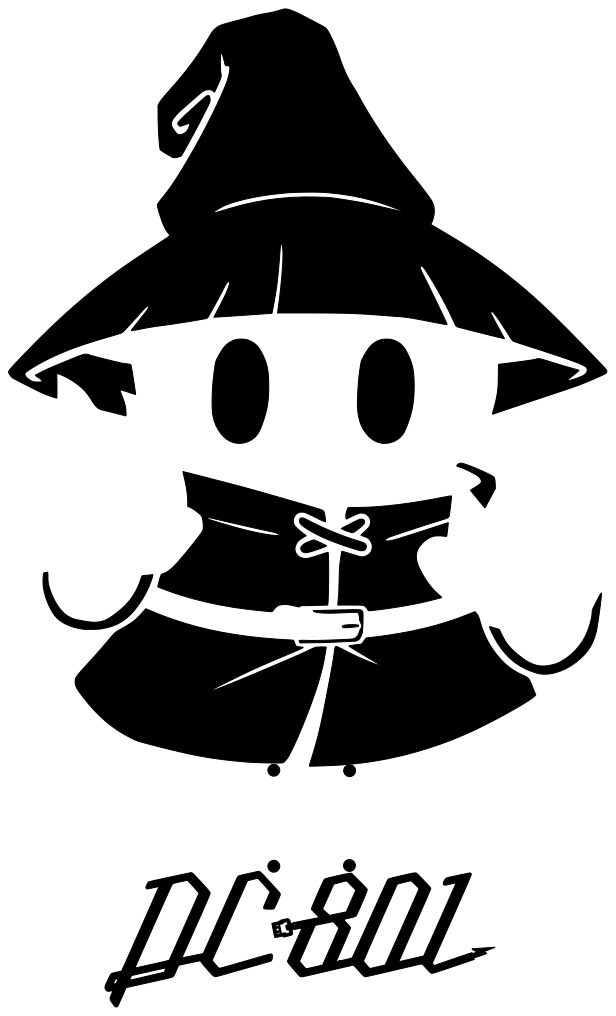
[picture p154: page 9]

File: MiniMageSpells.kicad_pcb Sheet: DC801 @hamster

Id: 1/1 Title: Mini Mage 2022 SAO

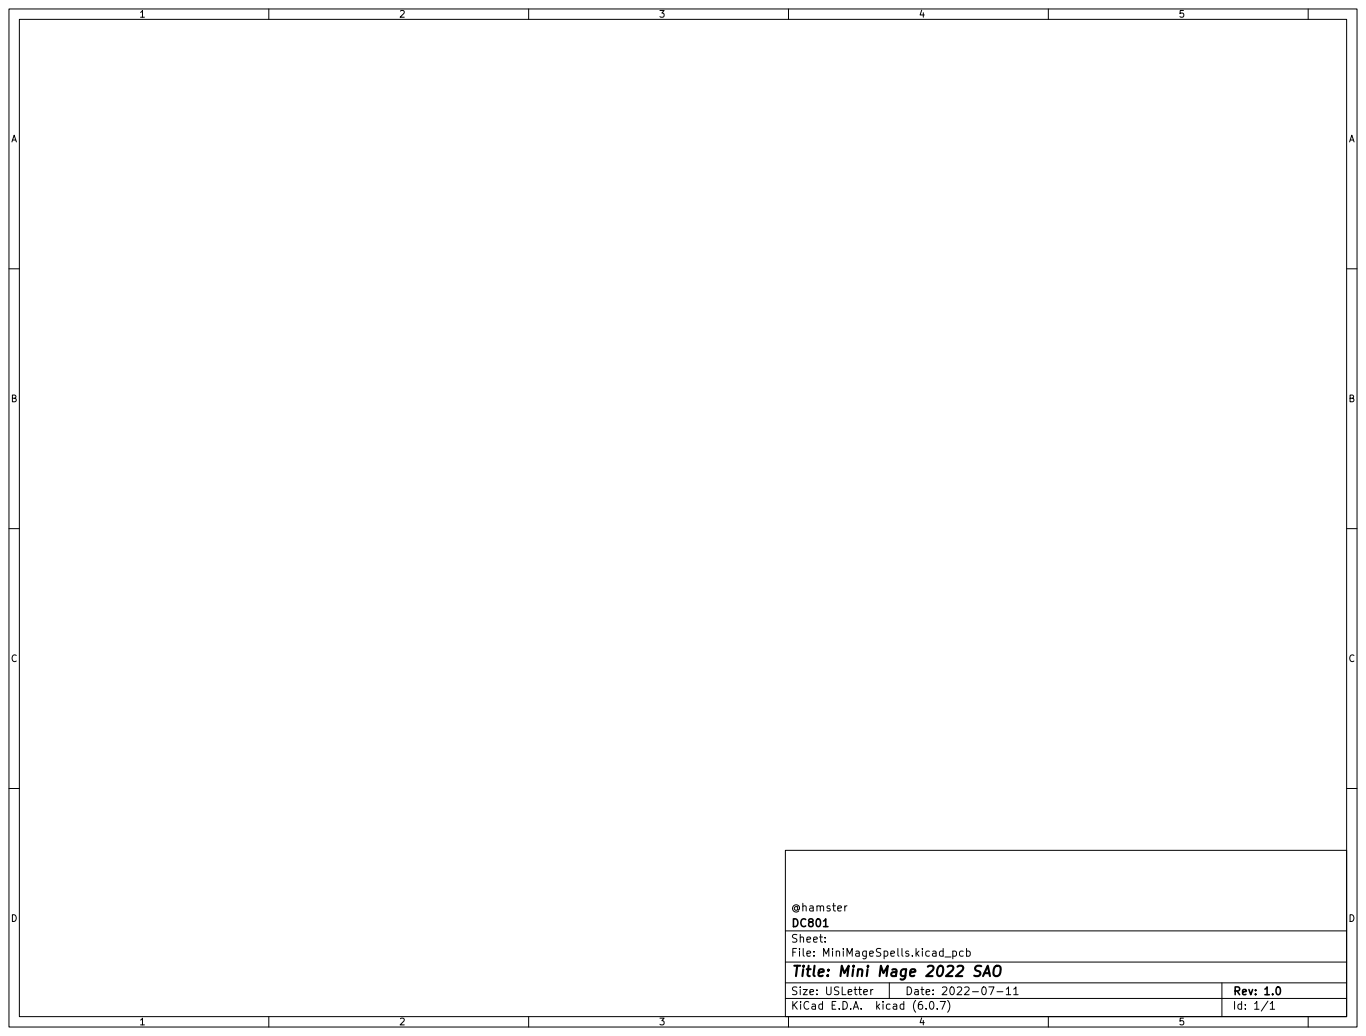
[picture p155: page 10]

File: MiniMageSpells.kicad_pcb Sheet: DC801 @hamster

Id: 1/1 Title: Mini Mage 2022 SAO

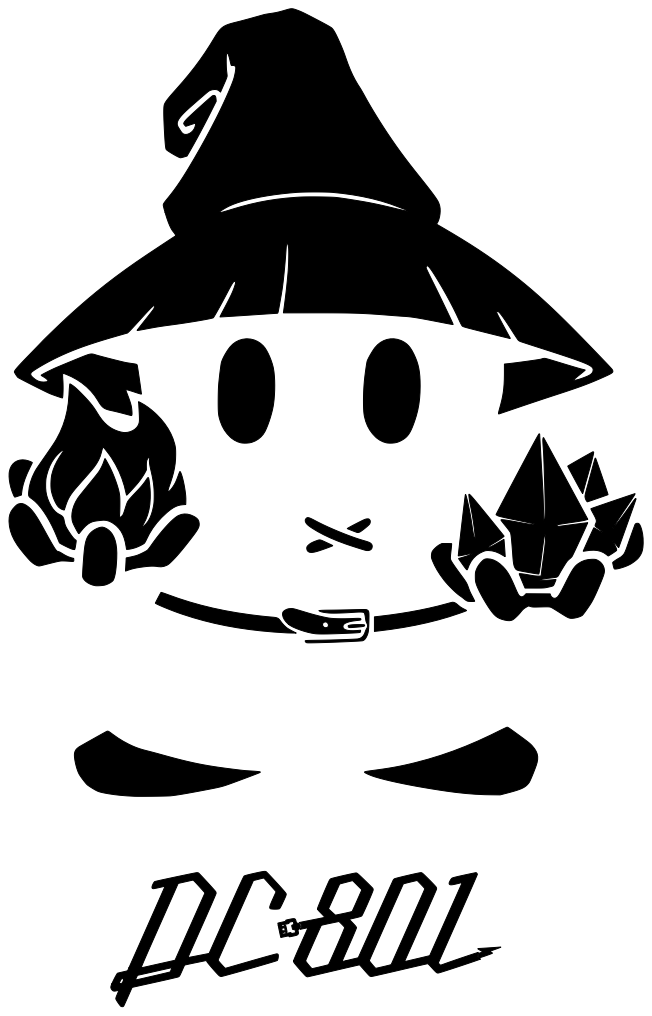
[picture p156: page 11]

File: MiniMageSpells.kicad_pcb Sheet: DC801 @hamster

Id: 1/1 Title: Mini Mage 2022 SAO

File: MiniMageSpells.kicad_pcb Sheet: DC801 @hamster

Id: 1/1 Title: Mini Mage 2022 SAO

File: MiniMageSpells.kicad_pcb Sheet: DC801 @hamster

Id: 1/1 Title: Mini Mage 2022 SAO
