DC801/BM-Badge/Hardware/SAOs/2022 MiniMage/output/Mage-Panel-1.1/MiniMageSpells-panel-1.1.pdf

R1 R GND
File: MiniMageSpells.kicad_sch Sheet: / DC801 @hamster D4
LED

Id: 1/1 Title: Mini Madge 2022 SAO

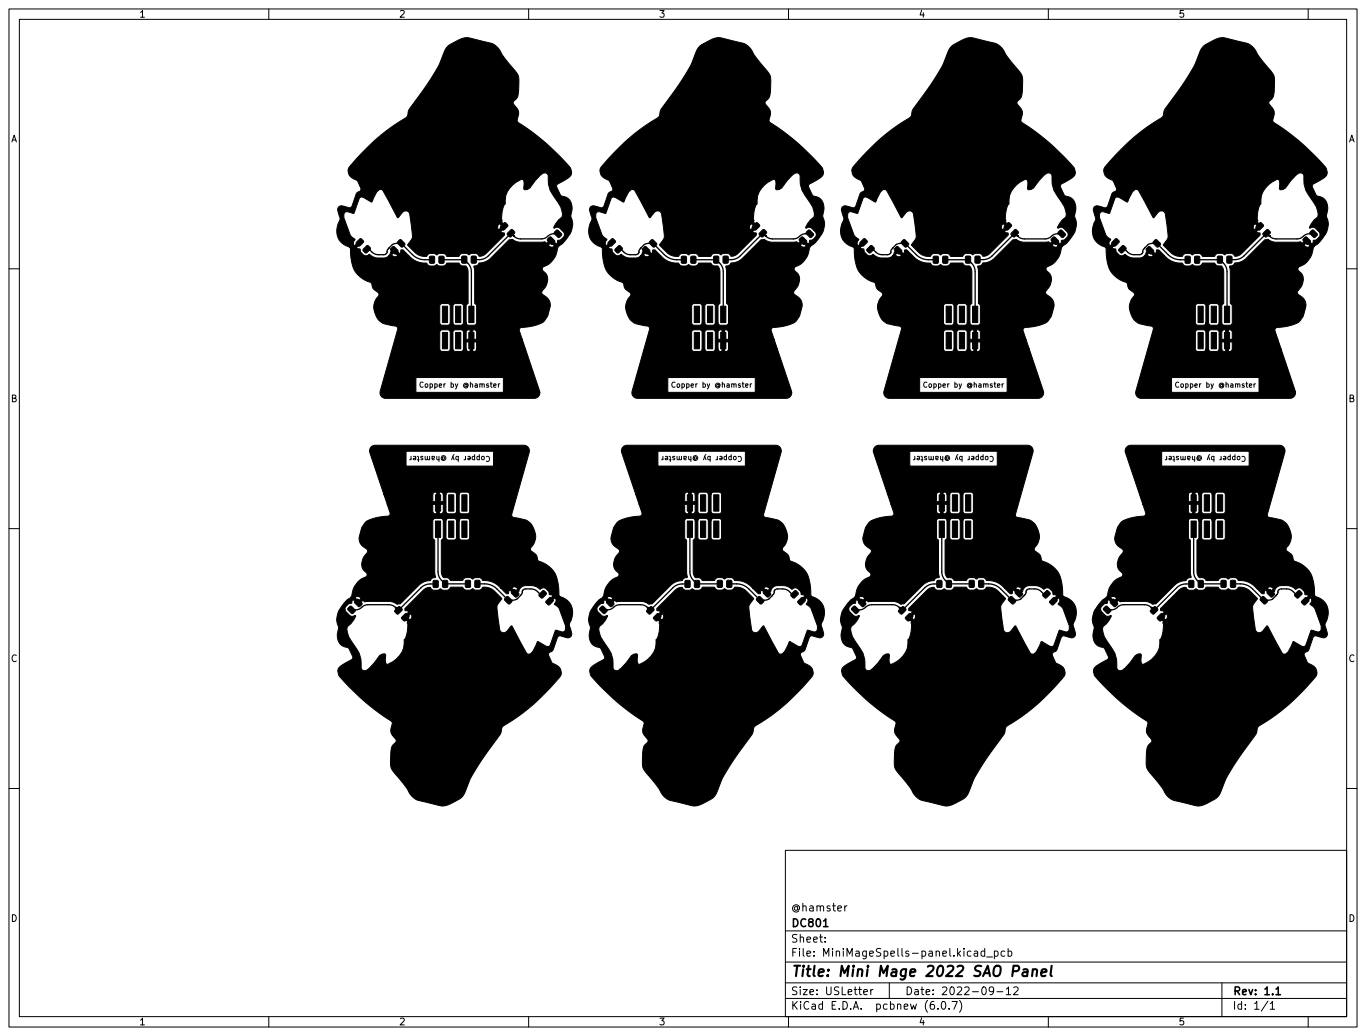
[picture p157: page 2]

File: MiniMageSpells-panel.kicad_pcb Sheet: DC801 @hamster

Id: 1/1 Title: Mini Mage 2022 SAO Panel

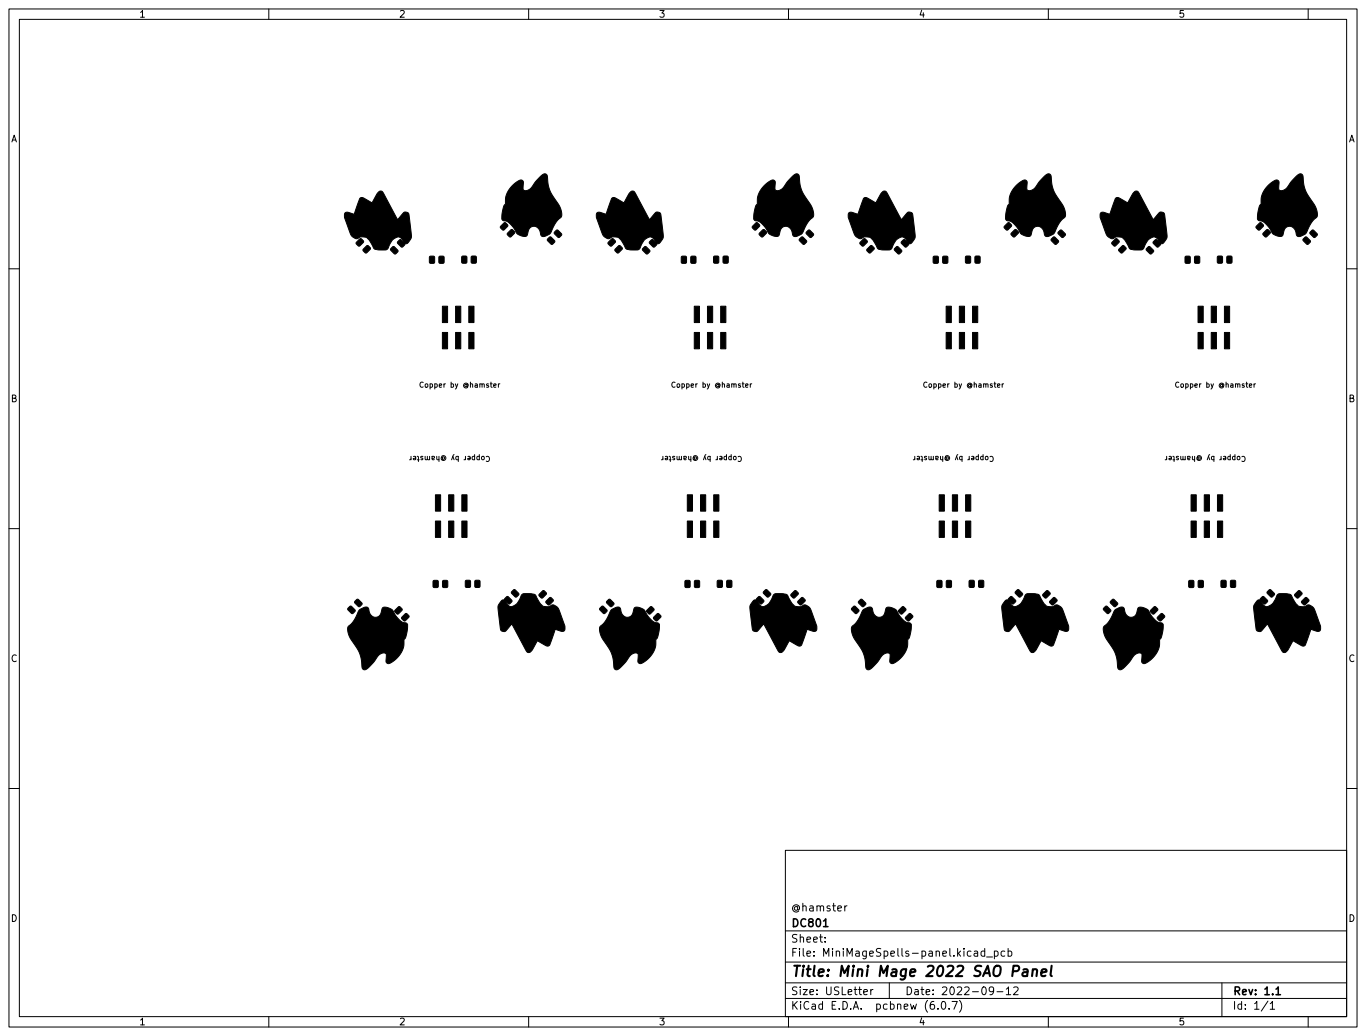
[picture p158: page 3]

File: MiniMageSpells-panel.kicad_pcb Sheet: DC801 @hamster

Id: 1/1 Title: Mini Mage 2022 SAO Panel

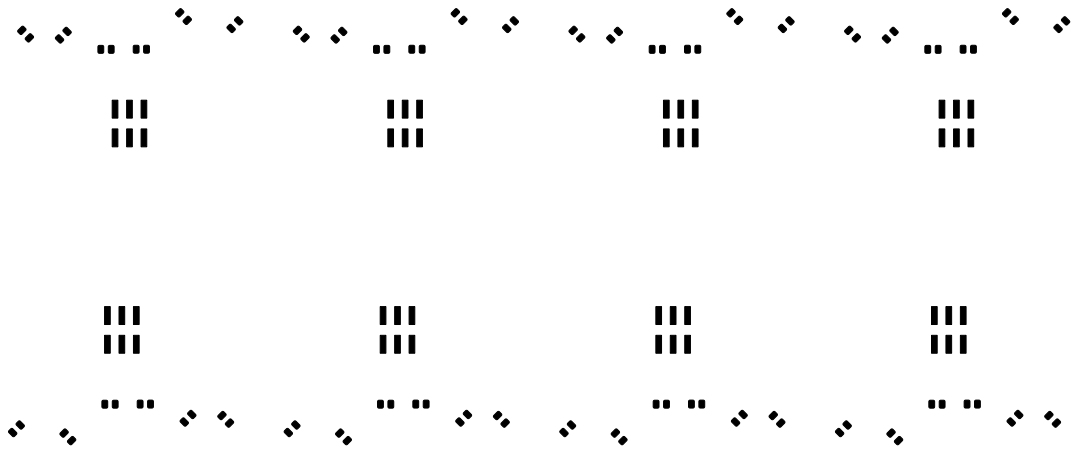
[picture p159: page 4]

File: MiniMageSpells-panel.kicad_pcb Sheet: DC801 @hamster

Id: 1/1 Title: Mini Mage 2022 SAO Panel

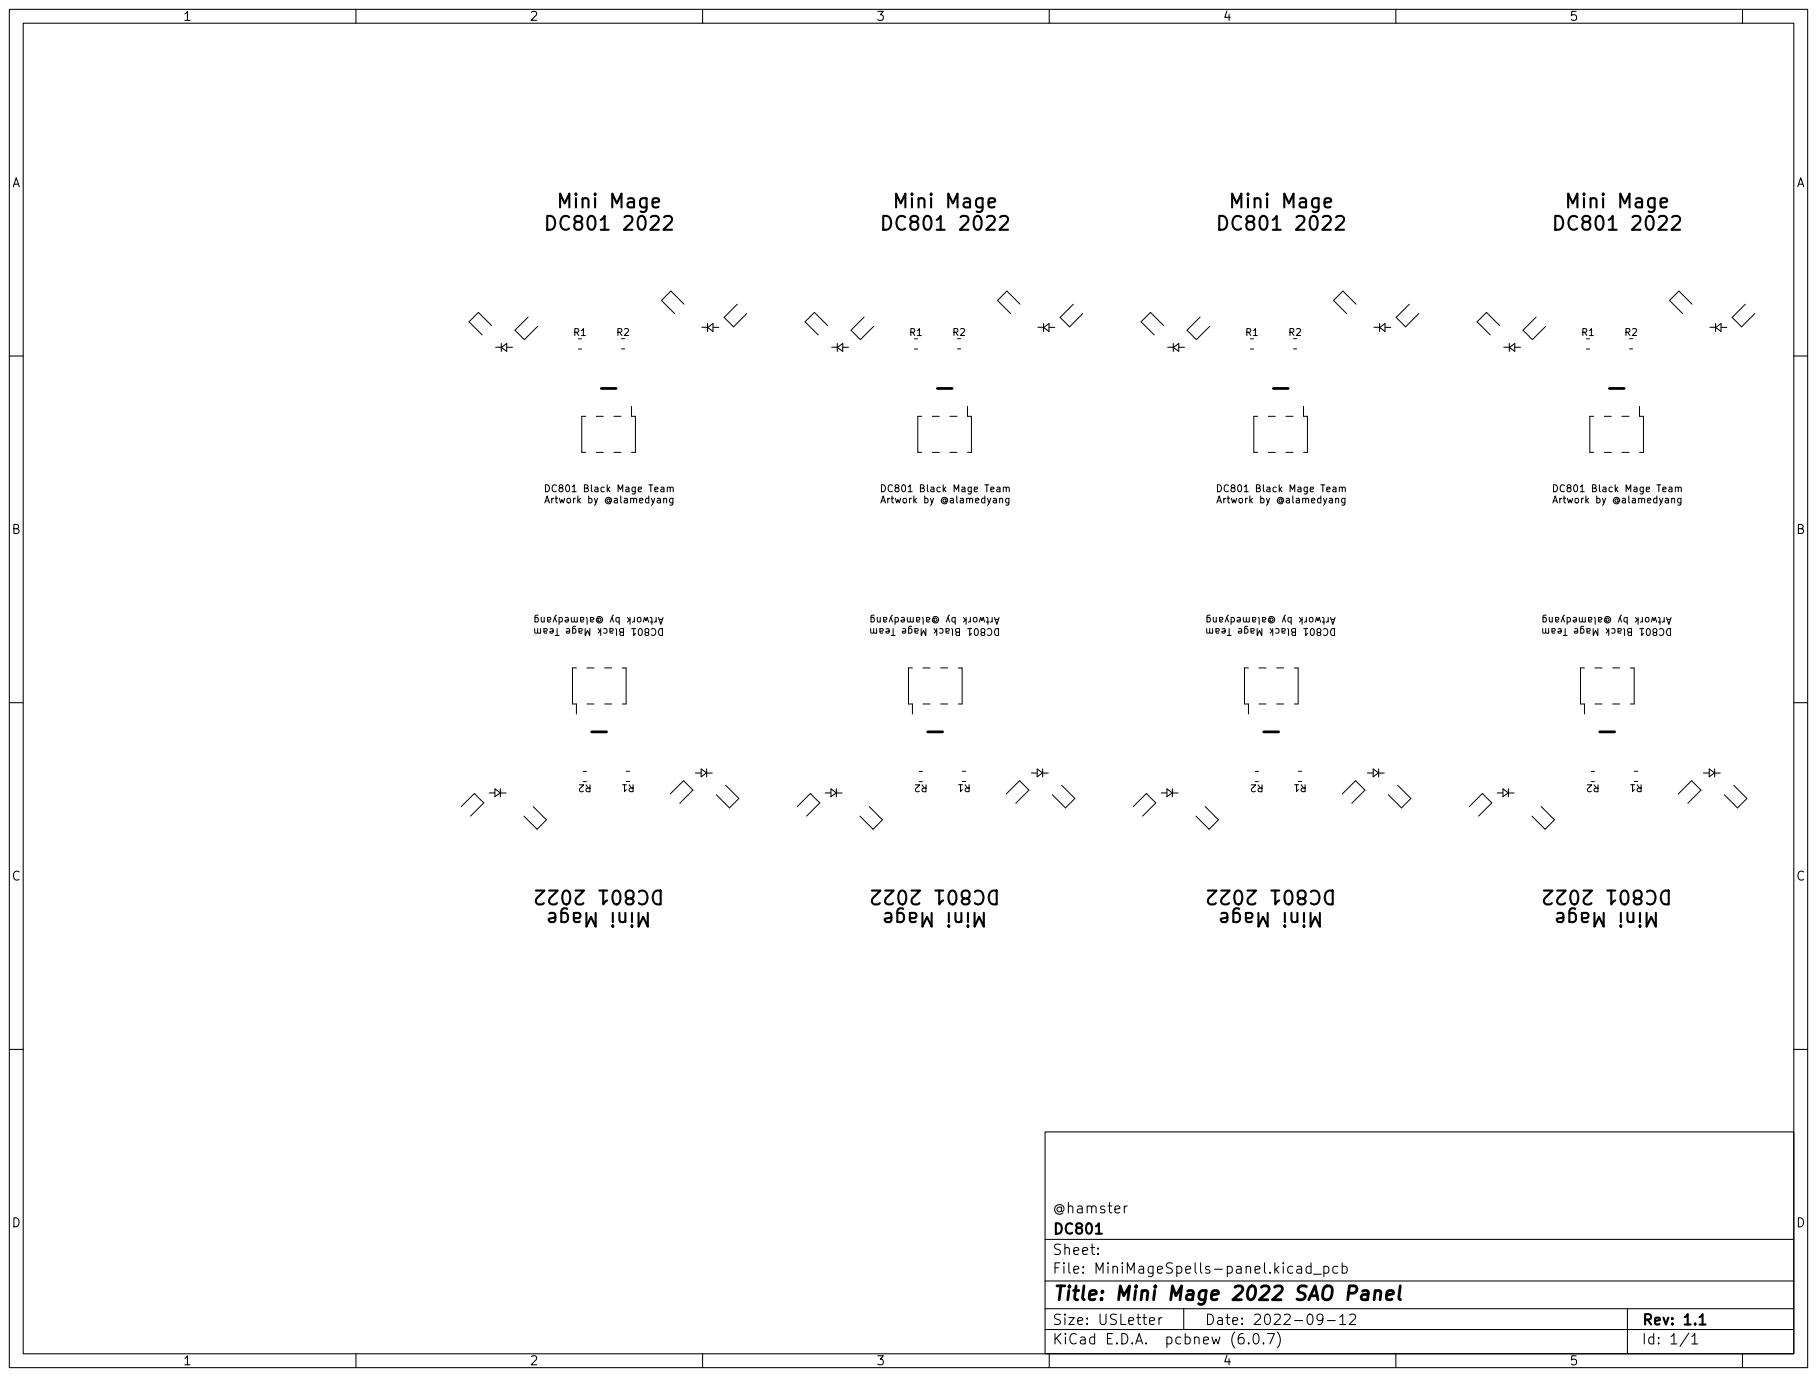
[picture p160: page 5]

Artwork by @alamedyang DC801 Black Mage Team

File: MiniMageSpells-panel.kicad_pcb Sheet: DC801 @hamster

Id: 1/1 Title: Mini Mage 2022 SAO Panel

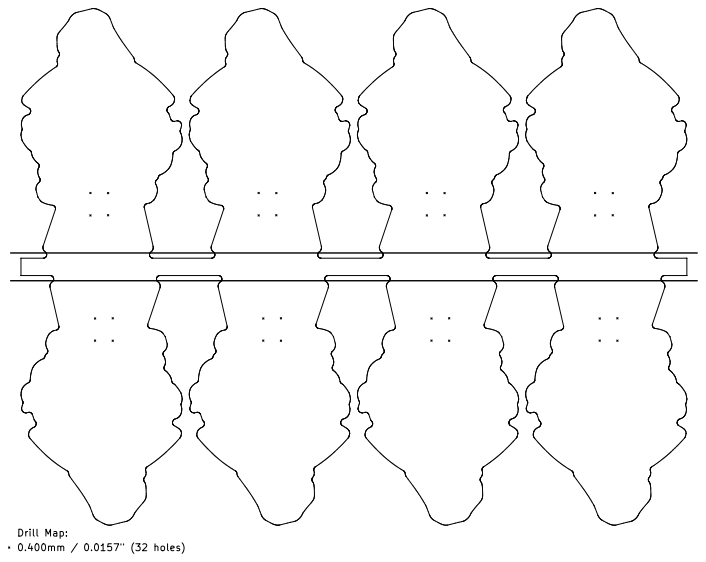
[picture p161: page 6]

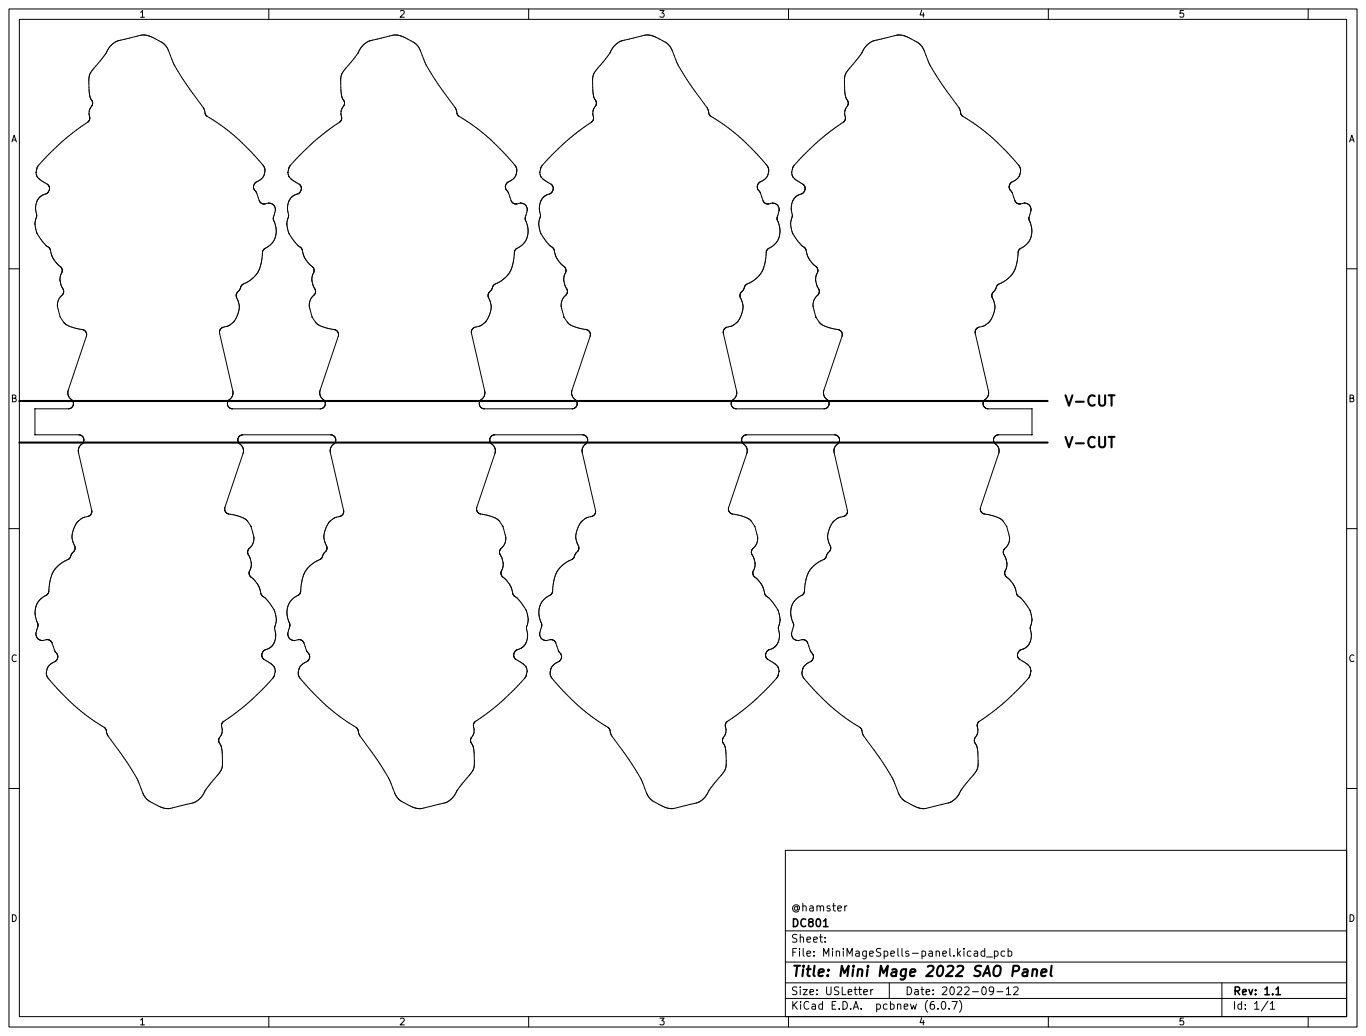
[picture p162: page 7]

File: MiniMageSpells-panel.kicad_pcb Sheet: DC801 @hamster

Id: 1/1 Title: Mini Mage 2022 SAO Panel

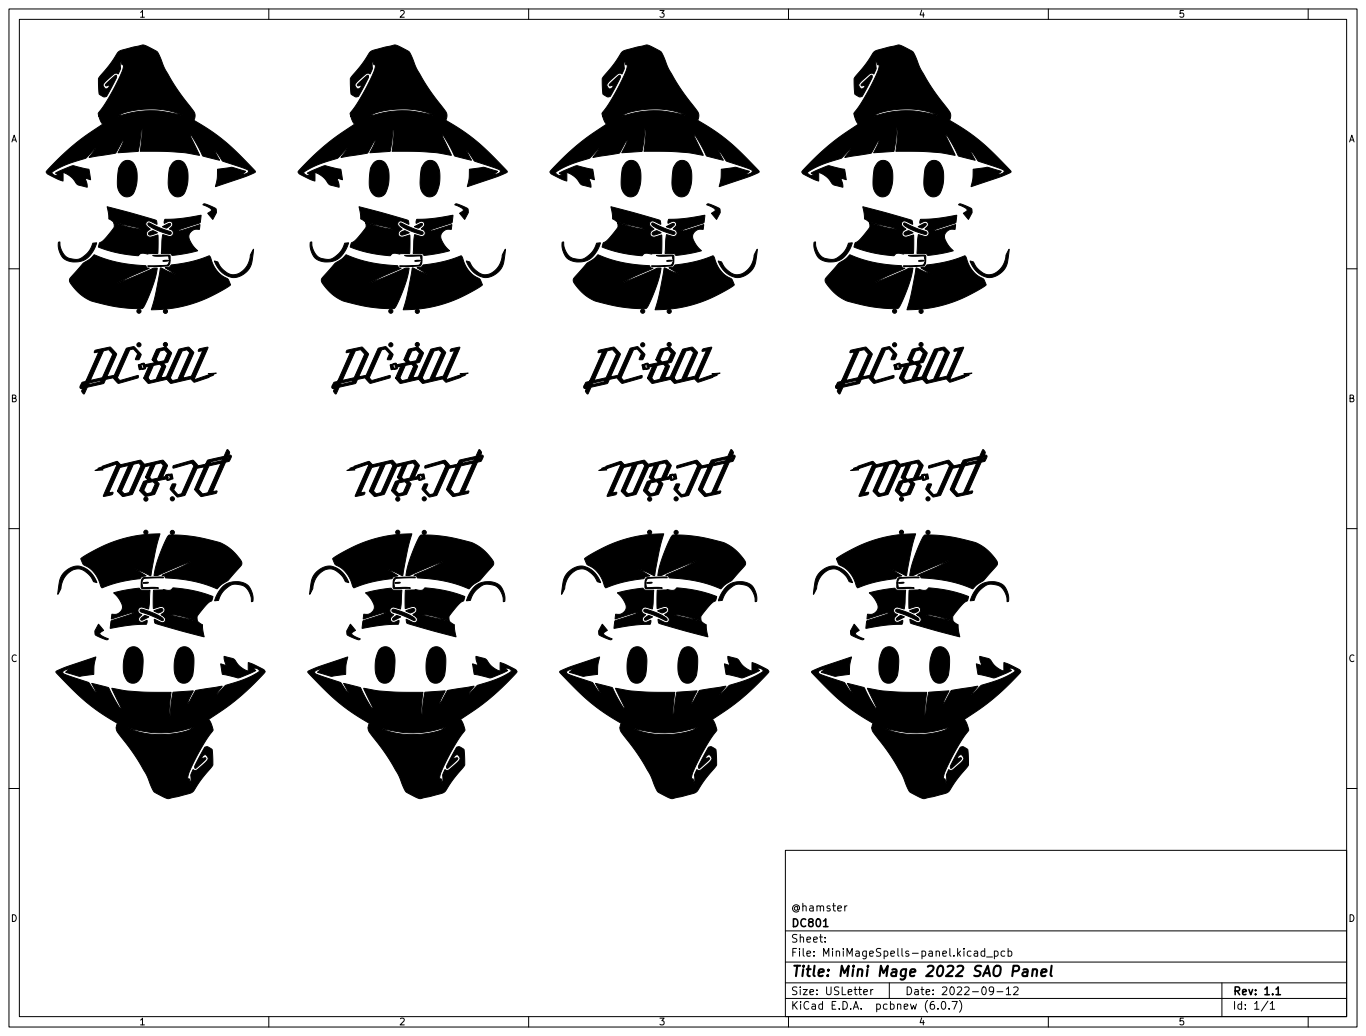
[picture p163: page 8]

File: MiniMageSpells-panel.kicad_pcb Sheet: DC801 @hamster

Id: 1/1 Title: Mini Mage 2022 SAO Panel

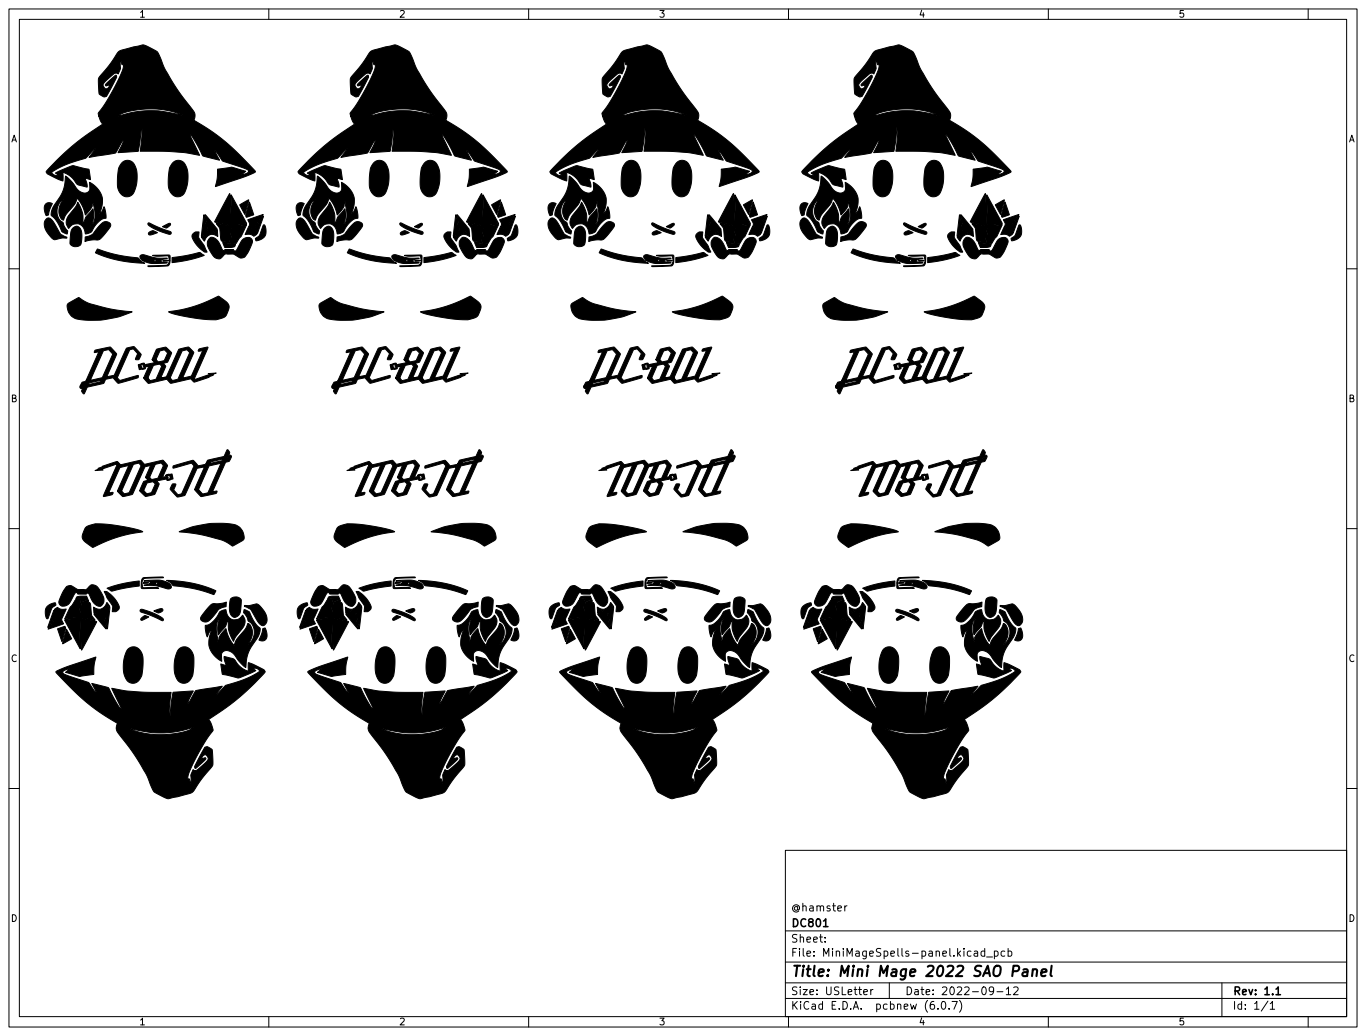
[picture p164: page 9]

File: MiniMageSpells-panel.kicad_pcb Sheet: DC801 @hamster

Id: 1/1 Title: Mini Mage 2022 SAO Panel

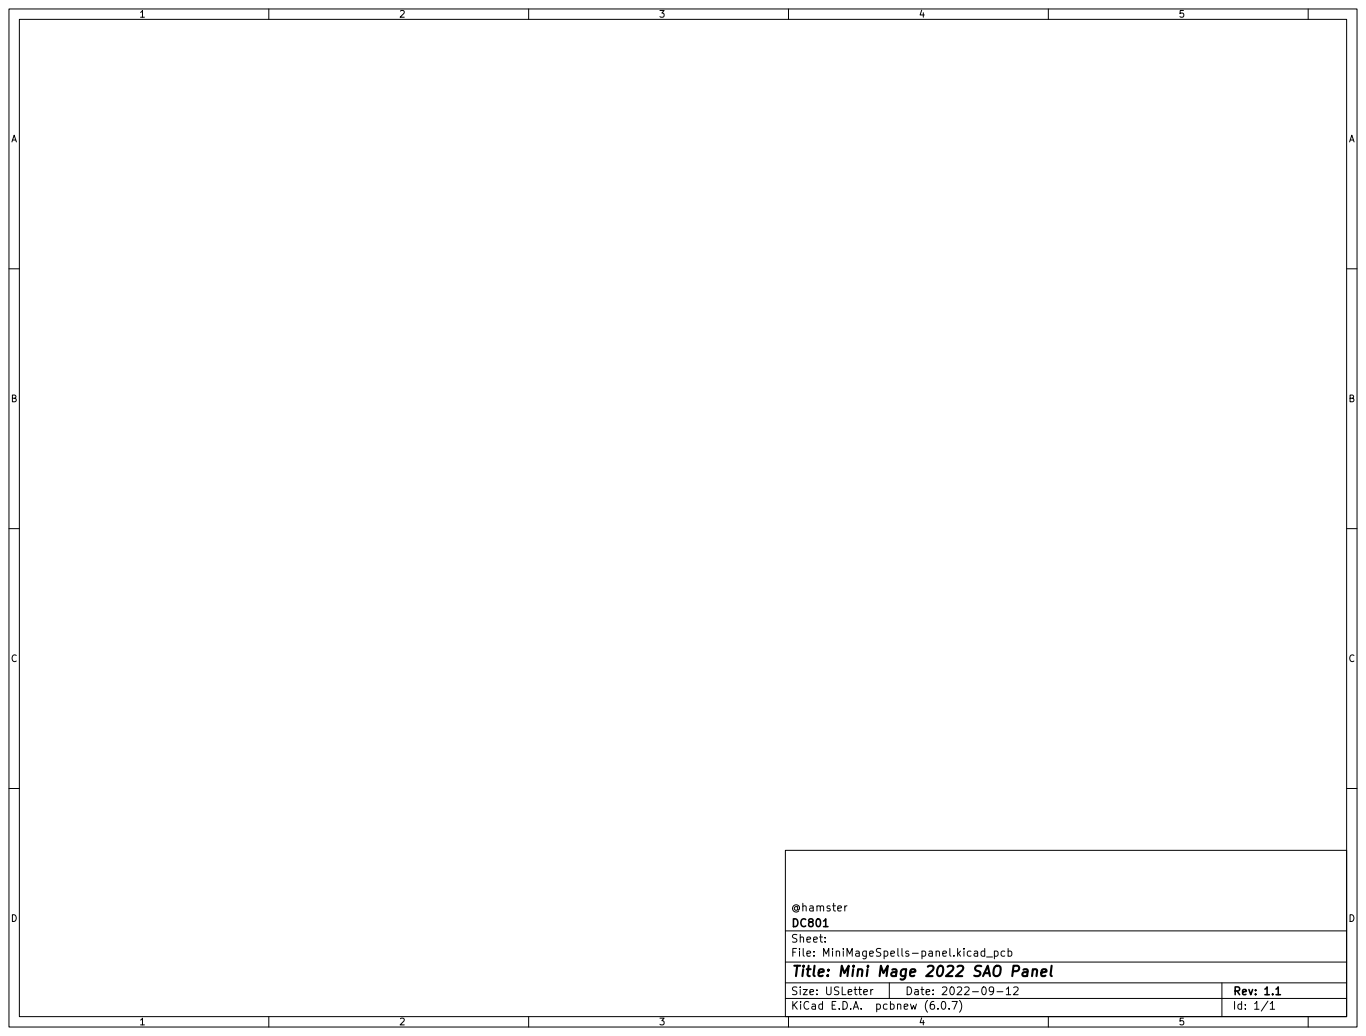
[picture p165: page 10]

File: MiniMageSpells-panel.kicad_pcb Sheet: DC801 @hamster

Id: 1/1 Title: Mini Mage 2022 SAO Panel

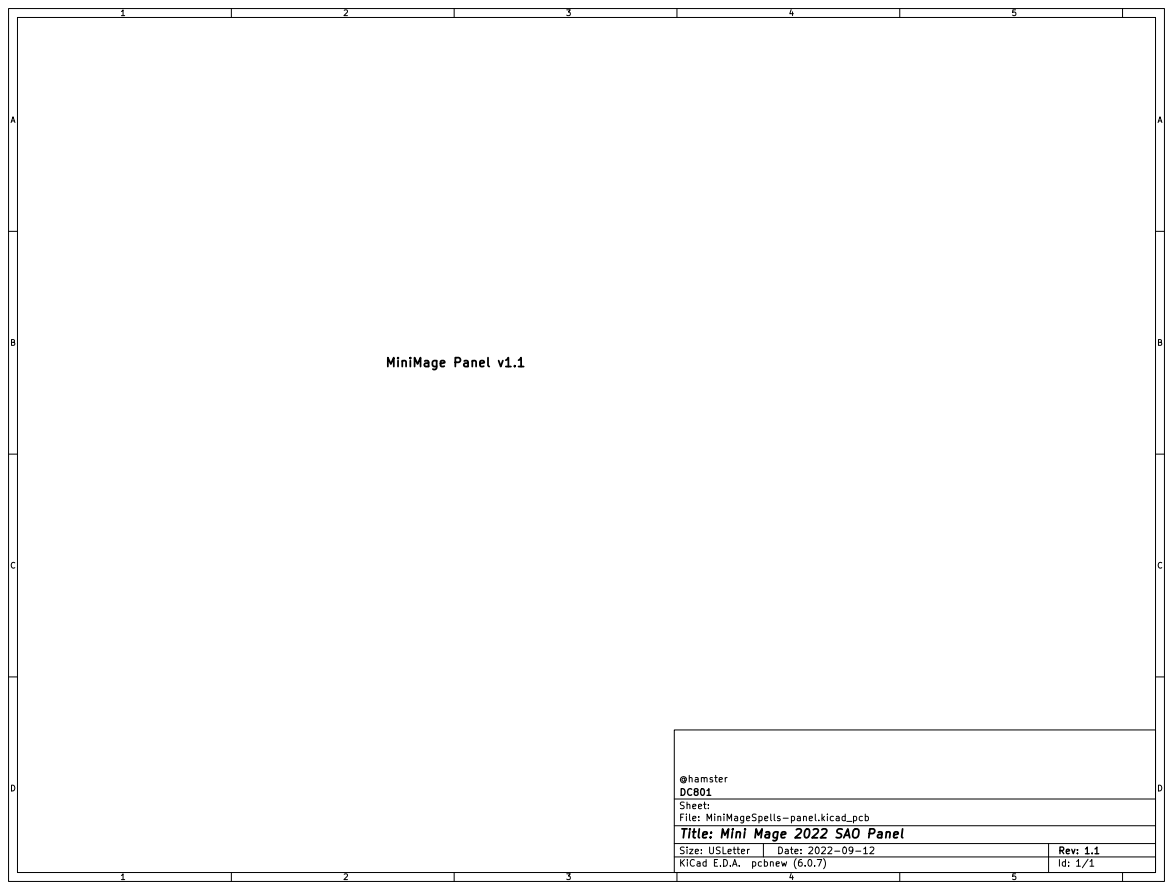
[picture p166: page 11]

File: MiniMageSpells-panel.kicad_pcb Sheet: DC801 @hamster

Id: 1/1 Title: Mini Mage 2022 SAO Panel
