DC801/BM-Badge/Hardware/SAOs/2022 MiniMage/output/Mage-1.0/MiniMageSpells-1.0.pdf

R1 R GND
File: MiniMageSpells.kicad_sch Sheet: / DC801 @hamster D4
LED

Id: 1/1 Title: Mini Madge 2022 SAO

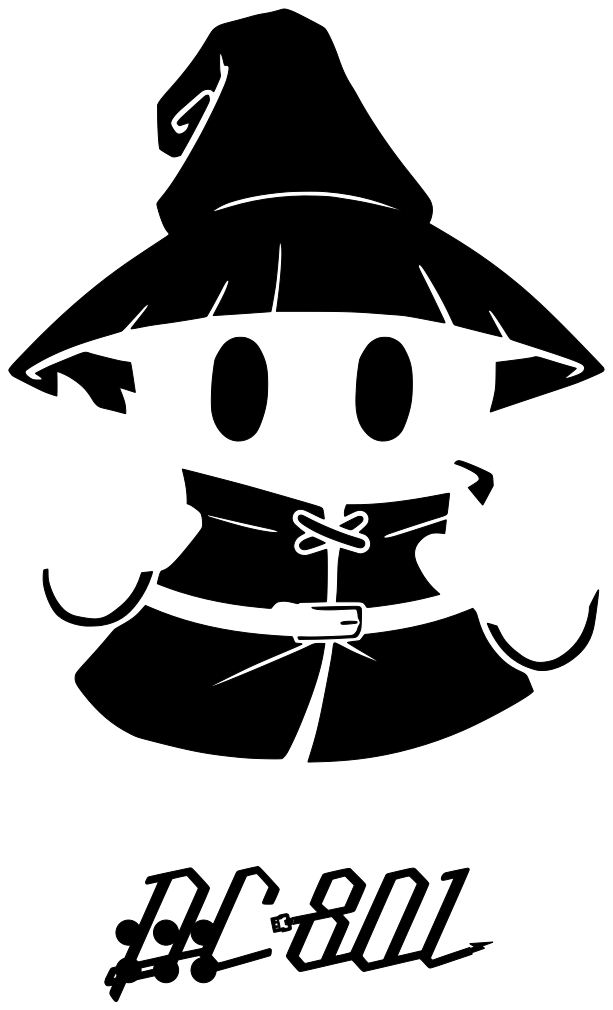
[picture p167: page 2]

File: MiniMageSpells.kicad_pcb Sheet: DC801 @hamster

Id: 1/1 Title: Mini Mage 2022 SAO

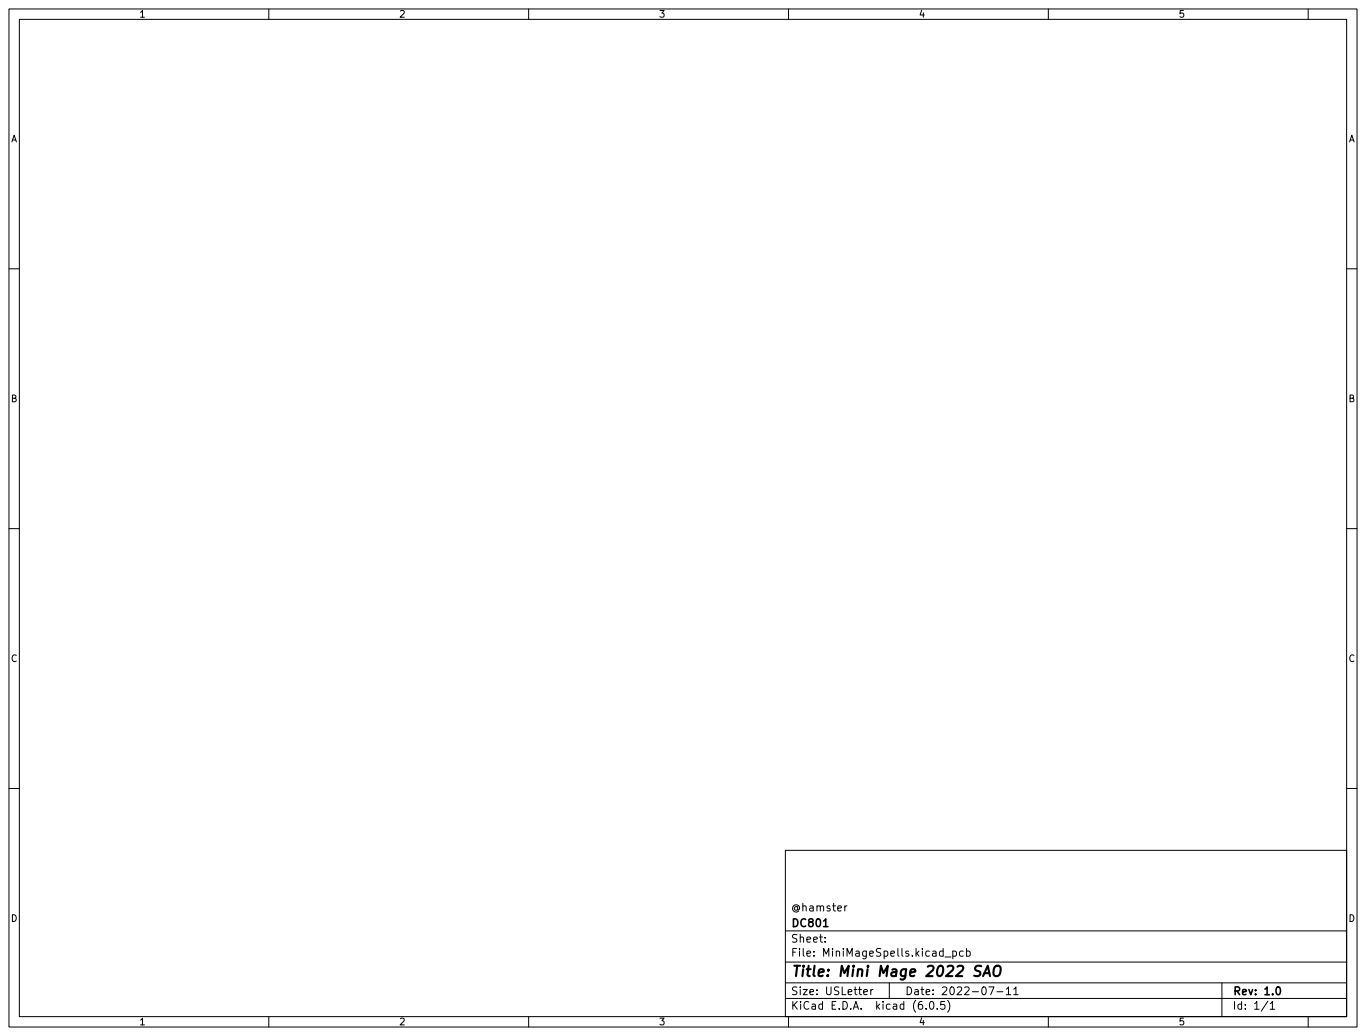
[picture p168: page 3]

File: MiniMageSpells.kicad_pcb Sheet: DC801 @hamster

Id: 1/1 Title: Mini Mage 2022 SAO

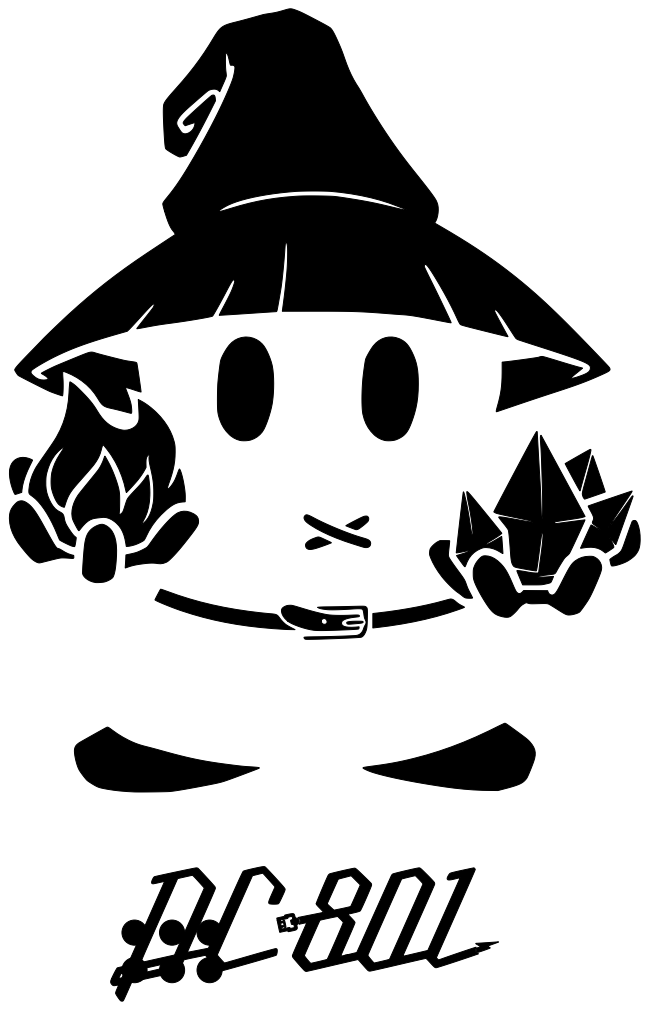
[picture p169: page 4]

File: MiniMageSpells.kicad_pcb Sheet: DC801 @hamster

Id: 1/1 Title: Mini Mage 2022 SAO

File: MiniMageSpells.kicad_pcb Sheet: DC801 @hamster

Id: 1/1 Title: Mini Mage 2022 SAO

File: MiniMageSpells.kicad_pcb Sheet: DC801 @hamster

Id: 1/1 Title: Mini Mage 2022 SAO

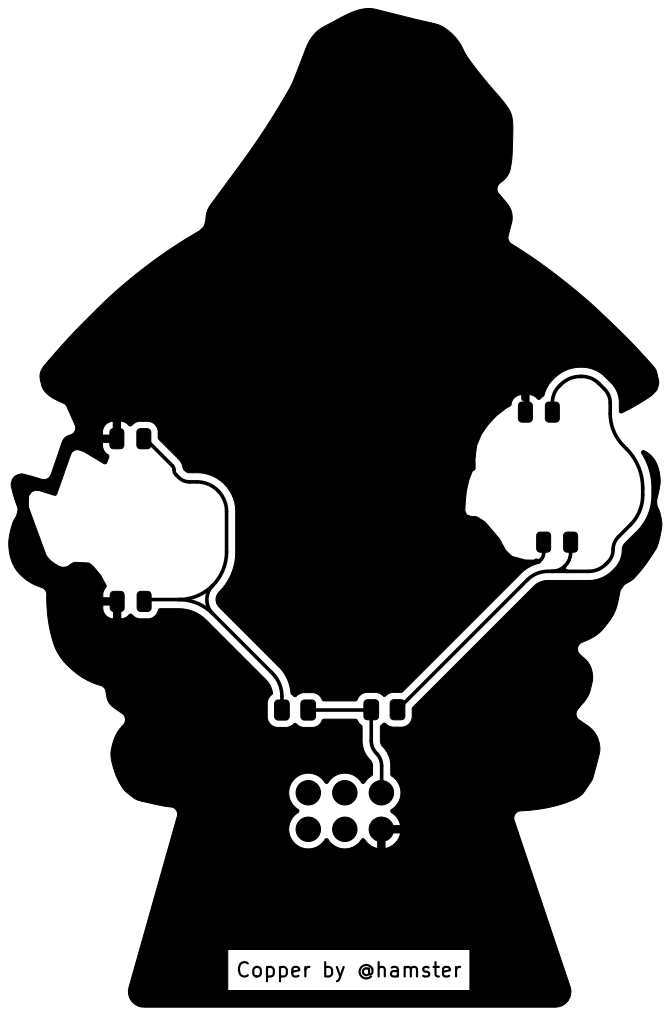
[picture p170: page 7]

File: MiniMageSpells.kicad_pcb Sheet: DC801 @hamster Copper by @hamster

Id: 1/1 Title: Mini Mage 2022 SAO

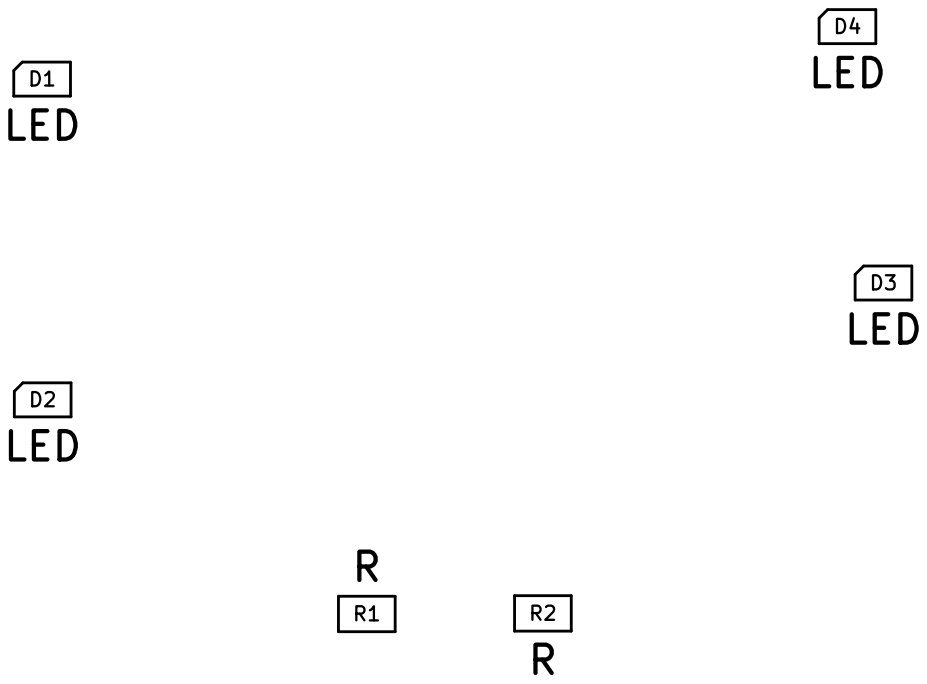
[picture p171: page 8]

File: MiniMageSpells.kicad_pcb Sheet: DC801 @hamster

Id: 1/1 Title: Mini Mage 2022 SAO

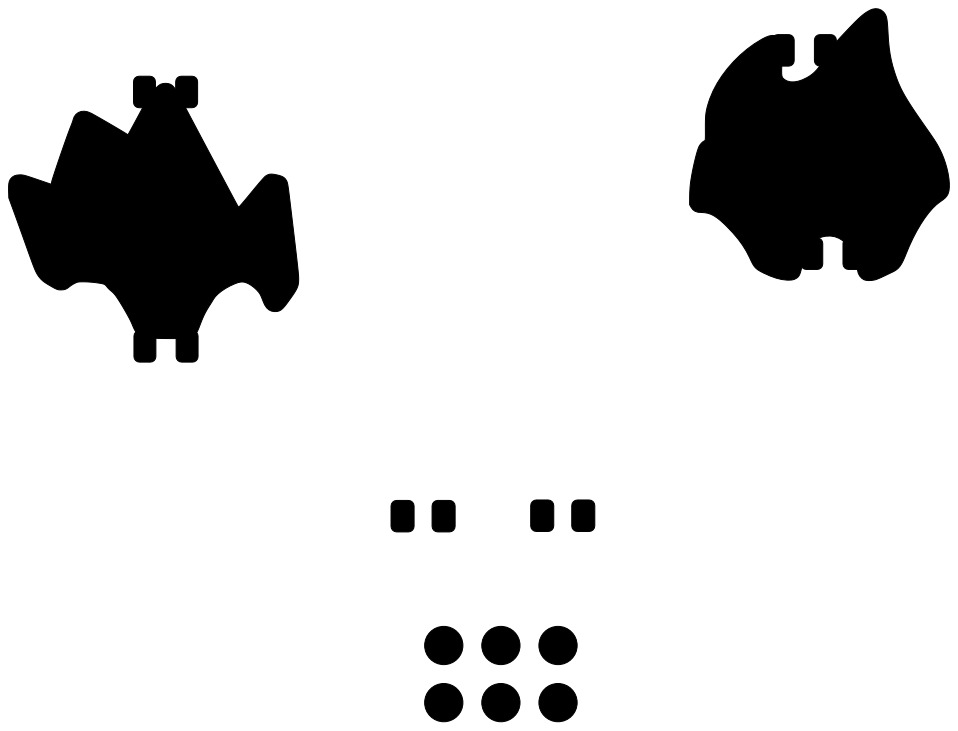
[picture p172: page 9]

File: MiniMageSpells.kicad_pcb Sheet: DC801 @hamster

Id: 1/1 Title: Mini Mage 2022 SAO

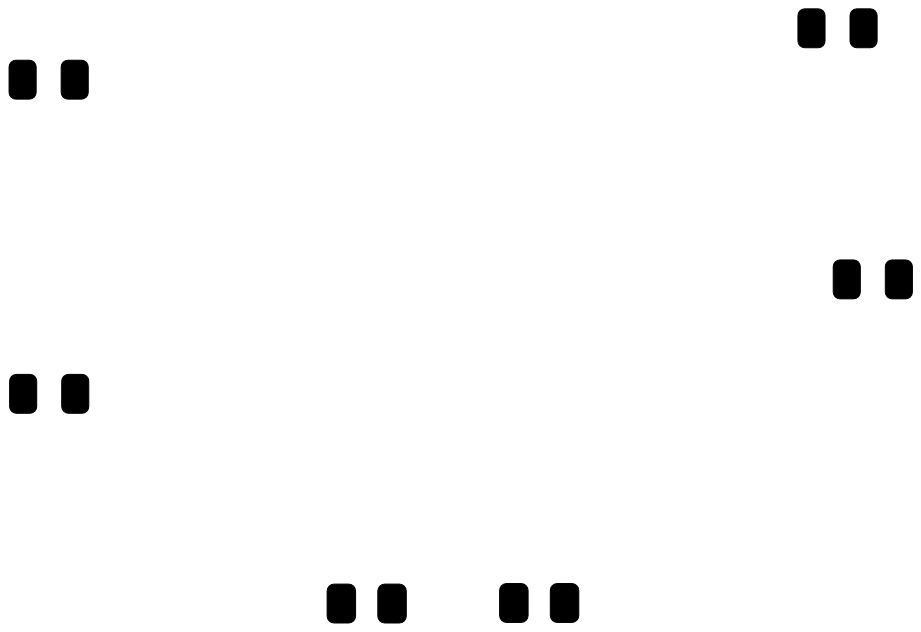
[picture p173: page 10]

File: MiniMageSpells.kicad_pcb Sheet: DC801 @hamster

Id: 1/1 Title: Mini Mage 2022 SAO

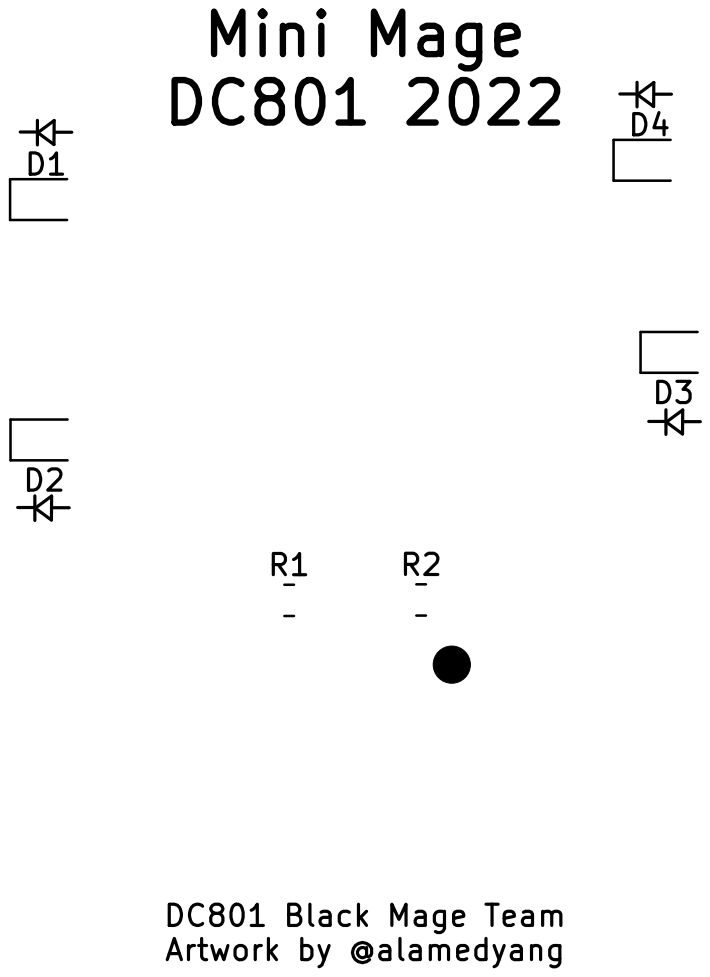
[picture p174: page 11]

File: MiniMageSpells.kicad_pcb Sheet: DC801 @hamster

Id: 1/1 Title: Mini Mage 2022 SAO


File: MiniMageSpells.kicad_pcb Sheet: DC801 @hamster

Id: 1/1 Title: Mini Mage 2022 SAO

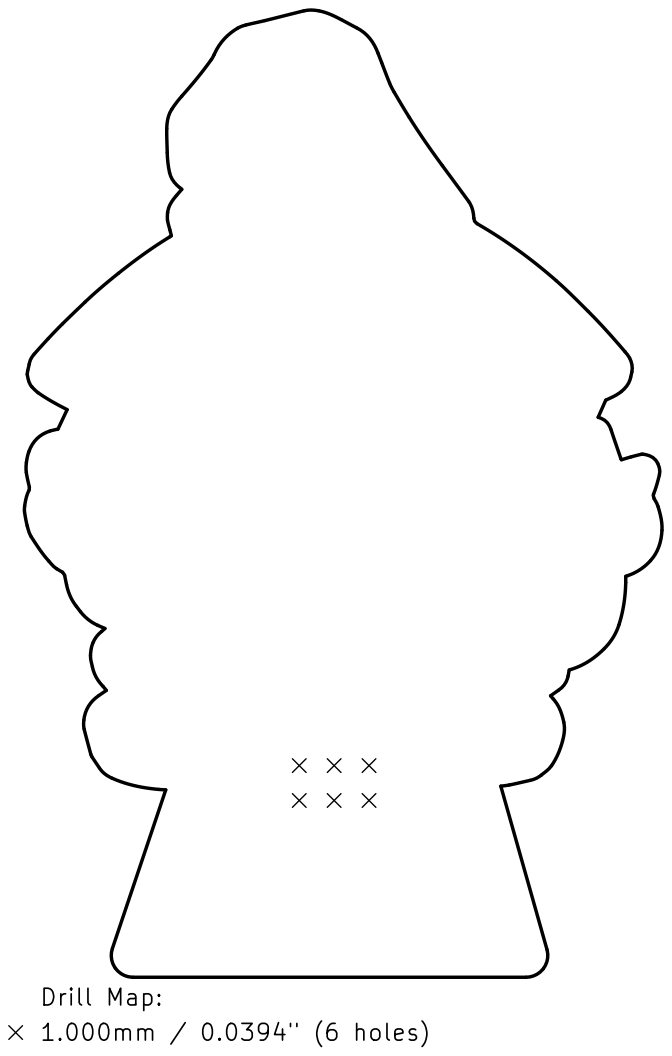
[picture p175: page 13]
