DC801/BM-Badge/HW/ART/2020/output/purplewizard-ART-2020-complete.pdf

@hamster and the dc801 badge team

codename purplewizard
File: purplewizard-ART.sch Sheet: / DC801

Id: 1/1 Title: DC801 Badge - ART 2020

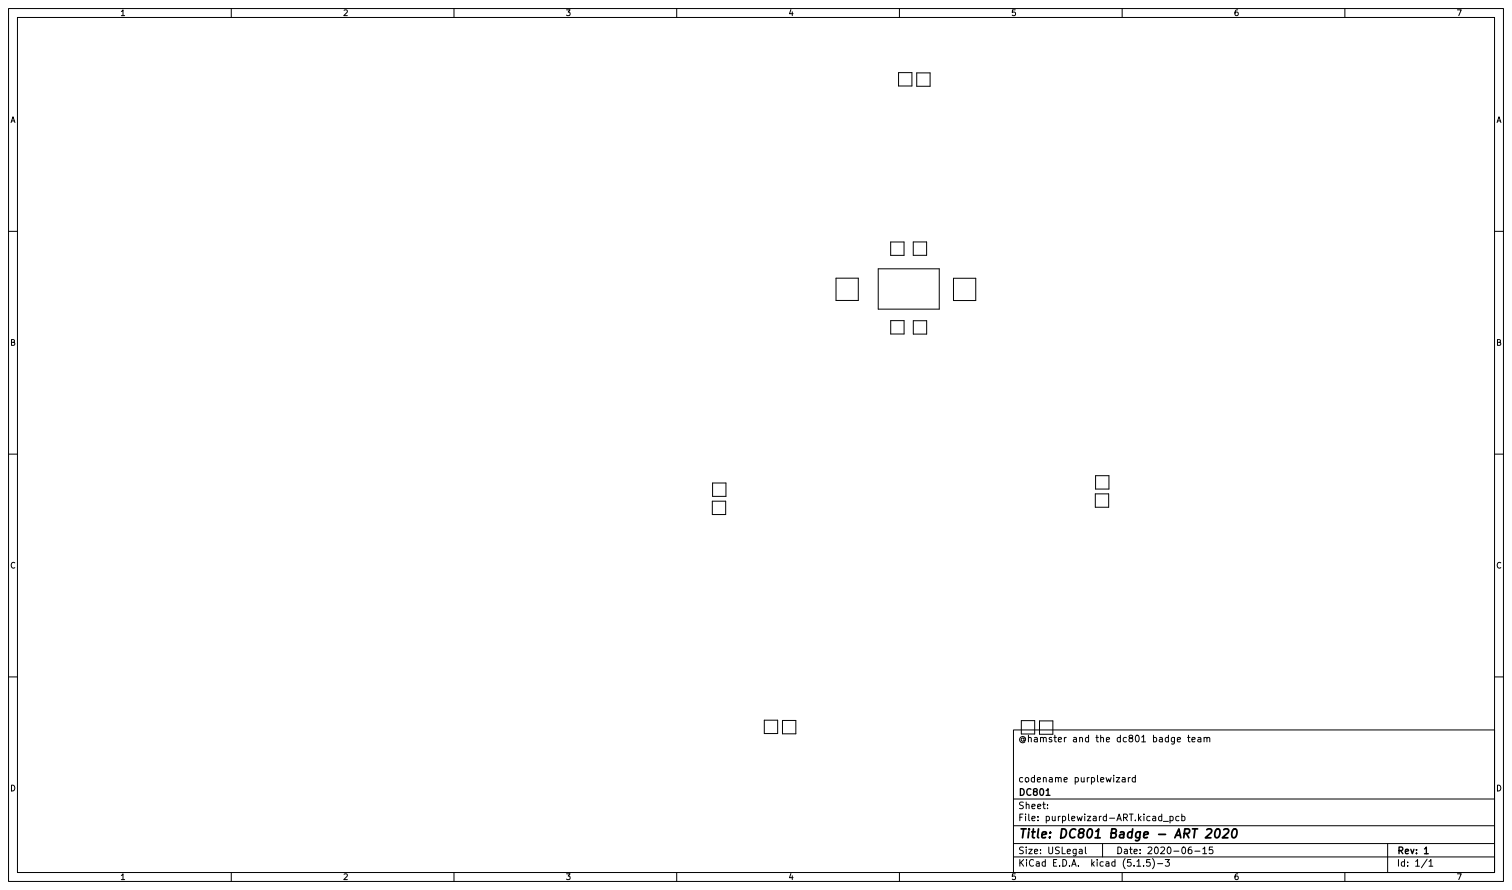
[picture p176: page 2]

@hamster and the dc801 badge team

codename purplewizard
D Date: 2020-06-15 KiCad E.D.A. kicad (5.1.5)-3
File: purplewizard-ART.kicad_pcb Sheet: DC801

Id: 1/1 Title: DC801 Badge - ART 2020

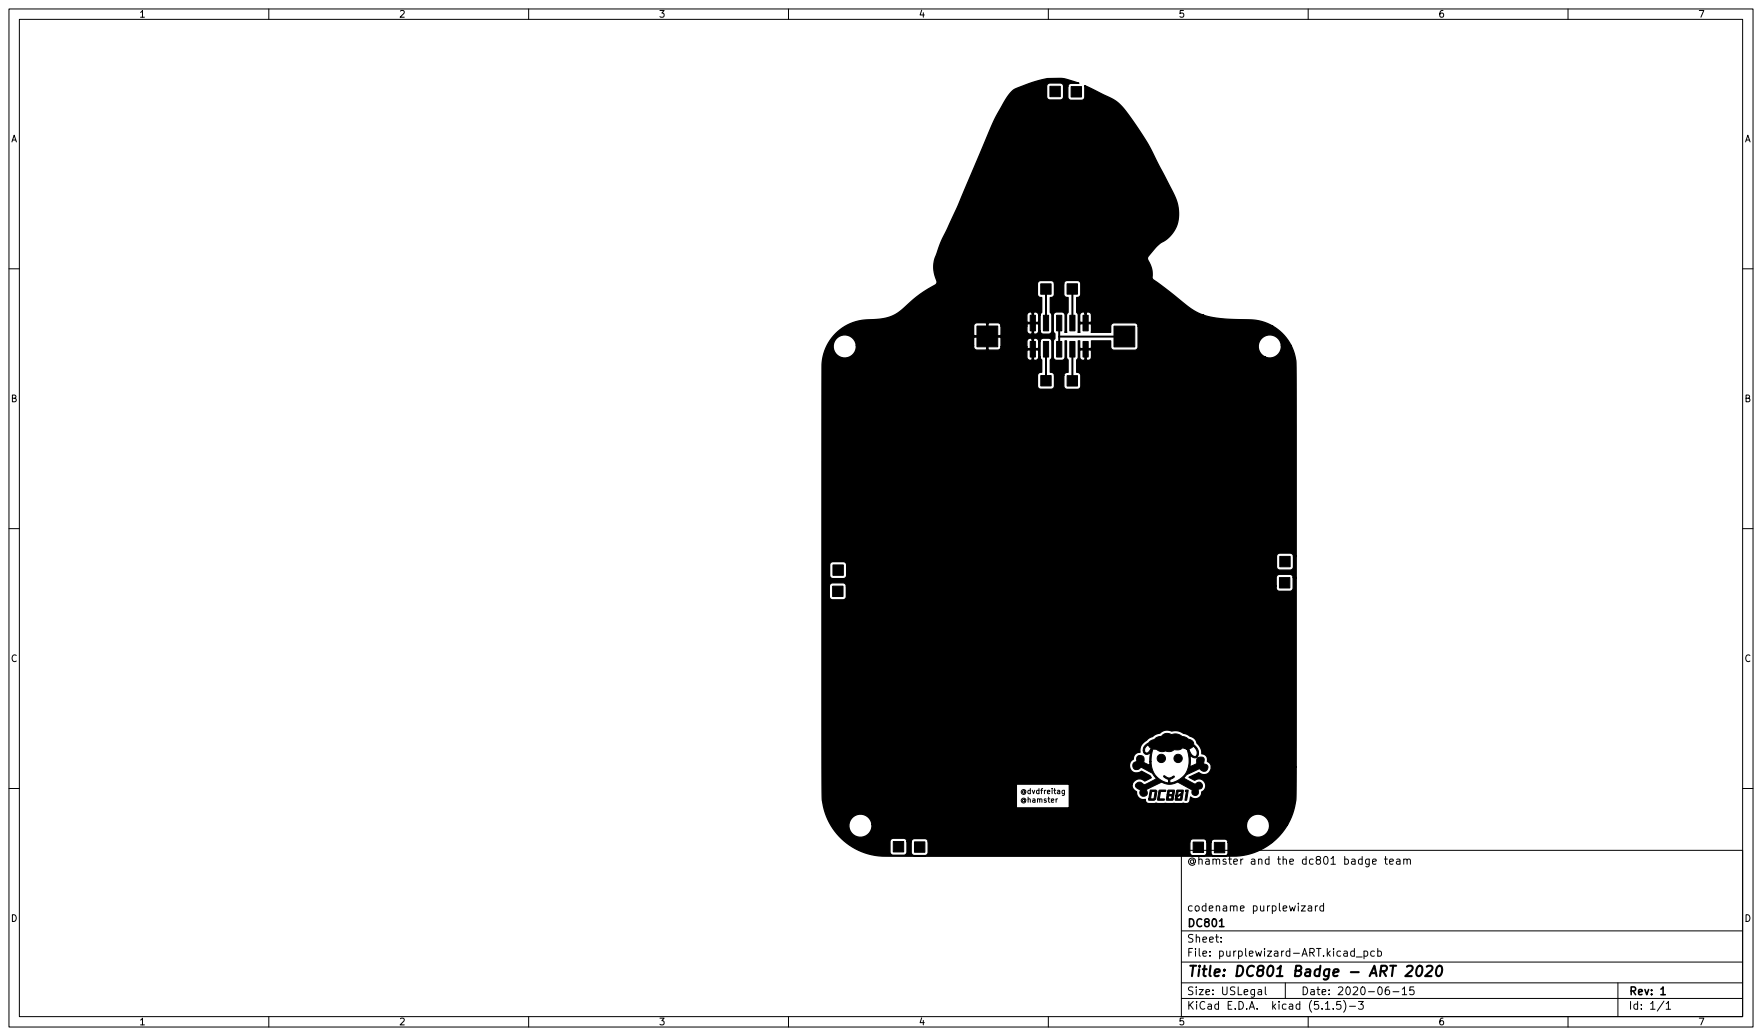
[picture p177: page 3]

@hamster and the dc801 badge team

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

Id: 1/1 Title: DC801 Badge - ART 2020


codename purplewizard
File: purplewizard-ART.kicad_pcb Sheet: DC801

Id: 1/1 Title: DC801 Badge - ART 2020

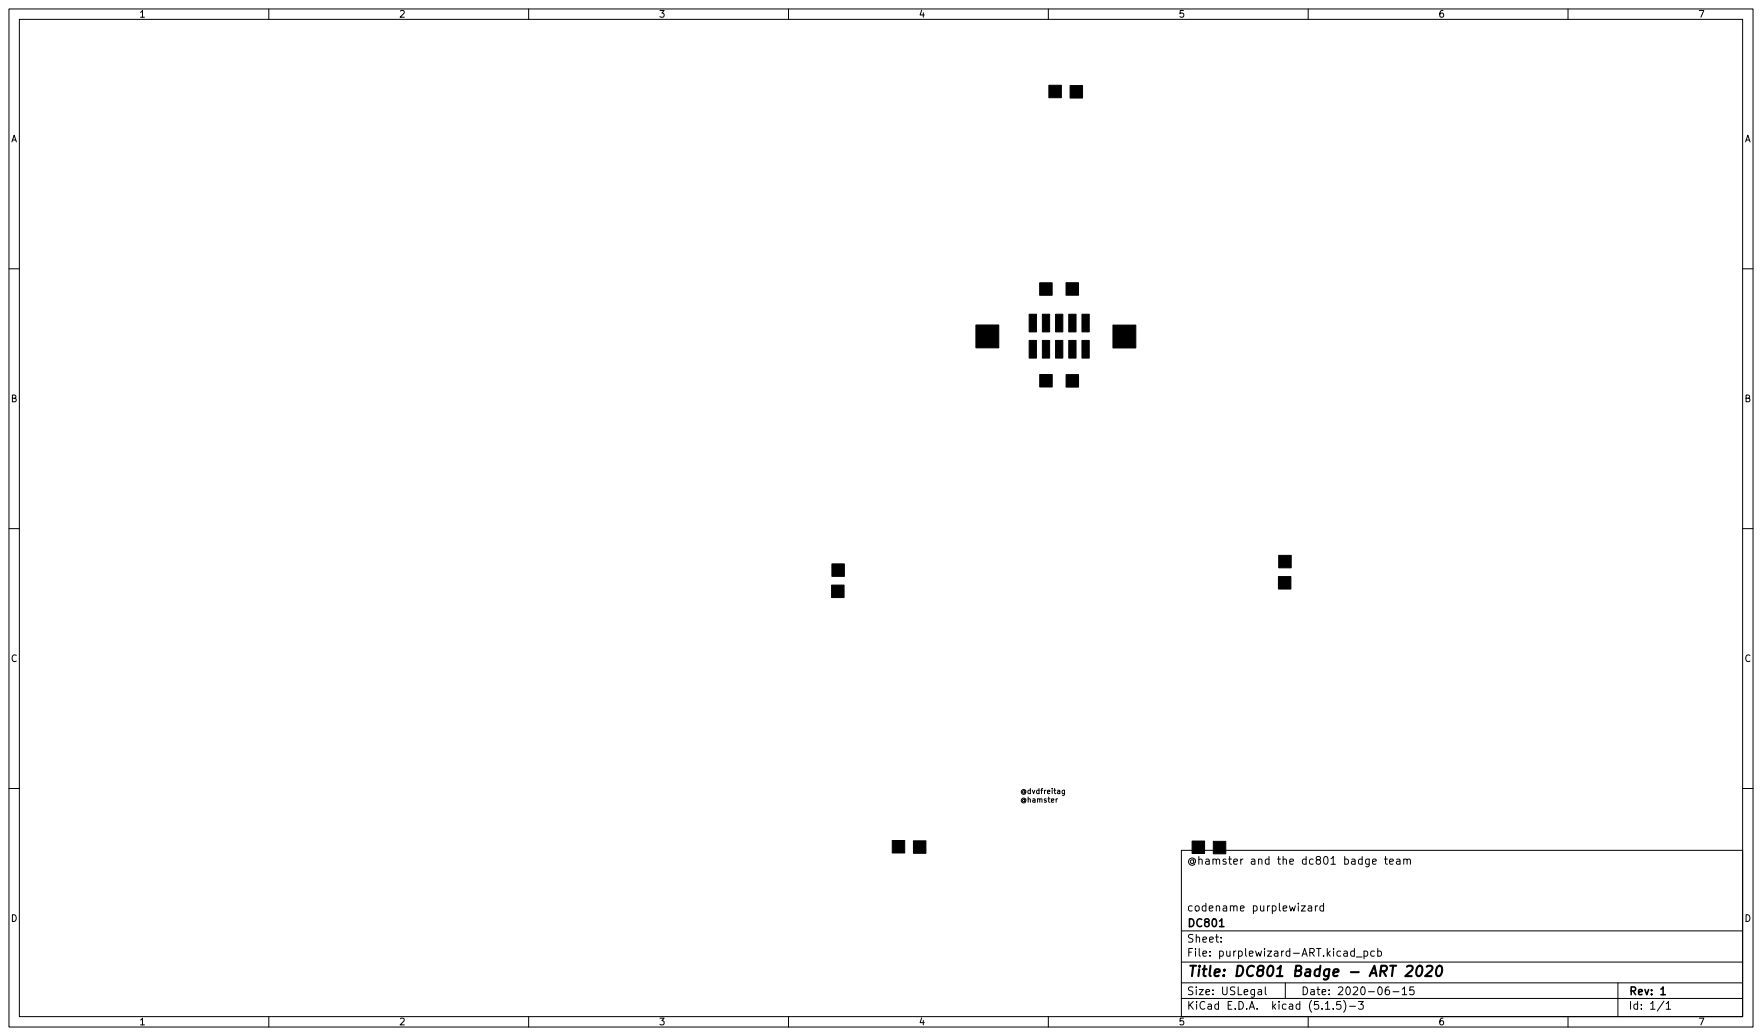
[picture p178: page 5]

@hamster and the dc801 badge team

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

Id: 1/1 Title: DC801 Badge - ART 2020


@hamster and the dc801 badge team

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

Id: 1/1 Title: DC801 Badge - ART 2020

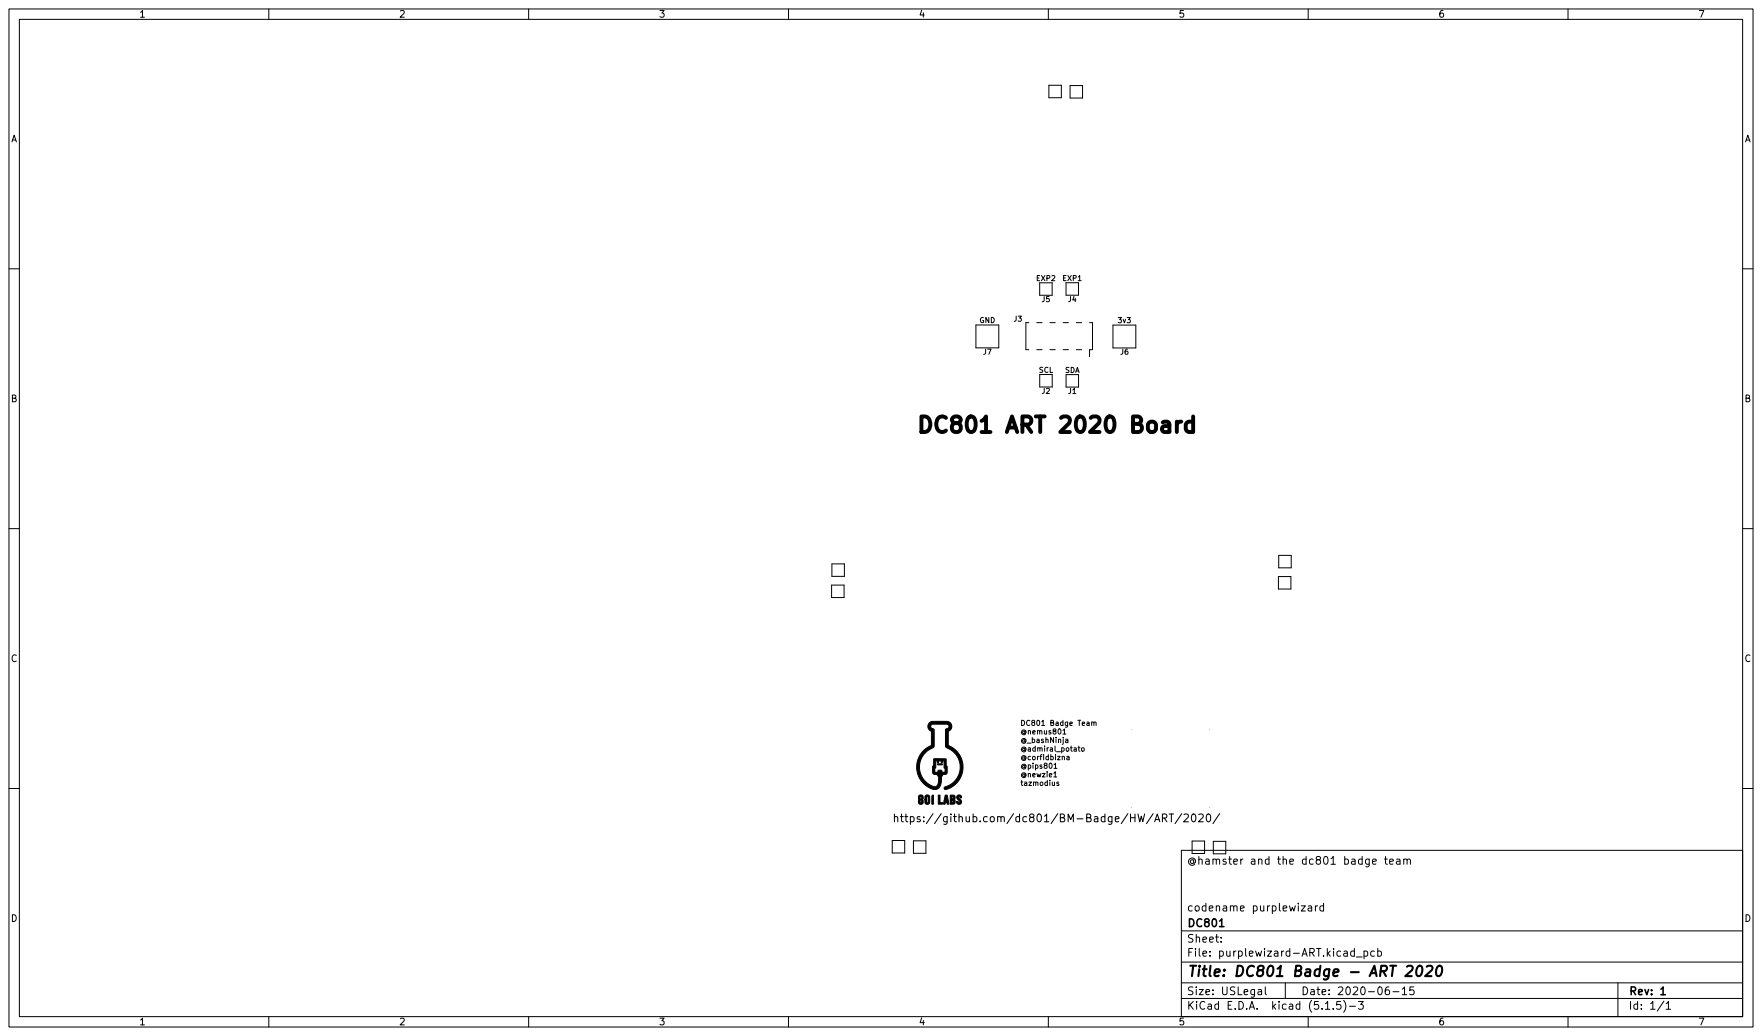
[picture p179: page 7]

https://github.com/dc801/BM-Badge/HW/ART/2020/ DC801 Badge Team @nemus801 @_bashNinja @admiral_potato @corfidbizna @pips801 @newzie1

@hamster and the dc801 badge team

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

Id: 1/1 Title: DC801 Badge - ART 2020

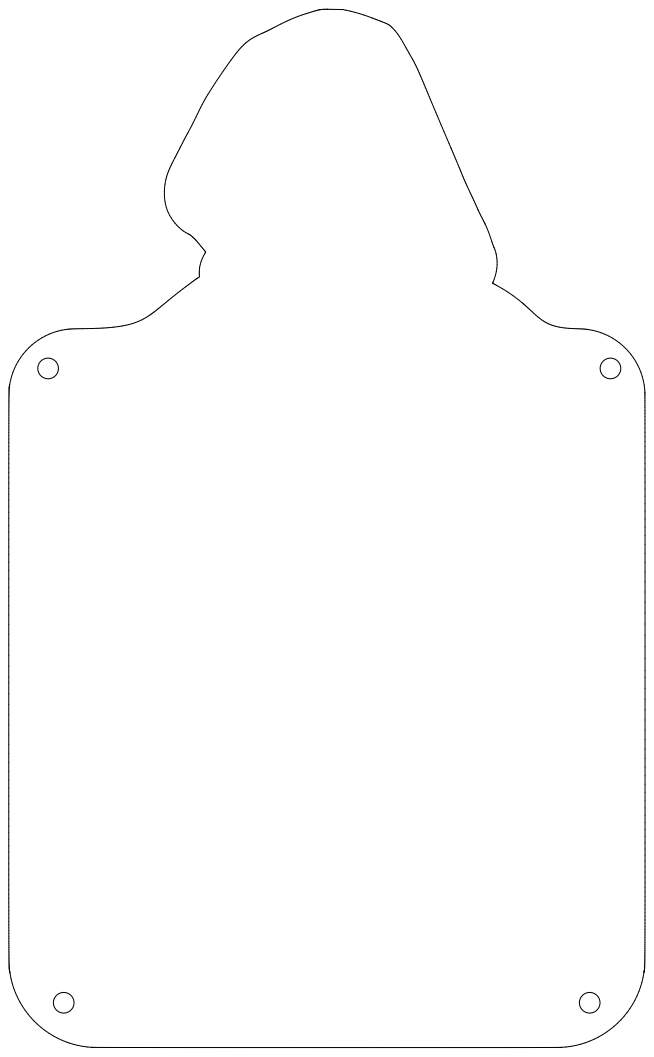
[picture p180: page 8]

@hamster and the dc801 badge team

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

Id: 1/1 Title: DC801 Badge - ART 2020

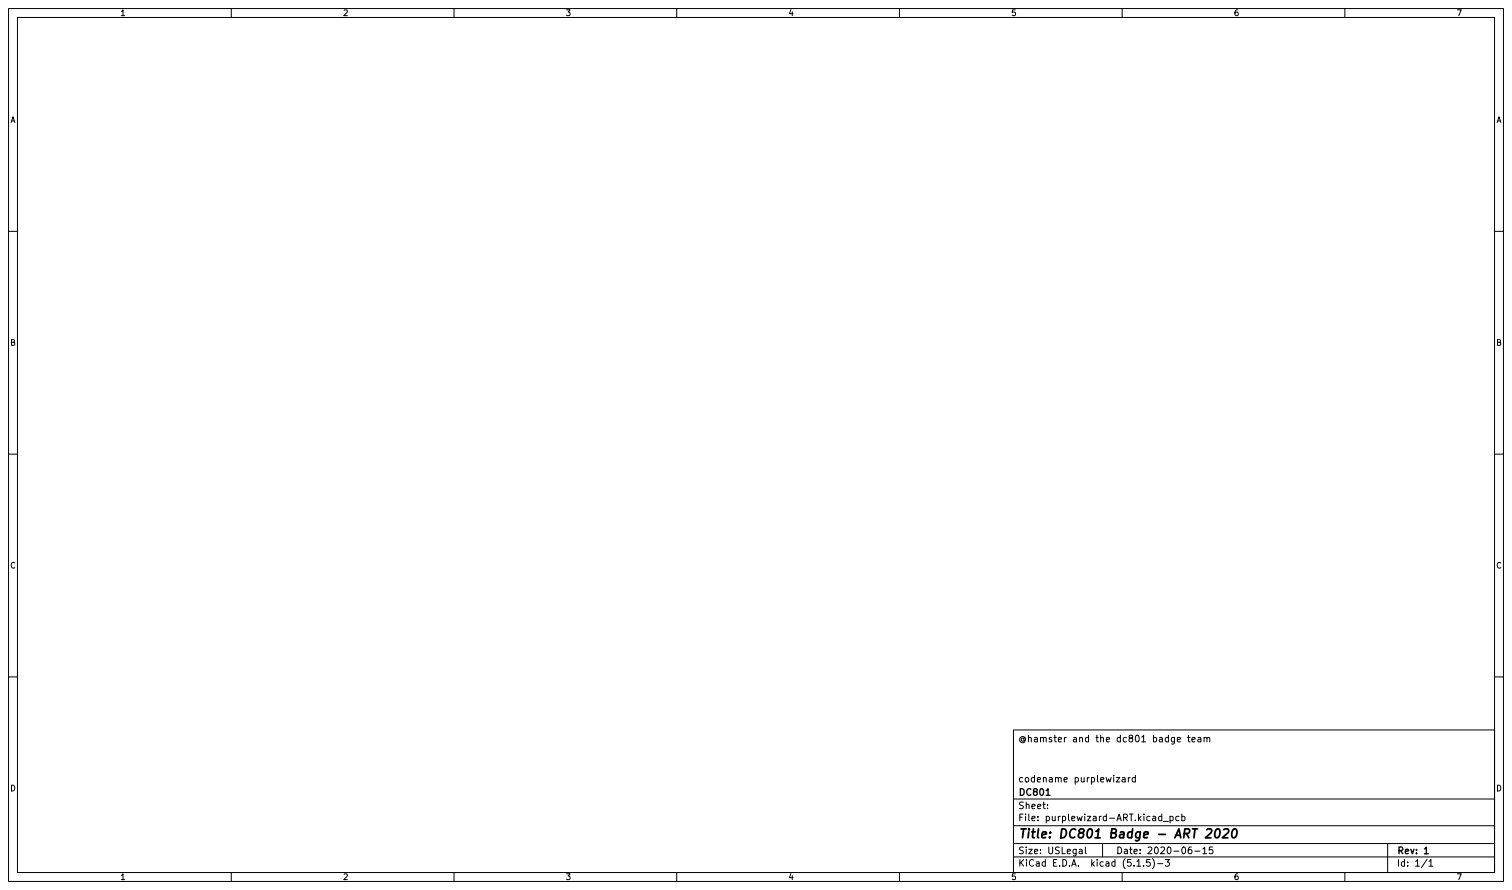
[picture p181: page 9]

@hamster and the dc801 badge team

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

Id: 1/1 Title: DC801 Badge - ART 2020


@hamster and the dc801 badge team

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

Id: 1/1 Title: DC801 Badge - ART 2020

@hamster and the dc801 badge team

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

Id: 1/1 Title: DC801 Badge - ART 2020


@hamster and the dc801 badge team

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

Id: 1/1 Title: DC801 Badge - ART 2020

@hamster and the dc801 badge team

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

Id: 1/1 Title: DC801 Badge - ART 2020

@hamster and the dc801 badge team

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

Id: 1/1 Title: DC801 Badge - ART 2020

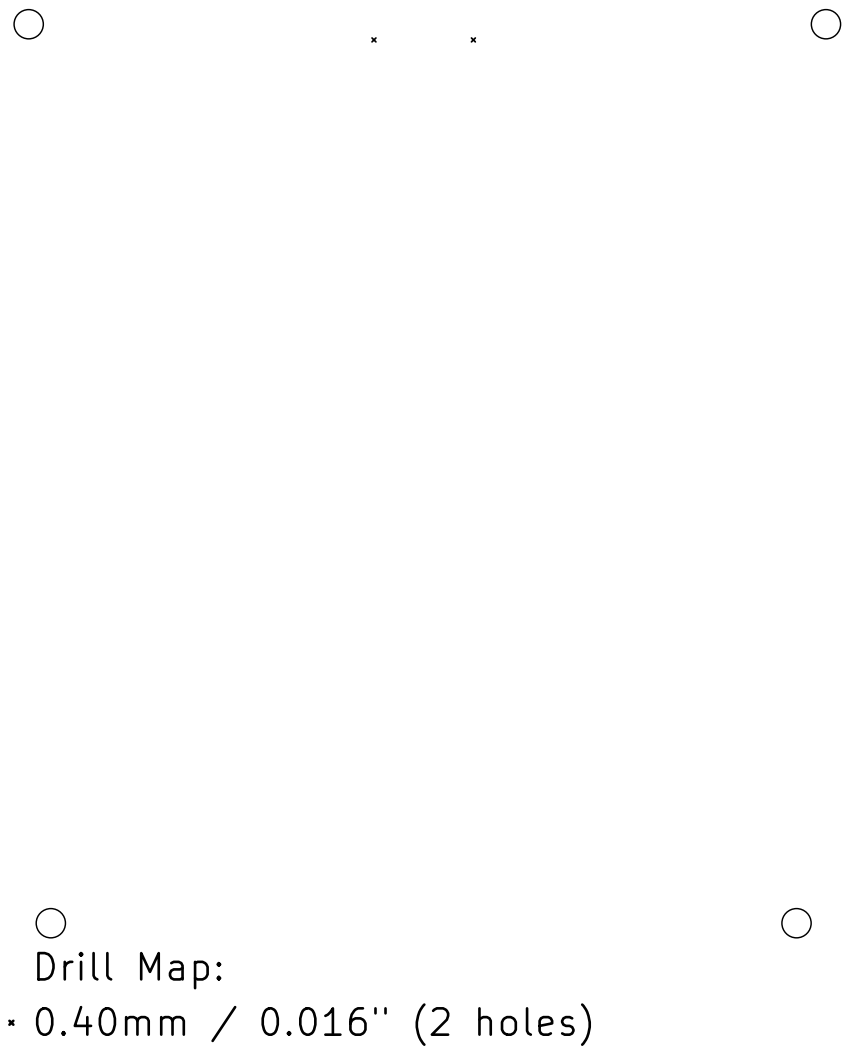
[picture p182: page 15]
