DC801/BM-Badge/Hardware/BackBoard/outputs/Final-1.1/purplewizard-B_Fab.pdf

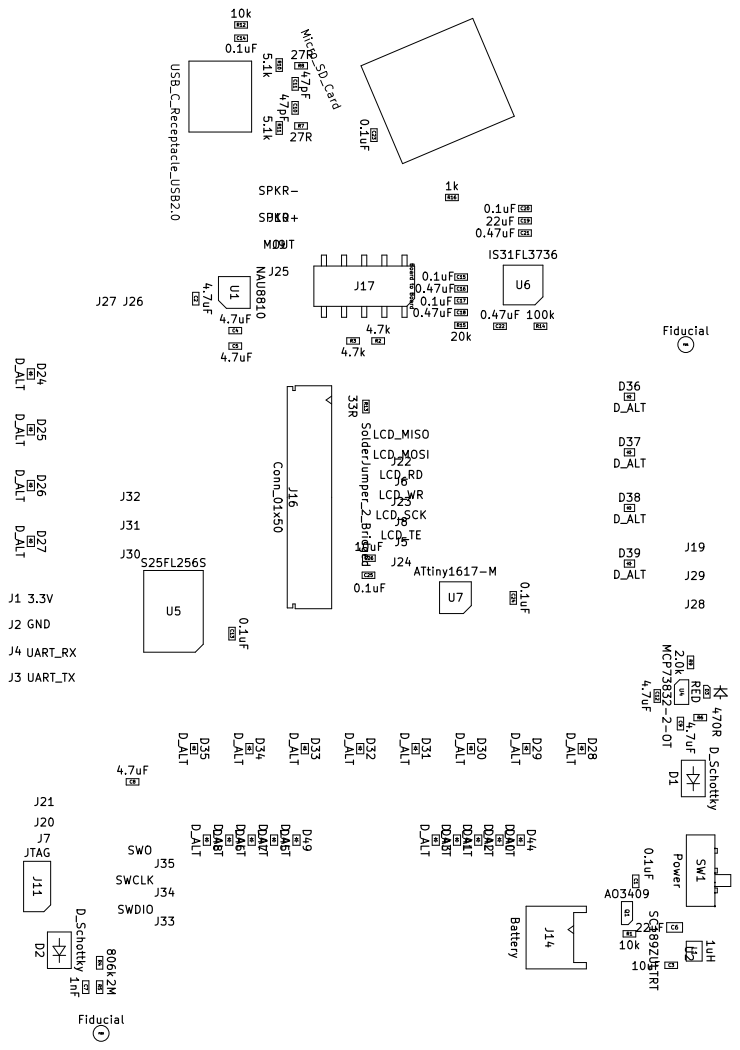
[picture p185: page 1]

Id: 1/1 Title: DC801 Badge - BM
