DC801/BM-Badge/Hardware/BackBoard/outputs/Final-1.1/purplewizard-B_Paste.pdf

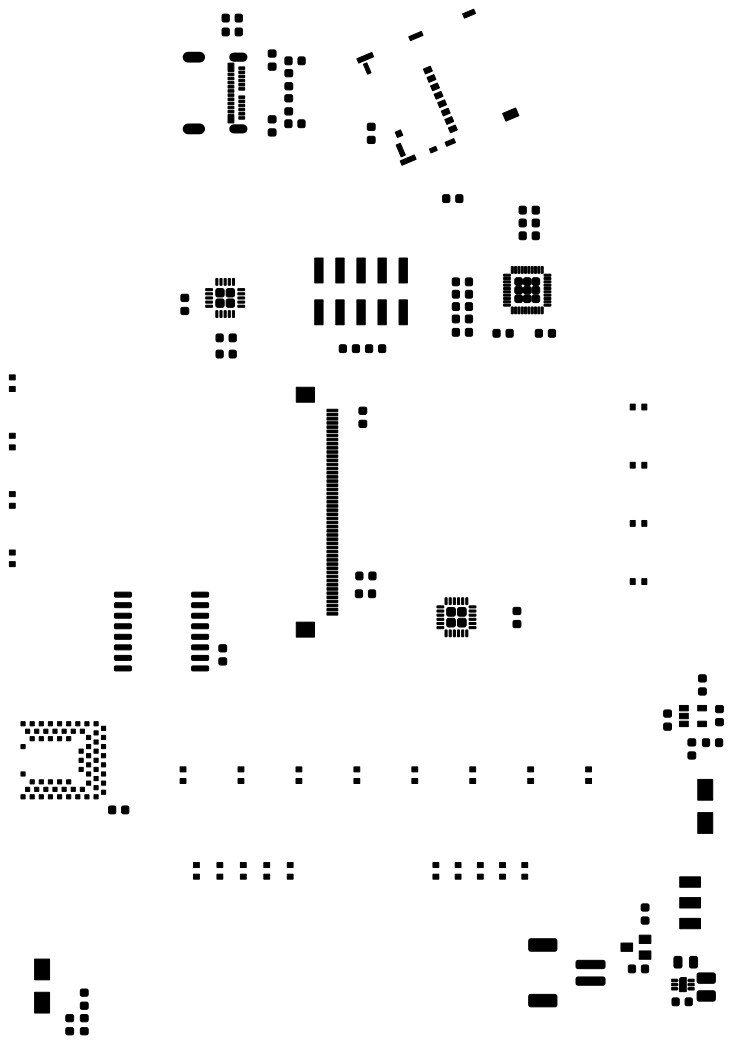
[picture p187: page 1]

@hamster and the dc801 badge team

Id: 1/1 Title: DC801 Badge - BM
