DC801/BM-Badge/Hardware/BackBoard/outputs/Final-1.1/purplewizard-B_Silkscreen.pdf

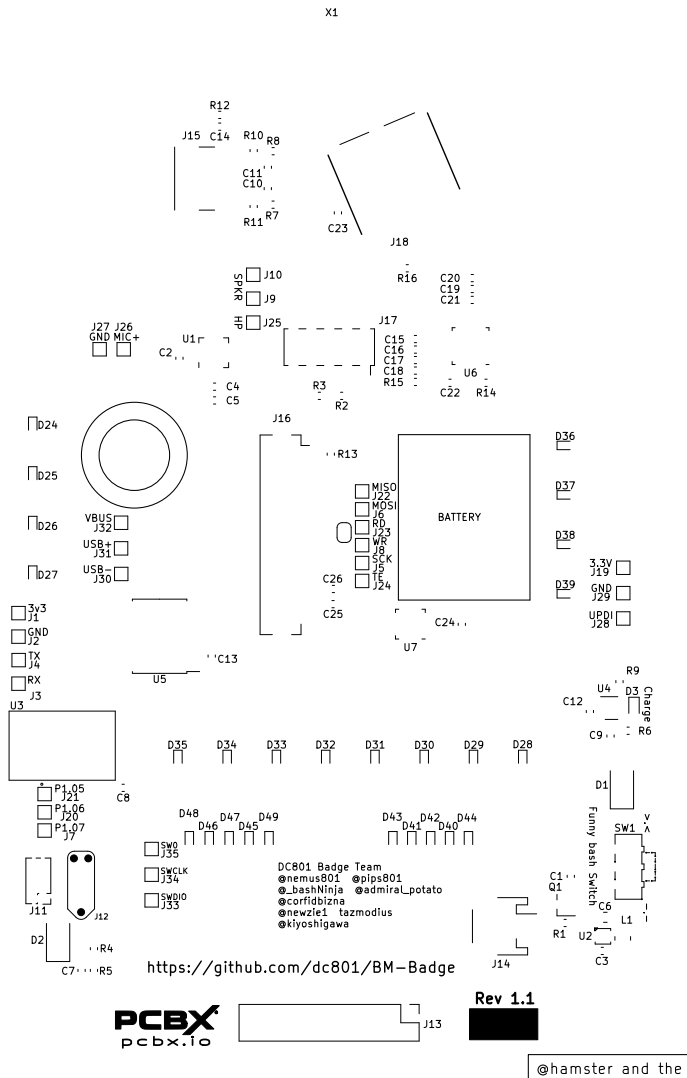
[picture p188: page 1]

Id: 1/1 Title: DC801 Badge - BM
