DC801/BM-Badge/Hardware/BackBoard/outputs/Final-1.1/purplewizard-F_Silkscreen.pdf

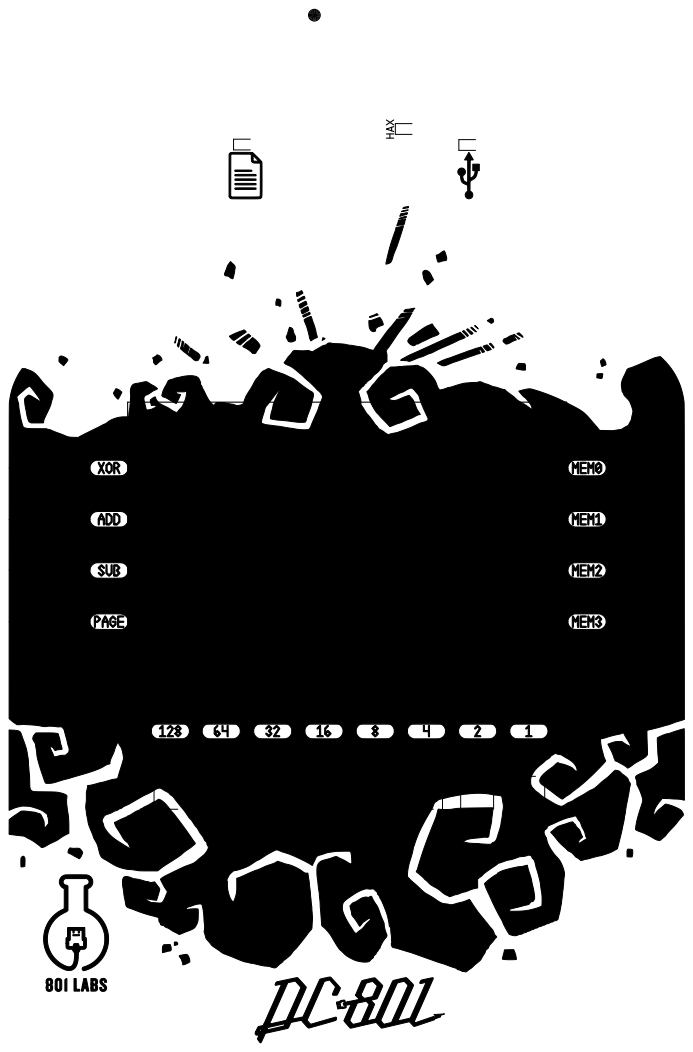
[picture p194: page 1]

@hamster and the dc801 badge team HAX

Id: 1/1 Title: DC801 Badge - BM
