DC801/BM-Badge/Hardware/BackBoard/outputs/Final-1.0/purplewizard-B_Fab.pdf

@hamster and the dc801 badge team Micro_SD_Card

Id: 1/1 Title: DC801 Badge - BM
