DC801/BM-Badge/Hardware/BackBoard/outputs/Final-1.0/purplewizard-B_SilkS.pdf

@hamster and the dc801 badge team

Id: 1/1 Title: DC801 Badge - BM
