DC801/BM-Badge/Hardware/BackBoard/outputs/Proto1/purplewizard-B_Paste.pdf

@hamster and the dc801 badge team

Id: 1/1 Title: DC801 Badge - BM
