DC801/BM-Badge/Hardware/BackBoard/outputs/Proto1/purplewizard-F_SilkS.pdf

@hamster and the dc801 badge team HAX

Id: 1/1 Title: DC801 Badge - BM
