DC801/BM-Badge/HW/BackBoard/outputs/Final/purplewizard-B_Cu.pdf

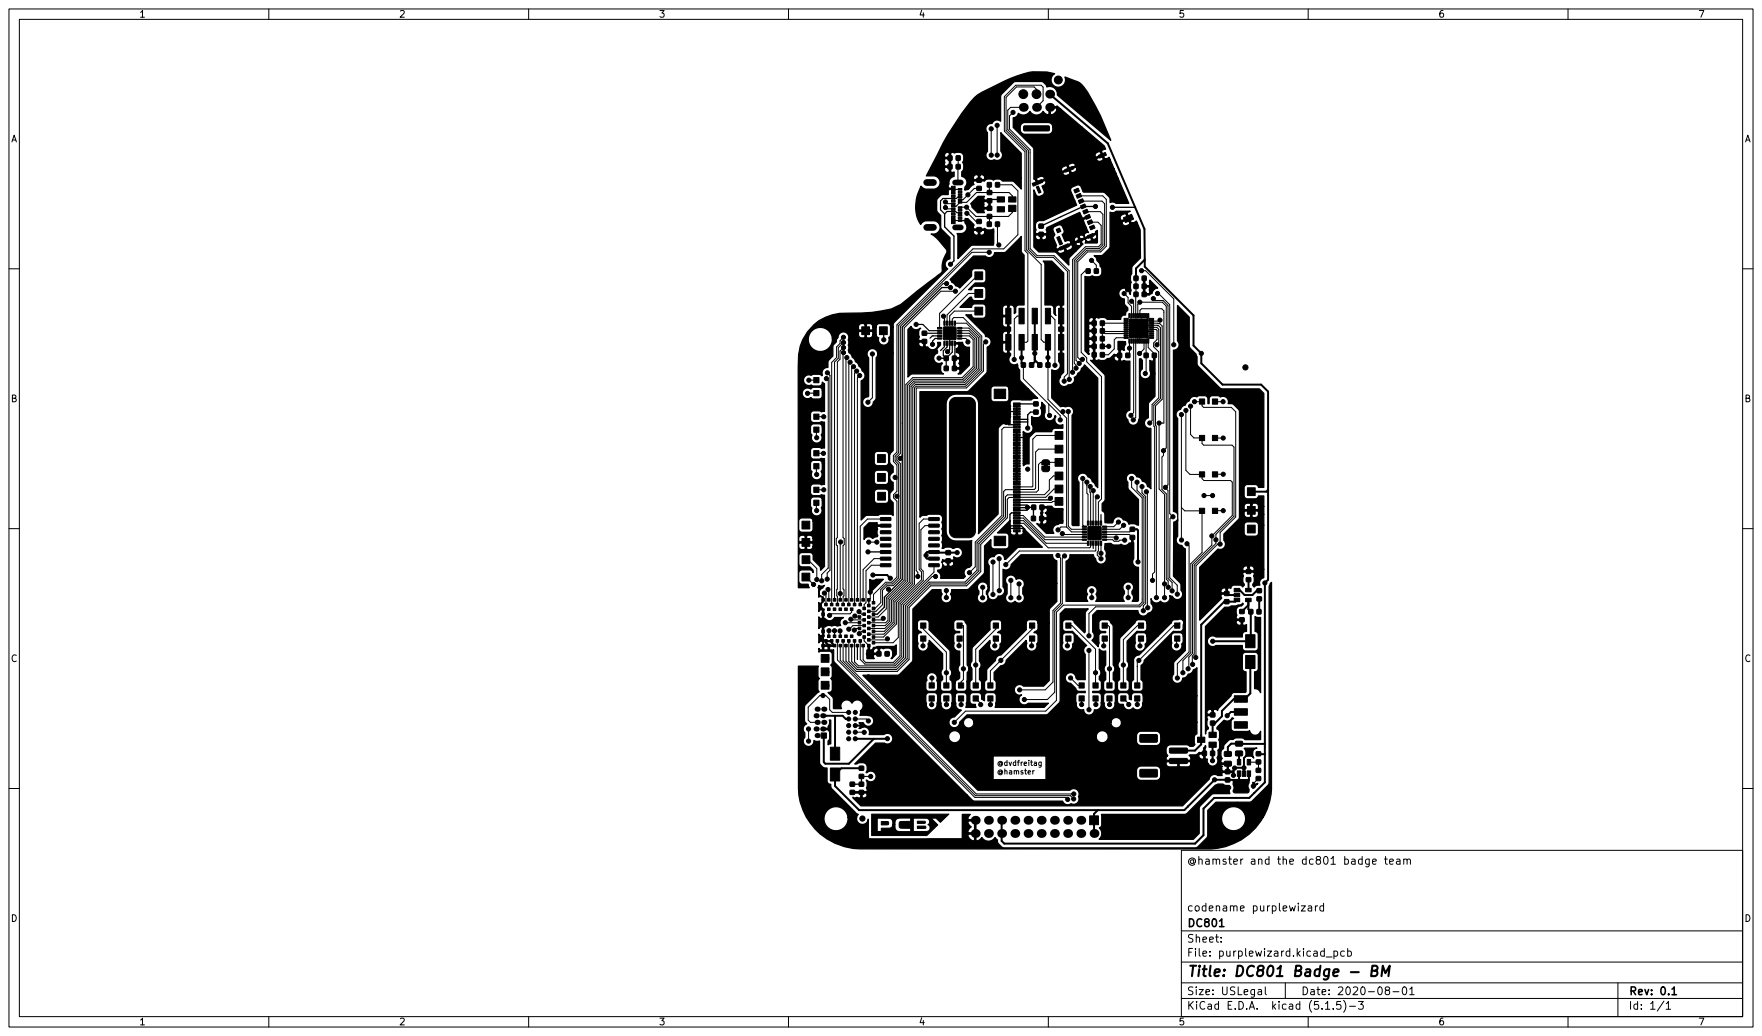
[picture p195: page 1]

@hamster and the dc801 badge team

Id: 1/1 Title: DC801 Badge - BM
