DC801/BM-Badge/HW/BackBoard/outputs/Final/purplewizard-B_Fab.pdf

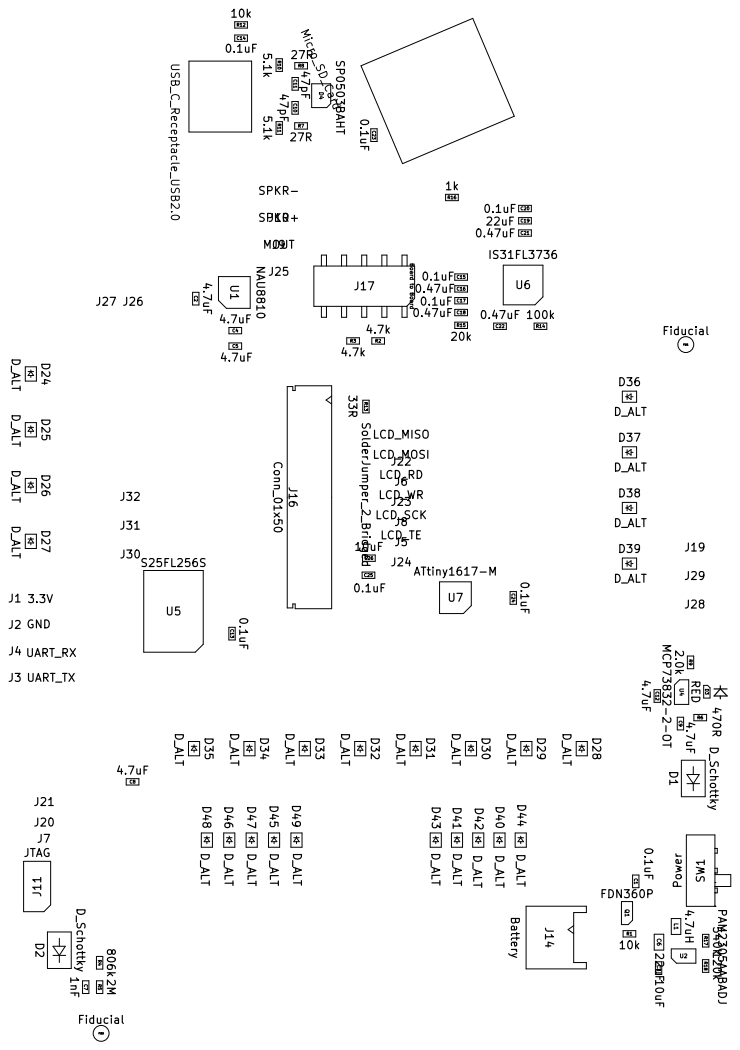
[picture p196: page 1]

@hamster and the dc801 badge team Micro_SD_Card

Id: 1/1 Title: DC801 Badge - BM
