DC801/BM-Badge/HW/BackBoard/outputs/Final/purplewizard-B_Mask.pdf

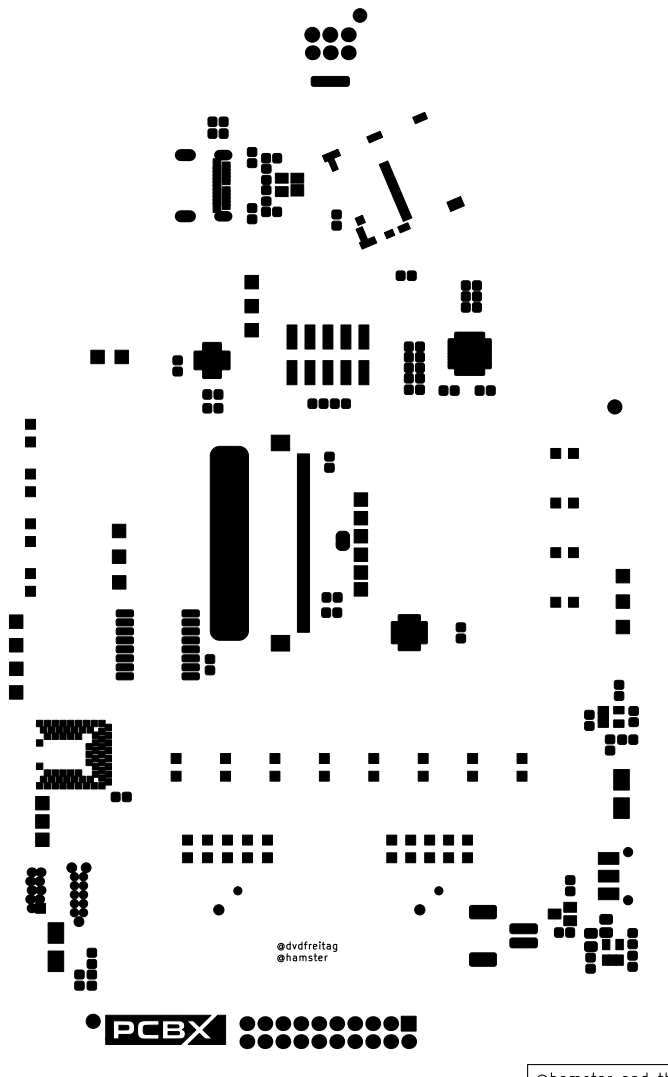
[picture p197: page 1]

@hamster and the dc801 badge team

Id: 1/1 Title: DC801 Badge - BM
