DC801/BM-Badge/Software/Keyboard/KeyboardController/include/atmel_start_pins.h

/*
 * Code generated from START.
 *
 * This file will be overwritten when reconfiguring your START project.
 * Please copy examples or other code you want to keep to a separate file
 * to avoid losing it when reconfiguring.
 */
#ifndef ATMEL_START_PINS_H_INCLUDED
#define ATMEL_START_PINS_H_INCLUDED

#include <port.h>

/**
 * \brief Set R4 pull mode
 *
 * Configure pin to pull up, down or disable pull mode, supported pull
 * modes are defined by device used
 *
 * \param[in] pull_mode Pin pull mode
 */
static inline void R4_set_pull_mode(const enum port_pull_mode pull_mode)
{
	PORTA_set_pin_pull_mode(1, pull_mode);
}

/**
 * \brief Set R4 data direction
 *
 * Select if the pin data direction is input, output or disabled.
 * If disabled state is not possible, this function throws an assert.
 *
 * \param[in] direction PORT_DIR_IN  = Data direction in
 *                      PORT_DIR_OUT = Data direction out
 *                      PORT_DIR_OFF = Disables the pin
 *                      (low power state)
 */
static inline void R4_set_dir(const enum port_dir dir)
{
	PORTA_set_pin_dir(1, dir);
}

/**
 * \brief Set R4 input/sense configuration
 *
 * Enable/disable R4 digital input buffer and pin change interrupt,
 * select pin interrupt edge/level sensing mode
 *
 * \param[in] isc PORT_ISC_INTDISABLE_gc    = Iterrupt disabled but input buffer enabled
 *                PORT_ISC_BOTHEDGES_gc     = Sense Both Edges
 *                PORT_ISC_RISING_gc        = Sense Rising Edge
 *                PORT_ISC_FALLING_gc       = Sense Falling Edge
 *                PORT_ISC_INPUT_DISABLE_gc = Digital Input Buffer disabled
 *                PORT_ISC_LEVEL_gc         = Sense low Level
 */
static inline void R4_set_isc(const PORT_ISC_t isc)
{
	PORTA_pin_set_isc(1, isc);
}

/**
 * \brief Set R4 inverted mode
 *
 * Enable or disable inverted I/O on a pin
 *
 * \param[in] inverted true  = I/O on R4 is inverted
 *                     false = I/O on R4 is not inverted
 */
static inline void R4_set_inverted(const bool inverted)
{
	PORTA_pin_set_inverted(1, inverted);
}

/**
 * \brief Set R4 level
 *
 * Sets output level on a pin
 *
 * \param[in] level true  = Pin level set to "high" state
 *                  false = Pin level set to "low" state
 */
static inline void R4_set_level(const bool level)
{
	PORTA_set_pin_level(1, level);
}

/**
 * \brief Toggle output level on R4
 *
 * Toggle the pin level
 */
static inline void R4_toggle_level()
{
	PORTA_toggle_pin_level(1);
}

/**
 * \brief Get level on R4
 *
 * Reads the level on a pin
 */
static inline bool R4_get_level()
{
	return PORTA_get_pin_level(1);
}

/**
 * \brief Set R3 pull mode
 *
 * Configure pin to pull up, down or disable pull mode, supported pull
 * modes are defined by device used
 *
 * \param[in] pull_mode Pin pull mode
 */
static inline void R3_set_pull_mode(const enum port_pull_mode pull_mode)
{
	PORTA_set_pin_pull_mode(2, pull_mode);
}

/**
 * \brief Set R3 data direction
 *
 * Select if the pin data direction is input, output or disabled.
 * If disabled state is not possible, this function throws an assert.
 *
 * \param[in] direction PORT_DIR_IN  = Data direction in
 *                      PORT_DIR_OUT = Data direction out
 *                      PORT_DIR_OFF = Disables the pin
 *                      (low power state)
 */
static inline void R3_set_dir(const enum port_dir dir)
{
	PORTA_set_pin_dir(2, dir);
}

/**
 * \brief Set R3 input/sense configuration
 *
 * Enable/disable R3 digital input buffer and pin change interrupt,
 * select pin interrupt edge/level sensing mode
 *
 * \param[in] isc PORT_ISC_INTDISABLE_gc    = Iterrupt disabled but input buffer enabled
 *                PORT_ISC_BOTHEDGES_gc     = Sense Both Edges
 *                PORT_ISC_RISING_gc        = Sense Rising Edge
 *                PORT_ISC_FALLING_gc       = Sense Falling Edge
 *                PORT_ISC_INPUT_DISABLE_gc = Digital Input Buffer disabled
 *                PORT_ISC_LEVEL_gc         = Sense low Level
 */
static inline void R3_set_isc(const PORT_ISC_t isc)
{
	PORTA_pin_set_isc(2, isc);
}

/**
 * \brief Set R3 inverted mode
 *
 * Enable or disable inverted I/O on a pin
 *
 * \param[in] inverted true  = I/O on R3 is inverted
 *                     false = I/O on R3 is not inverted
 */
static inline void R3_set_inverted(const bool inverted)
{
	PORTA_pin_set_inverted(2, inverted);
}

/**
 * \brief Set R3 level
 *
 * Sets output level on a pin
 *
 * \param[in] level true  = Pin level set to "high" state
 *                  false = Pin level set to "low" state
 */
static inline void R3_set_level(const bool level)
{
	PORTA_set_pin_level(2, level);
}

/**
 * \brief Toggle output level on R3
 *
 * Toggle the pin level
 */
static inline void R3_toggle_level()
{
	PORTA_toggle_pin_level(2);
}

/**
 * \brief Get level on R3
 *
 * Reads the level on a pin
 */
static inline bool R3_get_level()
{
	return PORTA_get_pin_level(2);
}

/**
 * \brief Set R2 pull mode
 *
 * Configure pin to pull up, down or disable pull mode, supported pull
 * modes are defined by device used
 *
 * \param[in] pull_mode Pin pull mode
 */
static inline void R2_set_pull_mode(const enum port_pull_mode pull_mode)
{
	PORTA_set_pin_pull_mode(3, pull_mode);
}

/**
 * \brief Set R2 data direction
 *
 * Select if the pin data direction is input, output or disabled.
 * If disabled state is not possible, this function throws an assert.
 *
 * \param[in] direction PORT_DIR_IN  = Data direction in
 *                      PORT_DIR_OUT = Data direction out
 *                      PORT_DIR_OFF = Disables the pin
 *                      (low power state)
 */
static inline void R2_set_dir(const enum port_dir dir)
{
	PORTA_set_pin_dir(3, dir);
}

/**
 * \brief Set R2 input/sense configuration
 *
 * Enable/disable R2 digital input buffer and pin change interrupt,
 * select pin interrupt edge/level sensing mode
 *
 * \param[in] isc PORT_ISC_INTDISABLE_gc    = Iterrupt disabled but input buffer enabled
 *                PORT_ISC_BOTHEDGES_gc     = Sense Both Edges
 *                PORT_ISC_RISING_gc        = Sense Rising Edge
 *                PORT_ISC_FALLING_gc       = Sense Falling Edge
 *                PORT_ISC_INPUT_DISABLE_gc = Digital Input Buffer disabled
 *                PORT_ISC_LEVEL_gc         = Sense low Level
 */
static inline void R2_set_isc(const PORT_ISC_t isc)
{
	PORTA_pin_set_isc(3, isc);
}

/**
 * \brief Set R2 inverted mode
 *
 * Enable or disable inverted I/O on a pin
 *
 * \param[in] inverted true  = I/O on R2 is inverted
 *                     false = I/O on R2 is not inverted
 */
static inline void R2_set_inverted(const bool inverted)
{
	PORTA_pin_set_inverted(3, inverted);
}

/**
 * \brief Set R2 level
 *
 * Sets output level on a pin
 *
 * \param[in] level true  = Pin level set to "high" state
 *                  false = Pin level set to "low" state
 */
static inline void R2_set_level(const bool level)
{
	PORTA_set_pin_level(3, level);
}

/**
 * \brief Toggle output level on R2
 *
 * Toggle the pin level
 */
static inline void R2_toggle_level()
{
	PORTA_toggle_pin_level(3);
}

/**
 * \brief Get level on R2
 *
 * Reads the level on a pin
 */
static inline bool R2_get_level()
{
	return PORTA_get_pin_level(3);
}

/**
 * \brief Set R1 pull mode
 *
 * Configure pin to pull up, down or disable pull mode, supported pull
 * modes are defined by device used
 *
 * \param[in] pull_mode Pin pull mode
 */
static inline void R1_set_pull_mode(const enum port_pull_mode pull_mode)
{
	PORTA_set_pin_pull_mode(4, pull_mode);
}

/**
 * \brief Set R1 data direction
 *
 * Select if the pin data direction is input, output or disabled.
 * If disabled state is not possible, this function throws an assert.
 *
 * \param[in] direction PORT_DIR_IN  = Data direction in
 *                      PORT_DIR_OUT = Data direction out
 *                      PORT_DIR_OFF = Disables the pin
 *                      (low power state)
 */
static inline void R1_set_dir(const enum port_dir dir)
{
	PORTA_set_pin_dir(4, dir);
}

/**
 * \brief Set R1 input/sense configuration
 *
 * Enable/disable R1 digital input buffer and pin change interrupt,
 * select pin interrupt edge/level sensing mode
 *
 * \param[in] isc PORT_ISC_INTDISABLE_gc    = Iterrupt disabled but input buffer enabled
 *                PORT_ISC_BOTHEDGES_gc     = Sense Both Edges
 *                PORT_ISC_RISING_gc        = Sense Rising Edge
 *                PORT_ISC_FALLING_gc       = Sense Falling Edge
 *                PORT_ISC_INPUT_DISABLE_gc = Digital Input Buffer disabled
 *                PORT_ISC_LEVEL_gc         = Sense low Level
 */
static inline void R1_set_isc(const PORT_ISC_t isc)
{
	PORTA_pin_set_isc(4, isc);
}

/**
 * \brief Set R1 inverted mode
 *
 * Enable or disable inverted I/O on a pin
 *
 * \param[in] inverted true  = I/O on R1 is inverted
 *                     false = I/O on R1 is not inverted
 */
static inline void R1_set_inverted(const bool inverted)
{
	PORTA_pin_set_inverted(4, inverted);
}

/**
 * \brief Set R1 level
 *
 * Sets output level on a pin
 *
 * \param[in] level true  = Pin level set to "high" state
 *                  false = Pin level set to "low" state
 */
static inline void R1_set_level(const bool level)
{
	PORTA_set_pin_level(4, level);
}

/**
 * \brief Toggle output level on R1
 *
 * Toggle the pin level
 */
static inline void R1_toggle_level()
{
	PORTA_toggle_pin_level(4);
}

/**
 * \brief Get level on R1
 *
 * Reads the level on a pin
 */
static inline bool R1_get_level()
{
	return PORTA_get_pin_level(4);
}

/**
 * \brief Set R0 pull mode
 *
 * Configure pin to pull up, down or disable pull mode, supported pull
 * modes are defined by device used
 *
 * \param[in] pull_mode Pin pull mode
 */
static inline void R0_set_pull_mode(const enum port_pull_mode pull_mode)
{
	PORTA_set_pin_pull_mode(5, pull_mode);
}

/**
 * \brief Set R0 data direction
 *
 * Select if the pin data direction is input, output or disabled.
 * If disabled state is not possible, this function throws an assert.
 *
 * \param[in] direction PORT_DIR_IN  = Data direction in
 *                      PORT_DIR_OUT = Data direction out
 *                      PORT_DIR_OFF = Disables the pin
 *                      (low power state)
 */
static inline void R0_set_dir(const enum port_dir dir)
{
	PORTA_set_pin_dir(5, dir);
}

/**
 * \brief Set R0 input/sense configuration
 *
 * Enable/disable R0 digital input buffer and pin change interrupt,
 * select pin interrupt edge/level sensing mode
 *
 * \param[in] isc PORT_ISC_INTDISABLE_gc    = Iterrupt disabled but input buffer enabled
 *                PORT_ISC_BOTHEDGES_gc     = Sense Both Edges
 *                PORT_ISC_RISING_gc        = Sense Rising Edge
 *                PORT_ISC_FALLING_gc       = Sense Falling Edge
 *                PORT_ISC_INPUT_DISABLE_gc = Digital Input Buffer disabled
 *                PORT_ISC_LEVEL_gc         = Sense low Level
 */
static inline void R0_set_isc(const PORT_ISC_t isc)
{
	PORTA_pin_set_isc(5, isc);
}

/**
 * \brief Set R0 inverted mode
 *
 * Enable or disable inverted I/O on a pin
 *
 * \param[in] inverted true  = I/O on R0 is inverted
 *                     false = I/O on R0 is not inverted
 */
static inline void R0_set_inverted(const bool inverted)
{
	PORTA_pin_set_inverted(5, inverted);
}

/**
 * \brief Set R0 level
 *
 * Sets output level on a pin
 *
 * \param[in] level true  = Pin level set to "high" state
 *                  false = Pin level set to "low" state
 */
static inline void R0_set_level(const bool level)
{
	PORTA_set_pin_level(5, level);
}

/**
 * \brief Toggle output level on R0
 *
 * Toggle the pin level
 */
static inline void R0_toggle_level()
{
	PORTA_toggle_pin_level(5);
}

/**
 * \brief Get level on R0
 *
 * Reads the level on a pin
 */
static inline bool R0_get_level()
{
	return PORTA_get_pin_level(5);
}

/**
 * \brief Set HAX pull mode
 *
 * Configure pin to pull up, down or disable pull mode, supported pull
 * modes are defined by device used
 *
 * \param[in] pull_mode Pin pull mode
 */
static inline void HAX_set_pull_mode(const enum port_pull_mode pull_mode)
{
	PORTA_set_pin_pull_mode(7, pull_mode);
}

/**
 * \brief Set HAX data direction
 *
 * Select if the pin data direction is input, output or disabled.
 * If disabled state is not possible, this function throws an assert.
 *
 * \param[in] direction PORT_DIR_IN  = Data direction in
 *                      PORT_DIR_OUT = Data direction out
 *                      PORT_DIR_OFF = Disables the pin
 *                      (low power state)
 */
static inline void HAX_set_dir(const enum port_dir dir)
{
	PORTA_set_pin_dir(7, dir);
}

/**
 * \brief Set HAX input/sense configuration
 *
 * Enable/disable HAX digital input buffer and pin change interrupt,
 * select pin interrupt edge/level sensing mode
 *
 * \param[in] isc PORT_ISC_INTDISABLE_gc    = Iterrupt disabled but input buffer enabled
 *                PORT_ISC_BOTHEDGES_gc     = Sense Both Edges
 *                PORT_ISC_RISING_gc        = Sense Rising Edge
 *                PORT_ISC_FALLING_gc       = Sense Falling Edge
 *                PORT_ISC_INPUT_DISABLE_gc = Digital Input Buffer disabled
 *                PORT_ISC_LEVEL_gc         = Sense low Level
 */
static inline void HAX_set_isc(const PORT_ISC_t isc)
{
	PORTA_pin_set_isc(7, isc);
}

/**
 * \brief Set HAX inverted mode
 *
 * Enable or disable inverted I/O on a pin
 *
 * \param[in] inverted true  = I/O on HAX is inverted
 *                     false = I/O on HAX is not inverted
 */
static inline void HAX_set_inverted(const bool inverted)
{
	PORTA_pin_set_inverted(7, inverted);
}

/**
 * \brief Set HAX level
 *
 * Sets output level on a pin
 *
 * \param[in] level true  = Pin level set to "high" state
 *                  false = Pin level set to "low" state
 */
static inline void HAX_set_level(const bool level)
{
	PORTA_set_pin_level(7, level);
}

/**
 * \brief Toggle output level on HAX
 *
 * Toggle the pin level
 */
static inline void HAX_toggle_level()
{
	PORTA_toggle_pin_level(7);
}

/**
 * \brief Get level on HAX
 *
 * Reads the level on a pin
 */
static inline bool HAX_get_level()
{
	return PORTA_get_pin_level(7);
}

/**
 * \brief Set PB0 pull mode
 *
 * Configure pin to pull up, down or disable pull mode, supported pull
 * modes are defined by device used
 *
 * \param[in] pull_mode Pin pull mode
 */
static inline void PB0_set_pull_mode(const enum port_pull_mode pull_mode)
{
	PORTB_set_pin_pull_mode(0, pull_mode);
}

/**
 * \brief Set PB0 data direction
 *
 * Select if the pin data direction is input, output or disabled.
 * If disabled state is not possible, this function throws an assert.
 *
 * \param[in] direction PORT_DIR_IN  = Data direction in
 *                      PORT_DIR_OUT = Data direction out
 *                      PORT_DIR_OFF = Disables the pin
 *                      (low power state)
 */
static inline void PB0_set_dir(const enum port_dir dir)
{
	PORTB_set_pin_dir(0, dir);
}

/**
 * \brief Set PB0 input/sense configuration
 *
 * Enable/disable PB0 digital input buffer and pin change interrupt,
 * select pin interrupt edge/level sensing mode
 *
 * \param[in] isc PORT_ISC_INTDISABLE_gc    = Iterrupt disabled but input buffer enabled
 *                PORT_ISC_BOTHEDGES_gc     = Sense Both Edges
 *                PORT_ISC_RISING_gc        = Sense Rising Edge
 *                PORT_ISC_FALLING_gc       = Sense Falling Edge
 *                PORT_ISC_INPUT_DISABLE_gc = Digital Input Buffer disabled
 *                PORT_ISC_LEVEL_gc         = Sense low Level
 */
static inline void PB0_set_isc(const PORT_ISC_t isc)
{
	PORTB_pin_set_isc(0, isc);
}

/**
 * \brief Set PB0 inverted mode
 *
 * Enable or disable inverted I/O on a pin
 *
 * \param[in] inverted true  = I/O on PB0 is inverted
 *                     false = I/O on PB0 is not inverted
 */
static inline void PB0_set_inverted(const bool inverted)
{
	PORTB_pin_set_inverted(0, inverted);
}

/**
 * \brief Set PB0 level
 *
 * Sets output level on a pin
 *
 * \param[in] level true  = Pin level set to "high" state
 *                  false = Pin level set to "low" state
 */
static inline void PB0_set_level(const bool level)
{
	PORTB_set_pin_level(0, level);
}

/**
 * \brief Toggle output level on PB0
 *
 * Toggle the pin level
 */
static inline void PB0_toggle_level()
{
	PORTB_toggle_pin_level(0);
}

/**
 * \brief Get level on PB0
 *
 * Reads the level on a pin
 */
static inline bool PB0_get_level()
{
	return PORTB_get_pin_level(0);
}

/**
 * \brief Set PB1 pull mode
 *
 * Configure pin to pull up, down or disable pull mode, supported pull
 * modes are defined by device used
 *
 * \param[in] pull_mode Pin pull mode
 */
static inline void PB1_set_pull_mode(const enum port_pull_mode pull_mode)
{
	PORTB_set_pin_pull_mode(1, pull_mode);
}

/**
 * \brief Set PB1 data direction
 *
 * Select if the pin data direction is input, output or disabled.
 * If disabled state is not possible, this function throws an assert.
 *
 * \param[in] direction PORT_DIR_IN  = Data direction in
 *                      PORT_DIR_OUT = Data direction out
 *                      PORT_DIR_OFF = Disables the pin
 *                      (low power state)
 */
static inline void PB1_set_dir(const enum port_dir dir)
{
	PORTB_set_pin_dir(1, dir);
}

/**
 * \brief Set PB1 input/sense configuration
 *
 * Enable/disable PB1 digital input buffer and pin change interrupt,
 * select pin interrupt edge/level sensing mode
 *
 * \param[in] isc PORT_ISC_INTDISABLE_gc    = Iterrupt disabled but input buffer enabled
 *                PORT_ISC_BOTHEDGES_gc     = Sense Both Edges
 *                PORT_ISC_RISING_gc        = Sense Rising Edge
 *                PORT_ISC_FALLING_gc       = Sense Falling Edge
 *                PORT_ISC_INPUT_DISABLE_gc = Digital Input Buffer disabled
 *                PORT_ISC_LEVEL_gc         = Sense low Level
 */
static inline void PB1_set_isc(const PORT_ISC_t isc)
{
	PORTB_pin_set_isc(1, isc);
}

/**
 * \brief Set PB1 inverted mode
 *
 * Enable or disable inverted I/O on a pin
 *
 * \param[in] inverted true  = I/O on PB1 is inverted
 *                     false = I/O on PB1 is not inverted
 */
static inline void PB1_set_inverted(const bool inverted)
{
	PORTB_pin_set_inverted(1, inverted);
}

/**
 * \brief Set PB1 level
 *
 * Sets output level on a pin
 *
 * \param[in] level true  = Pin level set to "high" state
 *                  false = Pin level set to "low" state
 */
static inline void PB1_set_level(const bool level)
{
	PORTB_set_pin_level(1, level);
}

/**
 * \brief Toggle output level on PB1
 *
 * Toggle the pin level
 */
static inline void PB1_toggle_level()
{
	PORTB_toggle_pin_level(1);
}

/**
 * \brief Get level on PB1
 *
 * Reads the level on a pin
 */
static inline bool PB1_get_level()
{
	return PORTB_get_pin_level(1);
}

/**
 * \brief Set C0 pull mode
 *
 * Configure pin to pull up, down or disable pull mode, supported pull
 * modes are defined by device used
 *
 * \param[in] pull_mode Pin pull mode
 */
static inline void C0_set_pull_mode(const enum port_pull_mode pull_mode)
{
	PORTB_set_pin_pull_mode(2, pull_mode);
}

/**
 * \brief Set C0 data direction
 *
 * Select if the pin data direction is input, output or disabled.
 * If disabled state is not possible, this function throws an assert.
 *
 * \param[in] direction PORT_DIR_IN  = Data direction in
 *                      PORT_DIR_OUT = Data direction out
 *                      PORT_DIR_OFF = Disables the pin
 *                      (low power state)
 */
static inline void C0_set_dir(const enum port_dir dir)
{
	PORTB_set_pin_dir(2, dir);
}

/**
 * \brief Set C0 input/sense configuration
 *
 * Enable/disable C0 digital input buffer and pin change interrupt,
 * select pin interrupt edge/level sensing mode
 *
 * \param[in] isc PORT_ISC_INTDISABLE_gc    = Iterrupt disabled but input buffer enabled
 *                PORT_ISC_BOTHEDGES_gc     = Sense Both Edges
 *                PORT_ISC_RISING_gc        = Sense Rising Edge
 *                PORT_ISC_FALLING_gc       = Sense Falling Edge
 *                PORT_ISC_INPUT_DISABLE_gc = Digital Input Buffer disabled
 *                PORT_ISC_LEVEL_gc         = Sense low Level
 */
static inline void C0_set_isc(const PORT_ISC_t isc)
{
	PORTB_pin_set_isc(2, isc);
}

/**
 * \brief Set C0 inverted mode
 *
 * Enable or disable inverted I/O on a pin
 *
 * \param[in] inverted true  = I/O on C0 is inverted
 *                     false = I/O on C0 is not inverted
 */
static inline void C0_set_inverted(const bool inverted)
{
	PORTB_pin_set_inverted(2, inverted);
}

/**
 * \brief Set C0 level
 *
 * Sets output level on a pin
 *
 * \param[in] level true  = Pin level set to "high" state
 *                  false = Pin level set to "low" state
 */
static inline void C0_set_level(const bool level)
{
	PORTB_set_pin_level(2, level);
}

/**
 * \brief Toggle output level on C0
 *
 * Toggle the pin level
 */
static inline void C0_toggle_level()
{
	PORTB_toggle_pin_level(2);
}

/**
 * \brief Get level on C0
 *
 * Reads the level on a pin
 */
static inline bool C0_get_level()
{
	return PORTB_get_pin_level(2);
}

/**
 * \brief Set C5 pull mode
 *
 * Configure pin to pull up, down or disable pull mode, supported pull
 * modes are defined by device used
 *
 * \param[in] pull_mode Pin pull mode
 */
static inline void C5_set_pull_mode(const enum port_pull_mode pull_mode)
{
	PORTB_set_pin_pull_mode(3, pull_mode);
}

/**
 * \brief Set C5 data direction
 *
 * Select if the pin data direction is input, output or disabled.
 * If disabled state is not possible, this function throws an assert.
 *
 * \param[in] direction PORT_DIR_IN  = Data direction in
 *                      PORT_DIR_OUT = Data direction out
 *                      PORT_DIR_OFF = Disables the pin
 *                      (low power state)
 */
static inline void C5_set_dir(const enum port_dir dir)
{
	PORTB_set_pin_dir(3, dir);
}

/**
 * \brief Set C5 input/sense configuration
 *
 * Enable/disable C5 digital input buffer and pin change interrupt,
 * select pin interrupt edge/level sensing mode
 *
 * \param[in] isc PORT_ISC_INTDISABLE_gc    = Iterrupt disabled but input buffer enabled
 *                PORT_ISC_BOTHEDGES_gc     = Sense Both Edges
 *                PORT_ISC_RISING_gc        = Sense Rising Edge
 *                PORT_ISC_FALLING_gc       = Sense Falling Edge
 *                PORT_ISC_INPUT_DISABLE_gc = Digital Input Buffer disabled
 *                PORT_ISC_LEVEL_gc         = Sense low Level
 */
static inline void C5_set_isc(const PORT_ISC_t isc)
{
	PORTB_pin_set_isc(3, isc);
}

/**
 * \brief Set C5 inverted mode
 *
 * Enable or disable inverted I/O on a pin
 *
 * \param[in] inverted true  = I/O on C5 is inverted
 *                     false = I/O on C5 is not inverted
 */
static inline void C5_set_inverted(const bool inverted)
{
	PORTB_pin_set_inverted(3, inverted);
}

/**
 * \brief Set C5 level
 *
 * Sets output level on a pin
 *
 * \param[in] level true  = Pin level set to "high" state
 *                  false = Pin level set to "low" state
 */
static inline void C5_set_level(const bool level)
{
	PORTB_set_pin_level(3, level);
}

/**
 * \brief Toggle output level on C5
 *
 * Toggle the pin level
 */
static inline void C5_toggle_level()
{
	PORTB_toggle_pin_level(3);
}

/**
 * \brief Get level on C5
 *
 * Reads the level on a pin
 */
static inline bool C5_get_level()
{
	return PORTB_get_pin_level(3);
}

/**
 * \brief Set C4 pull mode
 *
 * Configure pin to pull up, down or disable pull mode, supported pull
 * modes are defined by device used
 *
 * \param[in] pull_mode Pin pull mode
 */
static inline void C4_set_pull_mode(const enum port_pull_mode pull_mode)
{
	PORTB_set_pin_pull_mode(4, pull_mode);
}

/**
 * \brief Set C4 data direction
 *
 * Select if the pin data direction is input, output or disabled.
 * If disabled state is not possible, this function throws an assert.
 *
 * \param[in] direction PORT_DIR_IN  = Data direction in
 *                      PORT_DIR_OUT = Data direction out
 *                      PORT_DIR_OFF = Disables the pin
 *                      (low power state)
 */
static inline void C4_set_dir(const enum port_dir dir)
{
	PORTB_set_pin_dir(4, dir);
}

/**
 * \brief Set C4 input/sense configuration
 *
 * Enable/disable C4 digital input buffer and pin change interrupt,
 * select pin interrupt edge/level sensing mode
 *
 * \param[in] isc PORT_ISC_INTDISABLE_gc    = Iterrupt disabled but input buffer enabled
 *                PORT_ISC_BOTHEDGES_gc     = Sense Both Edges
 *                PORT_ISC_RISING_gc        = Sense Rising Edge
 *                PORT_ISC_FALLING_gc       = Sense Falling Edge
 *                PORT_ISC_INPUT_DISABLE_gc = Digital Input Buffer disabled
 *                PORT_ISC_LEVEL_gc         = Sense low Level
 */
static inline void C4_set_isc(const PORT_ISC_t isc)
{
	PORTB_pin_set_isc(4, isc);
}

/**
 * \brief Set C4 inverted mode
 *
 * Enable or disable inverted I/O on a pin
 *
 * \param[in] inverted true  = I/O on C4 is inverted
 *                     false = I/O on C4 is not inverted
 */
static inline void C4_set_inverted(const bool inverted)
{
	PORTB_pin_set_inverted(4, inverted);
}

/**
 * \brief Set C4 level
 *
 * Sets output level on a pin
 *
 * \param[in] level true  = Pin level set to "high" state
 *                  false = Pin level set to "low" state
 */
static inline void C4_set_level(const bool level)
{
	PORTB_set_pin_level(4, level);
}

/**
 * \brief Toggle output level on C4
 *
 * Toggle the pin level
 */
static inline void C4_toggle_level()
{
	PORTB_toggle_pin_level(4);
}

/**
 * \brief Get level on C4
 *
 * Reads the level on a pin
 */
static inline bool C4_get_level()
{
	return PORTB_get_pin_level(4);
}

/**
 * \brief Set C2 pull mode
 *
 * Configure pin to pull up, down or disable pull mode, supported pull
 * modes are defined by device used
 *
 * \param[in] pull_mode Pin pull mode
 */
static inline void C2_set_pull_mode(const enum port_pull_mode pull_mode)
{
	PORTB_set_pin_pull_mode(5, pull_mode);
}

/**
 * \brief Set C2 data direction
 *
 * Select if the pin data direction is input, output or disabled.
 * If disabled state is not possible, this function throws an assert.
 *
 * \param[in] direction PORT_DIR_IN  = Data direction in
 *                      PORT_DIR_OUT = Data direction out
 *                      PORT_DIR_OFF = Disables the pin
 *                      (low power state)
 */
static inline void C2_set_dir(const enum port_dir dir)
{
	PORTB_set_pin_dir(5, dir);
}

/**
 * \brief Set C2 input/sense configuration
 *
 * Enable/disable C2 digital input buffer and pin change interrupt,
 * select pin interrupt edge/level sensing mode
 *
 * \param[in] isc PORT_ISC_INTDISABLE_gc    = Iterrupt disabled but input buffer enabled
 *                PORT_ISC_BOTHEDGES_gc     = Sense Both Edges
 *                PORT_ISC_RISING_gc        = Sense Rising Edge
 *                PORT_ISC_FALLING_gc       = Sense Falling Edge
 *                PORT_ISC_INPUT_DISABLE_gc = Digital Input Buffer disabled
 *                PORT_ISC_LEVEL_gc         = Sense low Level
 */
static inline void C2_set_isc(const PORT_ISC_t isc)
{
	PORTB_pin_set_isc(5, isc);
}

/**
 * \brief Set C2 inverted mode
 *
 * Enable or disable inverted I/O on a pin
 *
 * \param[in] inverted true  = I/O on C2 is inverted
 *                     false = I/O on C2 is not inverted
 */
static inline void C2_set_inverted(const bool inverted)
{
	PORTB_pin_set_inverted(5, inverted);
}

/**
 * \brief Set C2 level
 *
 * Sets output level on a pin
 *
 * \param[in] level true  = Pin level set to "high" state
 *                  false = Pin level set to "low" state
 */
static inline void C2_set_level(const bool level)
{
	PORTB_set_pin_level(5, level);
}

/**
 * \brief Toggle output level on C2
 *
 * Toggle the pin level
 */
static inline void C2_toggle_level()
{
	PORTB_toggle_pin_level(5);
}

/**
 * \brief Get level on C2
 *
 * Reads the level on a pin
 */
static inline bool C2_get_level()
{
	return PORTB_get_pin_level(5);
}

/**
 * \brief Set C1 pull mode
 *
 * Configure pin to pull up, down or disable pull mode, supported pull
 * modes are defined by device used
 *
 * \param[in] pull_mode Pin pull mode
 */
static inline void C1_set_pull_mode(const enum port_pull_mode pull_mode)
{
	PORTB_set_pin_pull_mode(6, pull_mode);
}

/**
 * \brief Set C1 data direction
 *
 * Select if the pin data direction is input, output or disabled.
 * If disabled state is not possible, this function throws an assert.
 *
 * \param[in] direction PORT_DIR_IN  = Data direction in
 *                      PORT_DIR_OUT = Data direction out
 *                      PORT_DIR_OFF = Disables the pin
 *                      (low power state)
 */
static inline void C1_set_dir(const enum port_dir dir)
{
	PORTB_set_pin_dir(6, dir);
}

/**
 * \brief Set C1 input/sense configuration
 *
 * Enable/disable C1 digital input buffer and pin change interrupt,
 * select pin interrupt edge/level sensing mode
 *
 * \param[in] isc PORT_ISC_INTDISABLE_gc    = Iterrupt disabled but input buffer enabled
 *                PORT_ISC_BOTHEDGES_gc     = Sense Both Edges
 *                PORT_ISC_RISING_gc        = Sense Rising Edge
 *                PORT_ISC_FALLING_gc       = Sense Falling Edge
 *                PORT_ISC_INPUT_DISABLE_gc = Digital Input Buffer disabled
 *                PORT_ISC_LEVEL_gc         = Sense low Level
 */
static inline void C1_set_isc(const PORT_ISC_t isc)
{
	PORTB_pin_set_isc(6, isc);
}

/**
 * \brief Set C1 inverted mode
 *
 * Enable or disable inverted I/O on a pin
 *
 * \param[in] inverted true  = I/O on C1 is inverted
 *                     false = I/O on C1 is not inverted
 */
static inline void C1_set_inverted(const bool inverted)
{
	PORTB_pin_set_inverted(6, inverted);
}

/**
 * \brief Set C1 level
 *
 * Sets output level on a pin
 *
 * \param[in] level true  = Pin level set to "high" state
 *                  false = Pin level set to "low" state
 */
static inline void C1_set_level(const bool level)
{
	PORTB_set_pin_level(6, level);
}

/**
 * \brief Toggle output level on C1
 *
 * Toggle the pin level
 */
static inline void C1_toggle_level()
{
	PORTB_toggle_pin_level(6);
}

/**
 * \brief Get level on C1
 *
 * Reads the level on a pin
 */
static inline bool C1_get_level()
{
	return PORTB_get_pin_level(6);
}

/**
 * \brief Set C3 pull mode
 *
 * Configure pin to pull up, down or disable pull mode, supported pull
 * modes are defined by device used
 *
 * \param[in] pull_mode Pin pull mode
 */
static inline void C3_set_pull_mode(const enum port_pull_mode pull_mode)
{
	PORTB_set_pin_pull_mode(7, pull_mode);
}

/**
 * \brief Set C3 data direction
 *
 * Select if the pin data direction is input, output or disabled.
 * If disabled state is not possible, this function throws an assert.
 *
 * \param[in] direction PORT_DIR_IN  = Data direction in
 *                      PORT_DIR_OUT = Data direction out
 *                      PORT_DIR_OFF = Disables the pin
 *                      (low power state)
 */
static inline void C3_set_dir(const enum port_dir dir)
{
	PORTB_set_pin_dir(7, dir);
}

/**
 * \brief Set C3 input/sense configuration
 *
 * Enable/disable C3 digital input buffer and pin change interrupt,
 * select pin interrupt edge/level sensing mode
 *
 * \param[in] isc PORT_ISC_INTDISABLE_gc    = Iterrupt disabled but input buffer enabled
 *                PORT_ISC_BOTHEDGES_gc     = Sense Both Edges
 *                PORT_ISC_RISING_gc        = Sense Rising Edge
 *                PORT_ISC_FALLING_gc       = Sense Falling Edge
 *                PORT_ISC_INPUT_DISABLE_gc = Digital Input Buffer disabled
 *                PORT_ISC_LEVEL_gc         = Sense low Level
 */
static inline void C3_set_isc(const PORT_ISC_t isc)
{
	PORTB_pin_set_isc(7, isc);
}

/**
 * \brief Set C3 inverted mode
 *
 * Enable or disable inverted I/O on a pin
 *
 * \param[in] inverted true  = I/O on C3 is inverted
 *                     false = I/O on C3 is not inverted
 */
static inline void C3_set_inverted(const bool inverted)
{
	PORTB_pin_set_inverted(7, inverted);
}

/**
 * \brief Set C3 level
 *
 * Sets output level on a pin
 *
 * \param[in] level true  = Pin level set to "high" state
 *                  false = Pin level set to "low" state
 */
static inline void C3_set_level(const bool level)
{
	PORTB_set_pin_level(7, level);
}

/**
 * \brief Toggle output level on C3
 *
 * Toggle the pin level
 */
static inline void C3_toggle_level()
{
	PORTB_toggle_pin_level(7);
}

/**
 * \brief Get level on C3
 *
 * Reads the level on a pin
 */
static inline bool C3_get_level()
{
	return PORTB_get_pin_level(7);
}

/**
 * \brief Set Xp pull mode
 *
 * Configure pin to pull up, down or disable pull mode, supported pull
 * modes are defined by device used
 *
 * \param[in] pull_mode Pin pull mode
 */
static inline void Xp_set_pull_mode(const enum port_pull_mode pull_mode)
{
	PORTC_set_pin_pull_mode(0, pull_mode);
}

/**
 * \brief Set Xp data direction
 *
 * Select if the pin data direction is input, output or disabled.
 * If disabled state is not possible, this function throws an assert.
 *
 * \param[in] direction PORT_DIR_IN  = Data direction in
 *                      PORT_DIR_OUT = Data direction out
 *                      PORT_DIR_OFF = Disables the pin
 *                      (low power state)
 */
static inline void Xp_set_dir(const enum port_dir dir)
{
	PORTC_set_pin_dir(0, dir);
}

/**
 * \brief Set Xp input/sense configuration
 *
 * Enable/disable Xp digital input buffer and pin change interrupt,
 * select pin interrupt edge/level sensing mode
 *
 * \param[in] isc PORT_ISC_INTDISABLE_gc    = Iterrupt disabled but input buffer enabled
 *                PORT_ISC_BOTHEDGES_gc     = Sense Both Edges
 *                PORT_ISC_RISING_gc        = Sense Rising Edge
 *                PORT_ISC_FALLING_gc       = Sense Falling Edge
 *                PORT_ISC_INPUT_DISABLE_gc = Digital Input Buffer disabled
 *                PORT_ISC_LEVEL_gc         = Sense low Level
 */
static inline void Xp_set_isc(const PORT_ISC_t isc)
{
	PORTC_pin_set_isc(0, isc);
}

/**
 * \brief Set Xp inverted mode
 *
 * Enable or disable inverted I/O on a pin
 *
 * \param[in] inverted true  = I/O on Xp is inverted
 *                     false = I/O on Xp is not inverted
 */
static inline void Xp_set_inverted(const bool inverted)
{
	PORTC_pin_set_inverted(0, inverted);
}

/**
 * \brief Set Xp level
 *
 * Sets output level on a pin
 *
 * \param[in] level true  = Pin level set to "high" state
 *                  false = Pin level set to "low" state
 */
static inline void Xp_set_level(const bool level)
{
	PORTC_set_pin_level(0, level);
}

/**
 * \brief Toggle output level on Xp
 *
 * Toggle the pin level
 */
static inline void Xp_toggle_level()
{
	PORTC_toggle_pin_level(0);
}

/**
 * \brief Get level on Xp
 *
 * Reads the level on a pin
 */
static inline bool Xp_get_level()
{
	return PORTC_get_pin_level(0);
}

/**
 * \brief Set Yp pull mode
 *
 * Configure pin to pull up, down or disable pull mode, supported pull
 * modes are defined by device used
 *
 * \param[in] pull_mode Pin pull mode
 */
static inline void Yp_set_pull_mode(const enum port_pull_mode pull_mode)
{
	PORTC_set_pin_pull_mode(1, pull_mode);
}

/**
 * \brief Set Yp data direction
 *
 * Select if the pin data direction is input, output or disabled.
 * If disabled state is not possible, this function throws an assert.
 *
 * \param[in] direction PORT_DIR_IN  = Data direction in
 *                      PORT_DIR_OUT = Data direction out
 *                      PORT_DIR_OFF = Disables the pin
 *                      (low power state)
 */
static inline void Yp_set_dir(const enum port_dir dir)
{
	PORTC_set_pin_dir(1, dir);
}

/**
 * \brief Set Yp input/sense configuration
 *
 * Enable/disable Yp digital input buffer and pin change interrupt,
 * select pin interrupt edge/level sensing mode
 *
 * \param[in] isc PORT_ISC_INTDISABLE_gc    = Iterrupt disabled but input buffer enabled
 *                PORT_ISC_BOTHEDGES_gc     = Sense Both Edges
 *                PORT_ISC_RISING_gc        = Sense Rising Edge
 *                PORT_ISC_FALLING_gc       = Sense Falling Edge
 *                PORT_ISC_INPUT_DISABLE_gc = Digital Input Buffer disabled
 *                PORT_ISC_LEVEL_gc         = Sense low Level
 */
static inline void Yp_set_isc(const PORT_ISC_t isc)
{
	PORTC_pin_set_isc(1, isc);
}

/**
 * \brief Set Yp inverted mode
 *
 * Enable or disable inverted I/O on a pin
 *
 * \param[in] inverted true  = I/O on Yp is inverted
 *                     false = I/O on Yp is not inverted
 */
static inline void Yp_set_inverted(const bool inverted)
{
	PORTC_pin_set_inverted(1, inverted);
}

/**
 * \brief Set Yp level
 *
 * Sets output level on a pin
 *
 * \param[in] level true  = Pin level set to "high" state
 *                  false = Pin level set to "low" state
 */
static inline void Yp_set_level(const bool level)
{
	PORTC_set_pin_level(1, level);
}

/**
 * \brief Toggle output level on Yp
 *
 * Toggle the pin level
 */
static inline void Yp_toggle_level()
{
	PORTC_toggle_pin_level(1);
}

/**
 * \brief Get level on Yp
 *
 * Reads the level on a pin
 */
static inline bool Yp_get_level()
{
	return PORTC_get_pin_level(1);
}

/**
 * \brief Set Xm pull mode
 *
 * Configure pin to pull up, down or disable pull mode, supported pull
 * modes are defined by device used
 *
 * \param[in] pull_mode Pin pull mode
 */
static inline void Xm_set_pull_mode(const enum port_pull_mode pull_mode)
{
	PORTC_set_pin_pull_mode(2, pull_mode);
}

/**
 * \brief Set Xm data direction
 *
 * Select if the pin data direction is input, output or disabled.
 * If disabled state is not possible, this function throws an assert.
 *
 * \param[in] direction PORT_DIR_IN  = Data direction in
 *                      PORT_DIR_OUT = Data direction out
 *                      PORT_DIR_OFF = Disables the pin
 *                      (low power state)
 */
static inline void Xm_set_dir(const enum port_dir dir)
{
	PORTC_set_pin_dir(2, dir);
}

/**
 * \brief Set Xm input/sense configuration
 *
 * Enable/disable Xm digital input buffer and pin change interrupt,
 * select pin interrupt edge/level sensing mode
 *
 * \param[in] isc PORT_ISC_INTDISABLE_gc    = Iterrupt disabled but input buffer enabled
 *                PORT_ISC_BOTHEDGES_gc     = Sense Both Edges
 *                PORT_ISC_RISING_gc        = Sense Rising Edge
 *                PORT_ISC_FALLING_gc       = Sense Falling Edge
 *                PORT_ISC_INPUT_DISABLE_gc = Digital Input Buffer disabled
 *                PORT_ISC_LEVEL_gc         = Sense low Level
 */
static inline void Xm_set_isc(const PORT_ISC_t isc)
{
	PORTC_pin_set_isc(2, isc);
}

/**
 * \brief Set Xm inverted mode
 *
 * Enable or disable inverted I/O on a pin
 *
 * \param[in] inverted true  = I/O on Xm is inverted
 *                     false = I/O on Xm is not inverted
 */
static inline void Xm_set_inverted(const bool inverted)
{
	PORTC_pin_set_inverted(2, inverted);
}

/**
 * \brief Set Xm level
 *
 * Sets output level on a pin
 *
 * \param[in] level true  = Pin level set to "high" state
 *                  false = Pin level set to "low" state
 */
static inline void Xm_set_level(const bool level)
{
	PORTC_set_pin_level(2, level);
}

/**
 * \brief Toggle output level on Xm
 *
 * Toggle the pin level
 */
static inline void Xm_toggle_level()
{
	PORTC_toggle_pin_level(2);
}

/**
 * \brief Get level on Xm
 *
 * Reads the level on a pin
 */
static inline bool Xm_get_level()
{
	return PORTC_get_pin_level(2);
}

/**
 * \brief Set Ym pull mode
 *
 * Configure pin to pull up, down or disable pull mode, supported pull
 * modes are defined by device used
 *
 * \param[in] pull_mode Pin pull mode
 */
static inline void Ym_set_pull_mode(const enum port_pull_mode pull_mode)
{
	PORTC_set_pin_pull_mode(3, pull_mode);
}

/**
 * \brief Set Ym data direction
 *
 * Select if the pin data direction is input, output or disabled.
 * If disabled state is not possible, this function throws an assert.
 *
 * \param[in] direction PORT_DIR_IN  = Data direction in
 *                      PORT_DIR_OUT = Data direction out
 *                      PORT_DIR_OFF = Disables the pin
 *                      (low power state)
 */
static inline void Ym_set_dir(const enum port_dir dir)
{
	PORTC_set_pin_dir(3, dir);
}

/**
 * \brief Set Ym input/sense configuration
 *
 * Enable/disable Ym digital input buffer and pin change interrupt,
 * select pin interrupt edge/level sensing mode
 *
 * \param[in] isc PORT_ISC_INTDISABLE_gc    = Iterrupt disabled but input buffer enabled
 *                PORT_ISC_BOTHEDGES_gc     = Sense Both Edges
 *                PORT_ISC_RISING_gc        = Sense Rising Edge
 *                PORT_ISC_FALLING_gc       = Sense Falling Edge
 *                PORT_ISC_INPUT_DISABLE_gc = Digital Input Buffer disabled
 *                PORT_ISC_LEVEL_gc         = Sense low Level
 */
static inline void Ym_set_isc(const PORT_ISC_t isc)
{
	PORTC_pin_set_isc(3, isc);
}

/**
 * \brief Set Ym inverted mode
 *
 * Enable or disable inverted I/O on a pin
 *
 * \param[in] inverted true  = I/O on Ym is inverted
 *                     false = I/O on Ym is not inverted
 */
static inline void Ym_set_inverted(const bool inverted)
{
	PORTC_pin_set_inverted(3, inverted);
}

/**
 * \brief Set Ym level
 *
 * Sets output level on a pin
 *
 * \param[in] level true  = Pin level set to "high" state
 *                  false = Pin level set to "low" state
 */
static inline void Ym_set_level(const bool level)
{
	PORTC_set_pin_level(3, level);
}

/**
 * \brief Toggle output level on Ym
 *
 * Toggle the pin level
 */
static inline void Ym_toggle_level()
{
	PORTC_toggle_pin_level(3);
}

/**
 * \brief Get level on Ym
 *
 * Reads the level on a pin
 */
static inline bool Ym_get_level()
{
	return PORTC_get_pin_level(3);
}

/**
 * \brief Set KEY_INT pull mode
 *
 * Configure pin to pull up, down or disable pull mode, supported pull
 * modes are defined by device used
 *
 * \param[in] pull_mode Pin pull mode
 */
static inline void KEY_INT_set_pull_mode(const enum port_pull_mode pull_mode)
{
	PORTC_set_pin_pull_mode(5, pull_mode);
}

/**
 * \brief Set KEY_INT data direction
 *
 * Select if the pin data direction is input, output or disabled.
 * If disabled state is not possible, this function throws an assert.
 *
 * \param[in] direction PORT_DIR_IN  = Data direction in
 *                      PORT_DIR_OUT = Data direction out
 *                      PORT_DIR_OFF = Disables the pin
 *                      (low power state)
 */
static inline void KEY_INT_set_dir(const enum port_dir dir)
{
	PORTC_set_pin_dir(5, dir);
}

/**
 * \brief Set KEY_INT input/sense configuration
 *
 * Enable/disable KEY_INT digital input buffer and pin change interrupt,
 * select pin interrupt edge/level sensing mode
 *
 * \param[in] isc PORT_ISC_INTDISABLE_gc    = Iterrupt disabled but input buffer enabled
 *                PORT_ISC_BOTHEDGES_gc     = Sense Both Edges
 *                PORT_ISC_RISING_gc        = Sense Rising Edge
 *                PORT_ISC_FALLING_gc       = Sense Falling Edge
 *                PORT_ISC_INPUT_DISABLE_gc = Digital Input Buffer disabled
 *                PORT_ISC_LEVEL_gc         = Sense low Level
 */
static inline void KEY_INT_set_isc(const PORT_ISC_t isc)
{
	PORTC_pin_set_isc(5, isc);
}

/**
 * \brief Set KEY_INT inverted mode
 *
 * Enable or disable inverted I/O on a pin
 *
 * \param[in] inverted true  = I/O on KEY_INT is inverted
 *                     false = I/O on KEY_INT is not inverted
 */
static inline void KEY_INT_set_inverted(const bool inverted)
{
	PORTC_pin_set_inverted(5, inverted);
}

/**
 * \brief Set KEY_INT level
 *
 * Sets output level on a pin
 *
 * \param[in] level true  = Pin level set to "high" state
 *                  false = Pin level set to "low" state
 */
static inline void KEY_INT_set_level(const bool level)
{
	PORTC_set_pin_level(5, level);
}

/**
 * \brief Toggle output level on KEY_INT
 *
 * Toggle the pin level
 */
static inline void KEY_INT_toggle_level()
{
	PORTC_toggle_pin_level(5);
}

/**
 * \brief Get level on KEY_INT
 *
 * Reads the level on a pin
 */
static inline bool KEY_INT_get_level()
{
	return PORTC_get_pin_level(5);
}

#endif /* ATMEL_START_PINS_H_INCLUDED */
